CircuitSetup/Time-Circuits-Display/Images/enclosure_sanding2.jpg

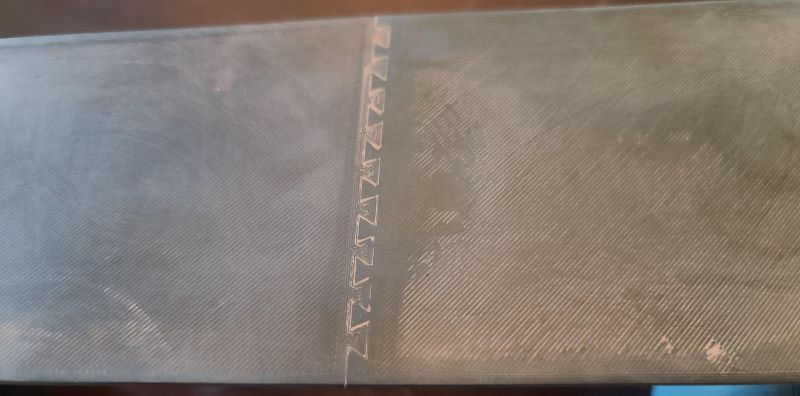
Images/enclosure_sanding2.jpg
