CircuitSetup/Time-Circuits-Display/Images/enclosure_sanding.jpg

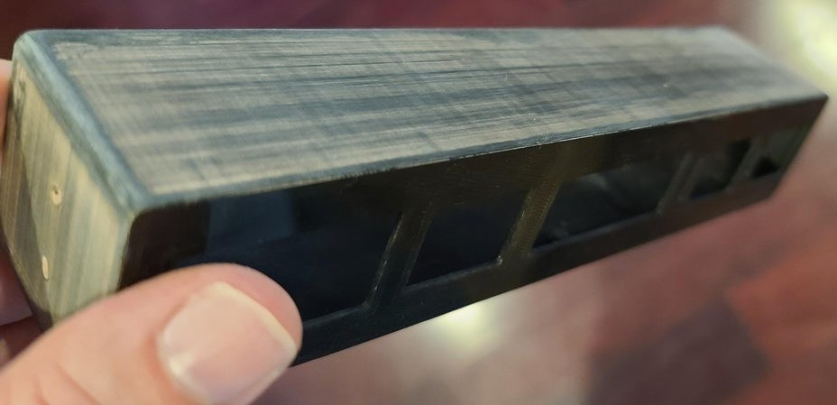
Images/enclosure_sanding.jpg
