CircuitSetup/Time-Circuits-Display/Images/keypad_enter_button.jpg

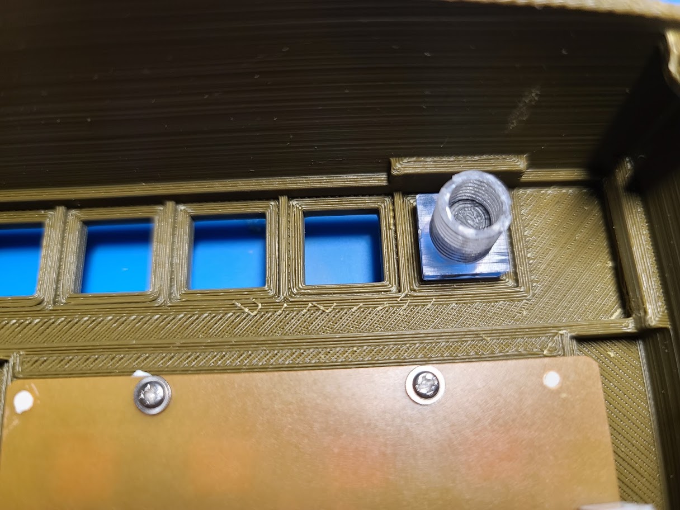
Images/keypad_enter_button.jpg
