CircuitSetup/Time-Circuits-Display/Images/keypad_lenses.jpg

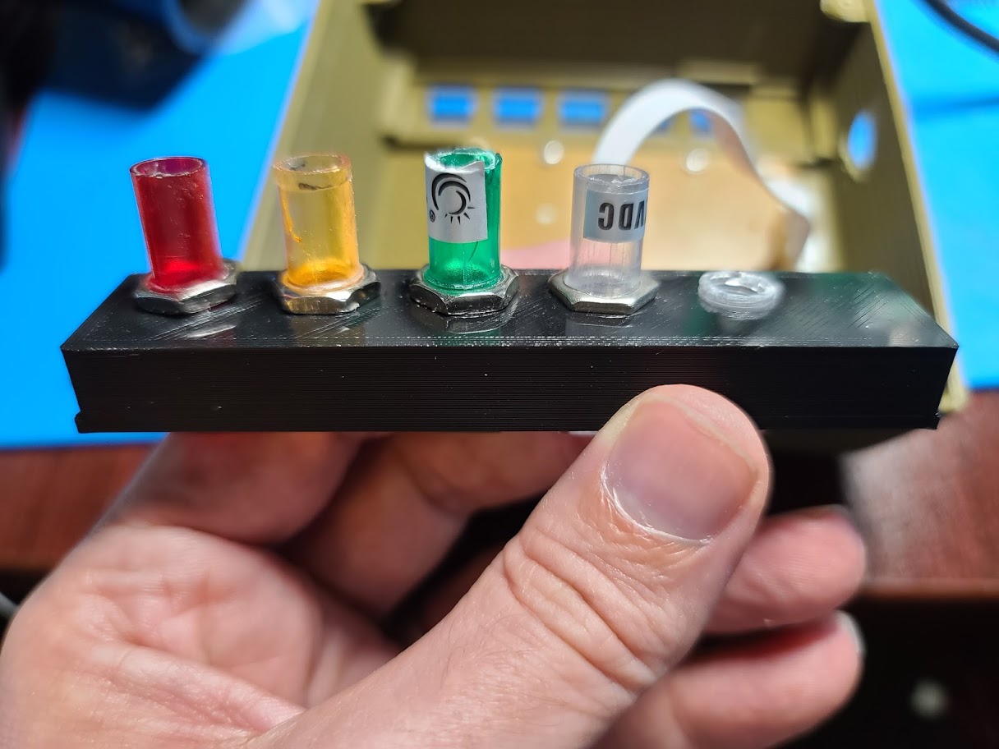
Images/keypad_lenses.jpg
