CircuitSetup/Time-Circuits-Display/Images/resize/enclosure_sanding.jpg

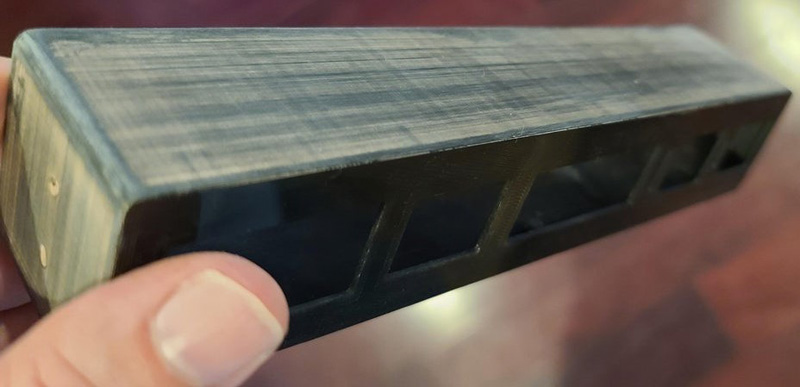
Images/resize/enclosure_sanding.jpg
