CircuitSetup/Time-Circuits-Display/Images/resize/tcd_back2.jpg

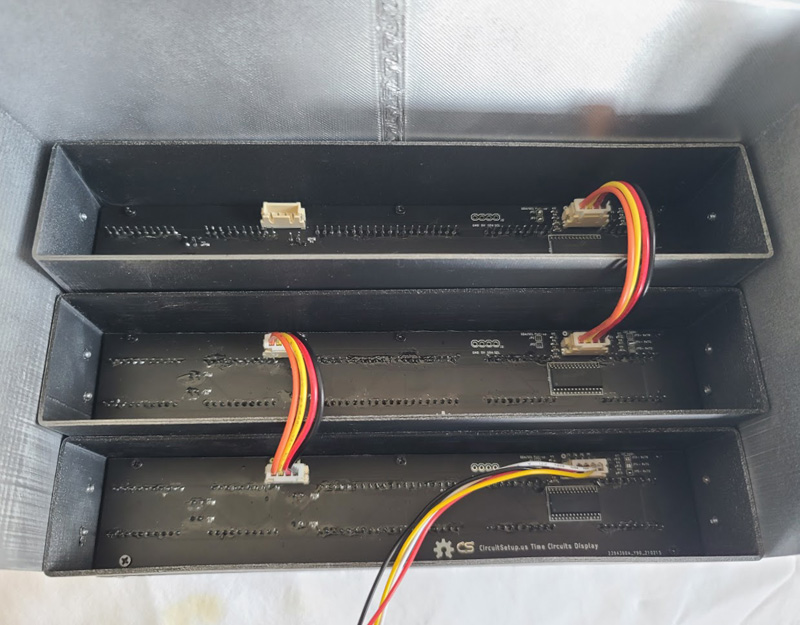
Images/resize/tcd_back2.jpg
