CircuitSetup/Time-Circuits-Display/Images/resize/tcd_bare.jpg

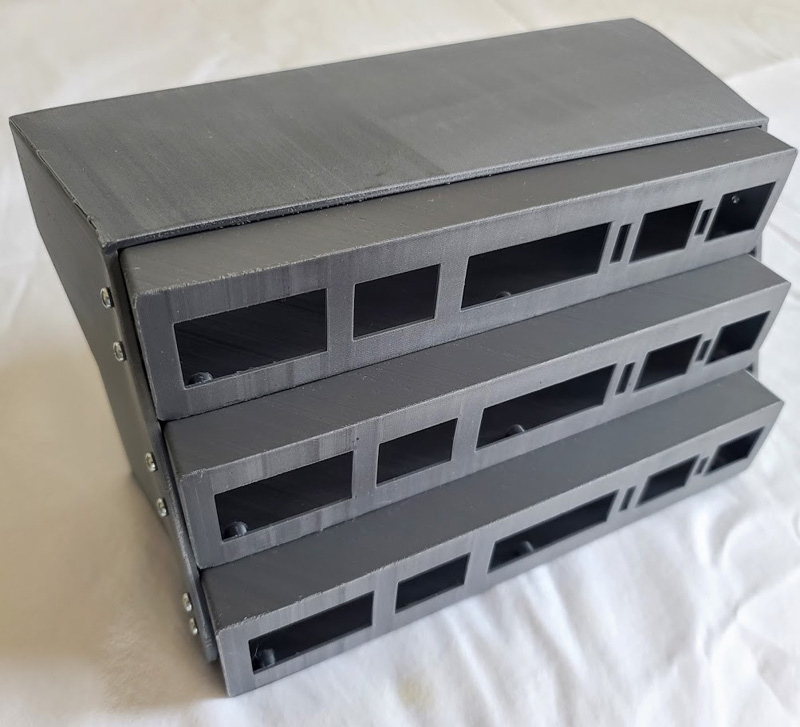
Images/resize/tcd_bare.jpg
