CircuitSetup/Time-Circuits-Display/Images/resize/tcd_bare_back.jpg

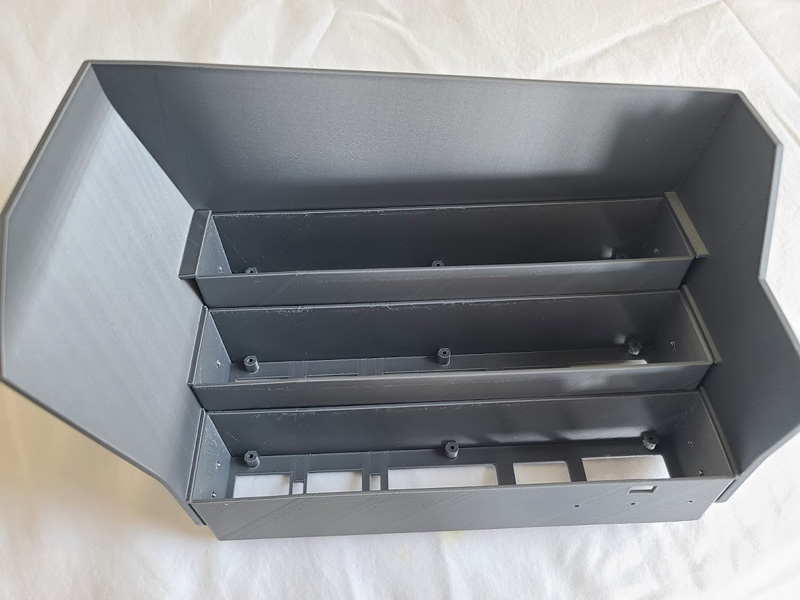
Images/resize/tcd_bare_back.jpg
