CircuitSetup/Time-Circuits-Display/Images/resize/tcd_controller1.jpg

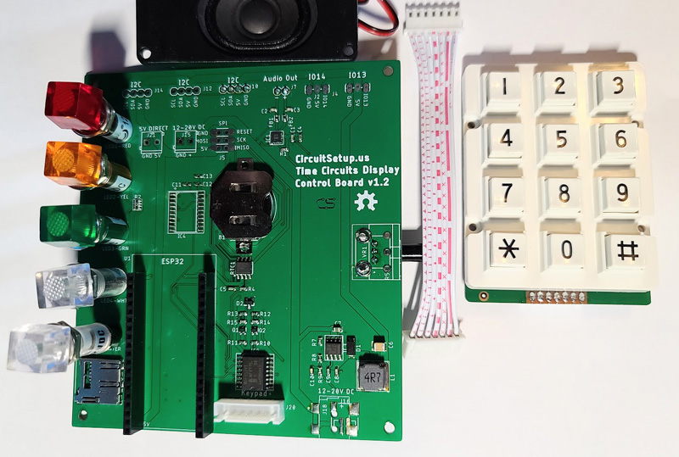
Images/resize/tcd_controller1.jpg
