CircuitSetup/Time-Circuits-Display/Images/resize/tcd_controller2.jpg

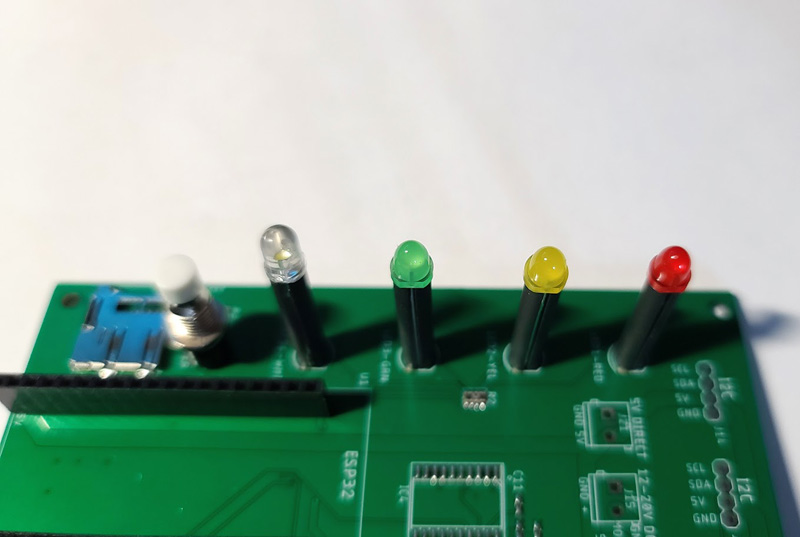
Images/resize/tcd_controller2.jpg
