CircuitSetup/Time-Circuits-Display/Images/resize/tcd_controller_back.jpg

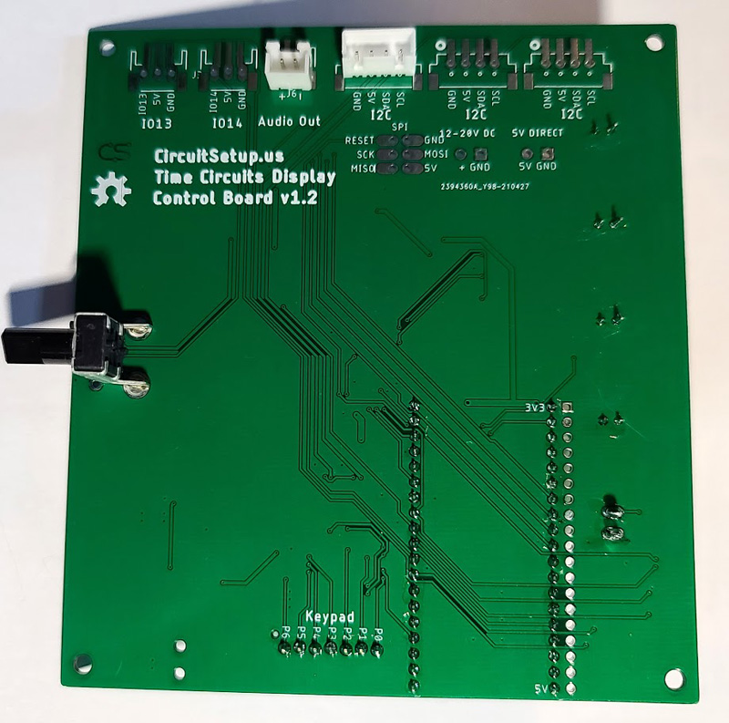
Images/resize/tcd_controller_back.jpg
