CircuitSetup/Time-Circuits-Display/Images/resize/tcd_faceplates.jpg

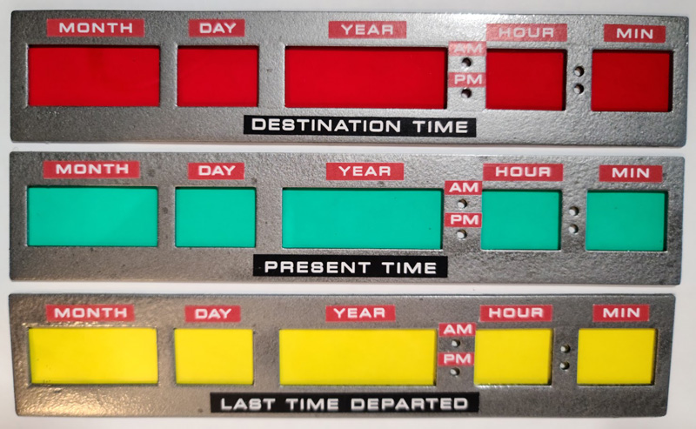
Images/resize/tcd_faceplates.jpg
