CircuitSetup/Time-Circuits-Display/Images/resize/tcd_front2.jpg

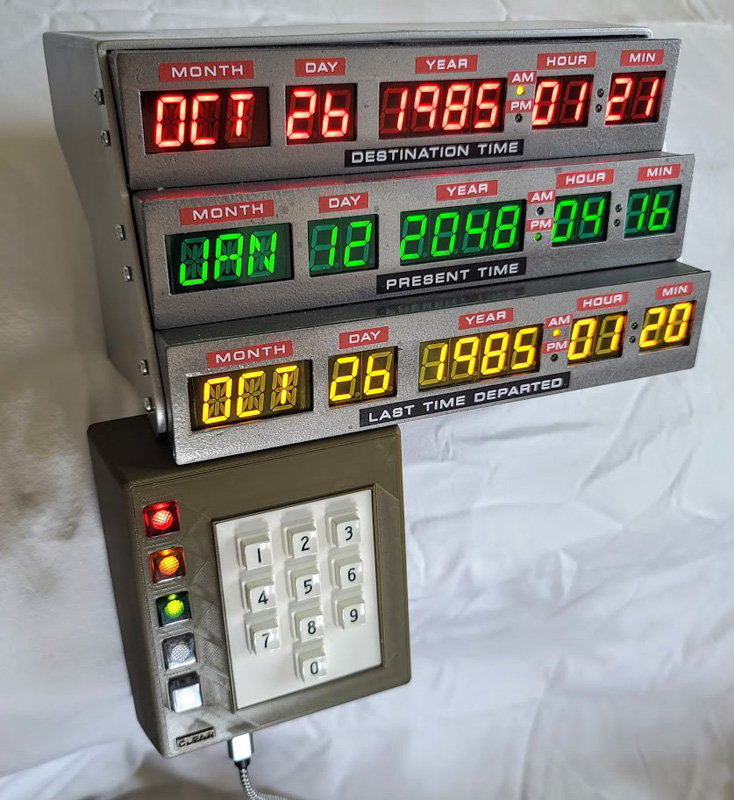
Images/resize/tcd_front2.jpg
