CircuitSetup/Time-Circuits-Display/Images/resize/tcd_front3.jpg

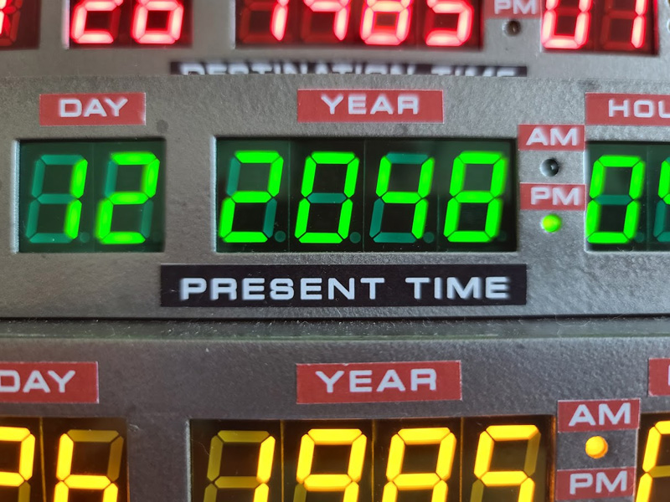
Images/resize/tcd_front3.jpg
