CircuitSetup/Time-Circuits-Display/Images/resize/tcd_front4.jpg

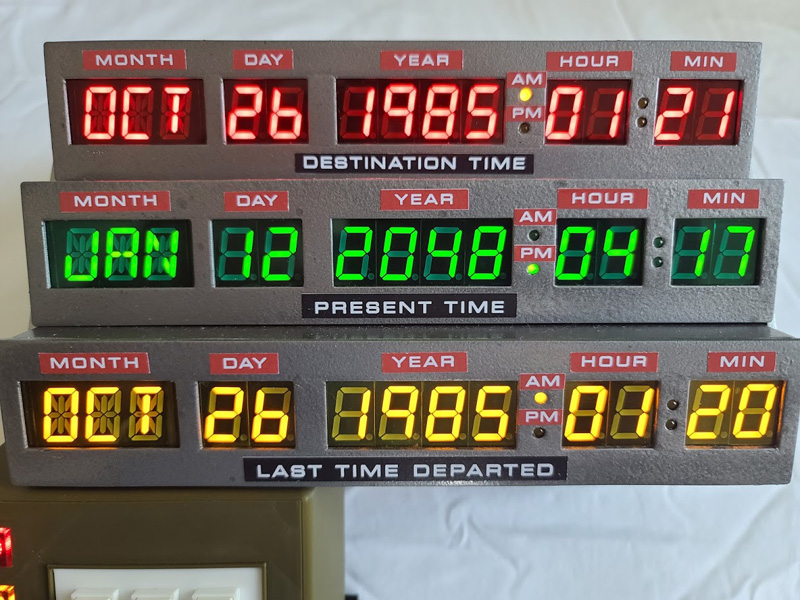
Images/resize/tcd_front4.jpg
