CircuitSetup/Time-Circuits-Display/Images/resize/tcd_front.jpg

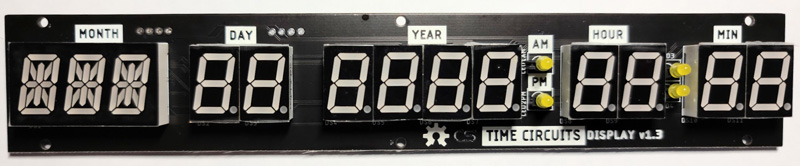
Images/resize/tcd_front.jpg
