CircuitSetup/Time-Circuits-Display/Images/resize/tcd_keypad.jpg

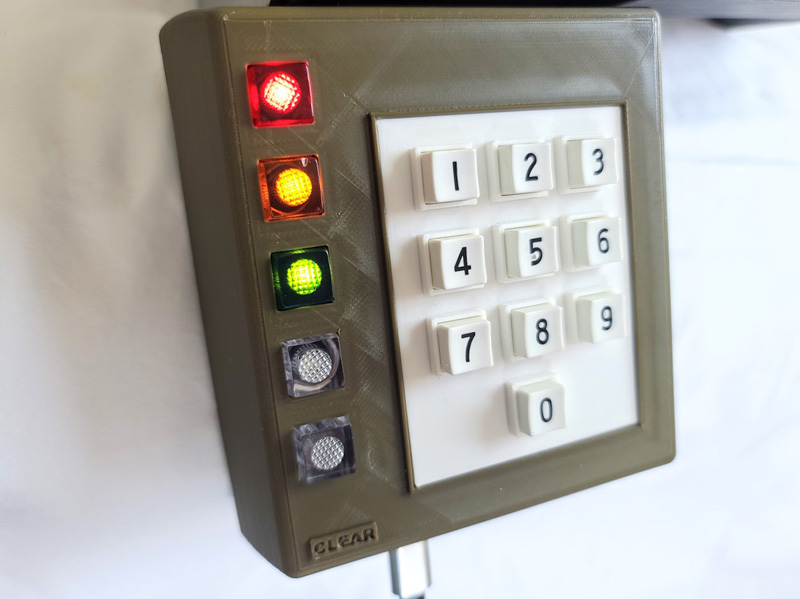
Images/resize/tcd_keypad.jpg
