CircuitSetup/Time-Circuits-Display/Images/resize/tcd_keypad_mount.jpg

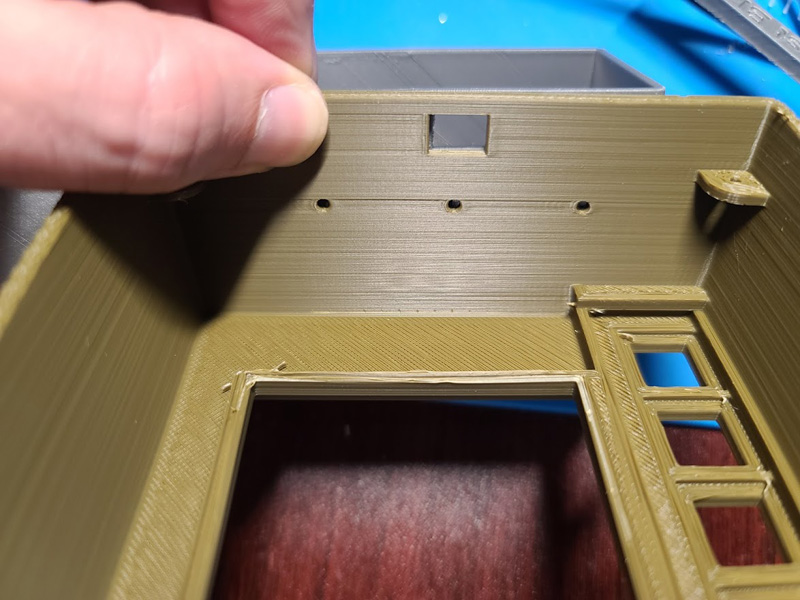
Images/resize/tcd_keypad_mount.jpg
