CircuitSetup/Time-Circuits-Display/Images/resize/tcd_keypad_numbers.jpg

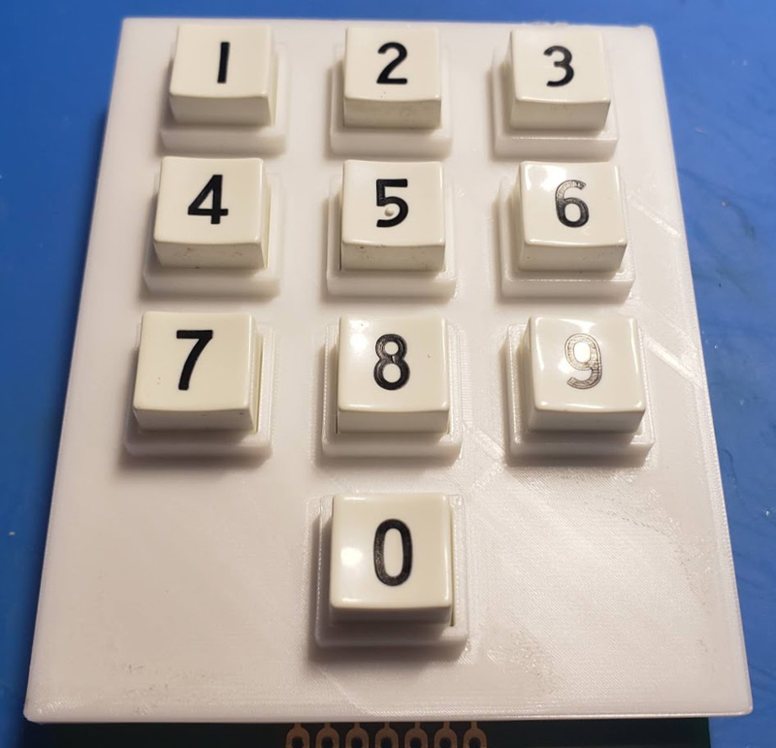
Images/resize/tcd_keypad_numbers.jpg
