CircuitSetup/Time-Circuits-Display/Images/resize/tcd_keypad_numbers_back.jpg

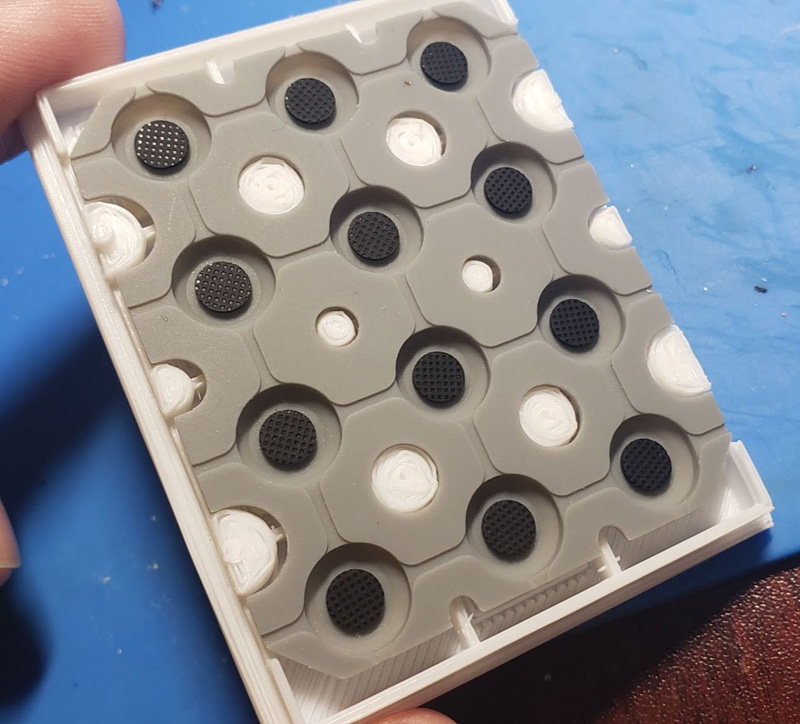
Images/resize/tcd_keypad_numbers_back.jpg
