CircuitSetup/Time-Circuits-Display/Images/resize/tcd_left.jpg

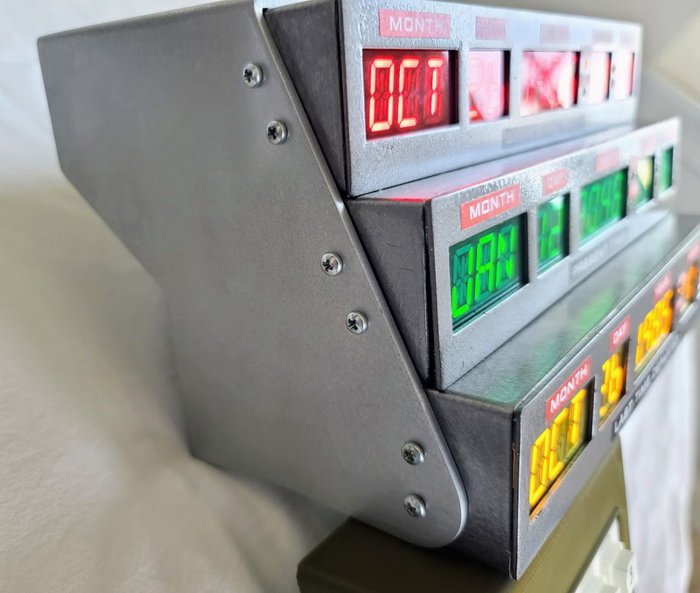
Images/resize/tcd_left.jpg
