CircuitSetup/Time-Circuits-Display/Images/resize/tcd_right.jpg

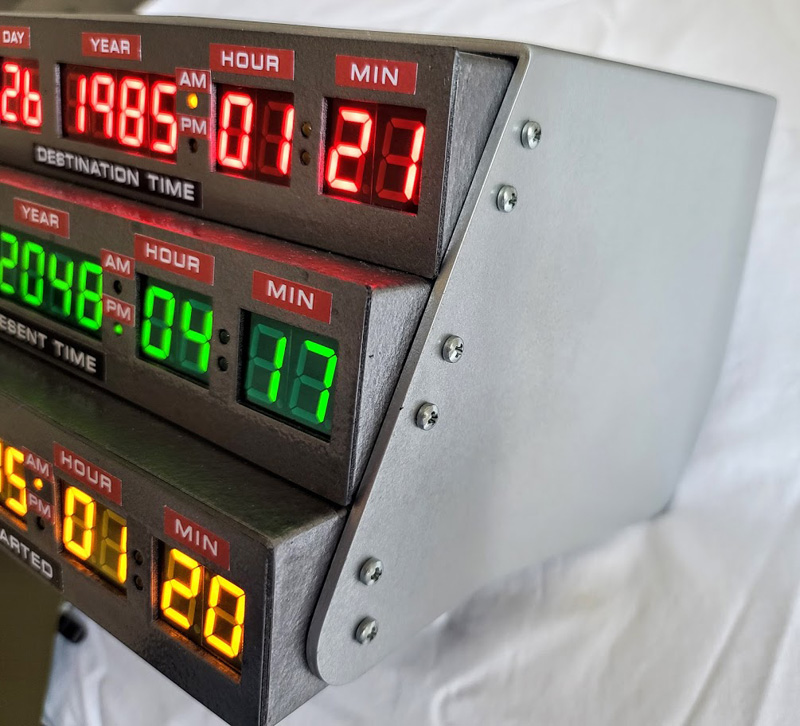
Images/resize/tcd_right.jpg
