CircuitSetup/Time-Circuits-Display/Images/resize/tcd_speaker.jpg

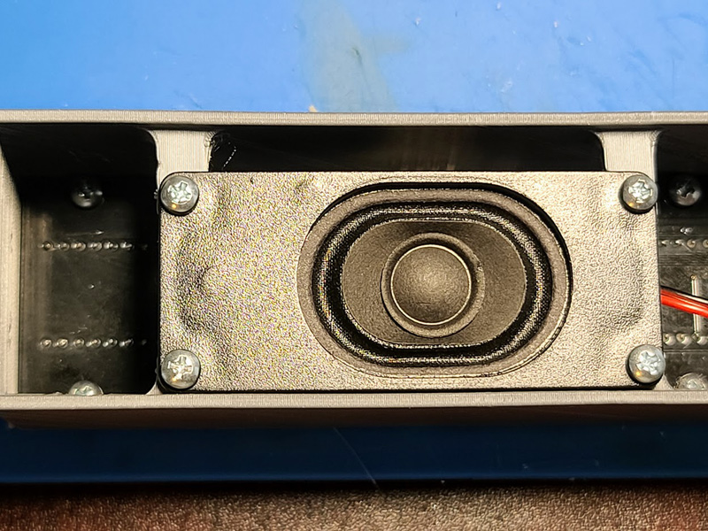
Images/resize/tcd_speaker.jpg
