CircuitSetup/Time-Circuits-Display/Images/resize/tcd_top.jpg

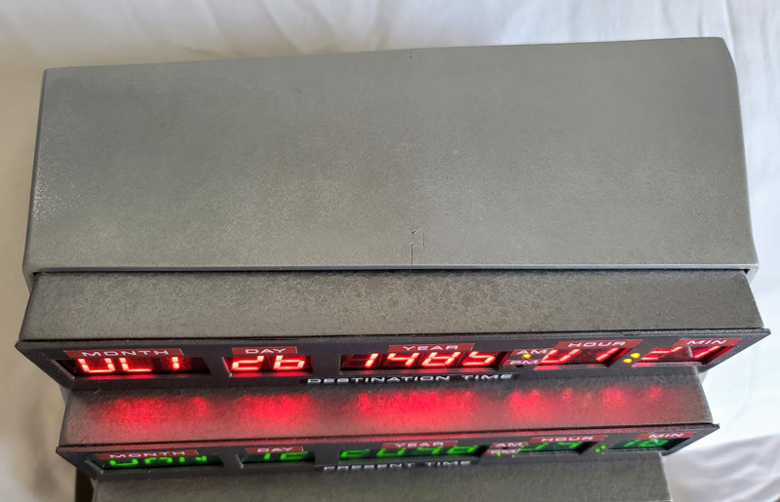
Images/resize/tcd_top.jpg
