CircuitSetup/Time-Circuits-Display/Images/resize/time_circuits_v1.3.jpg

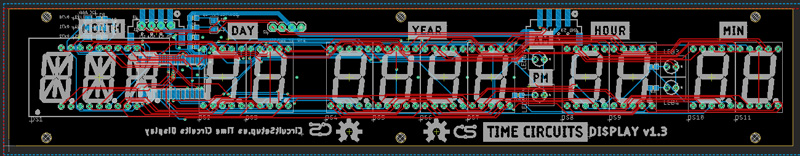
Images/resize/time_circuits_v1.3.jpg
