CircuitSetup/Time-Circuits-Display/Images/tcd_arduino.PNG

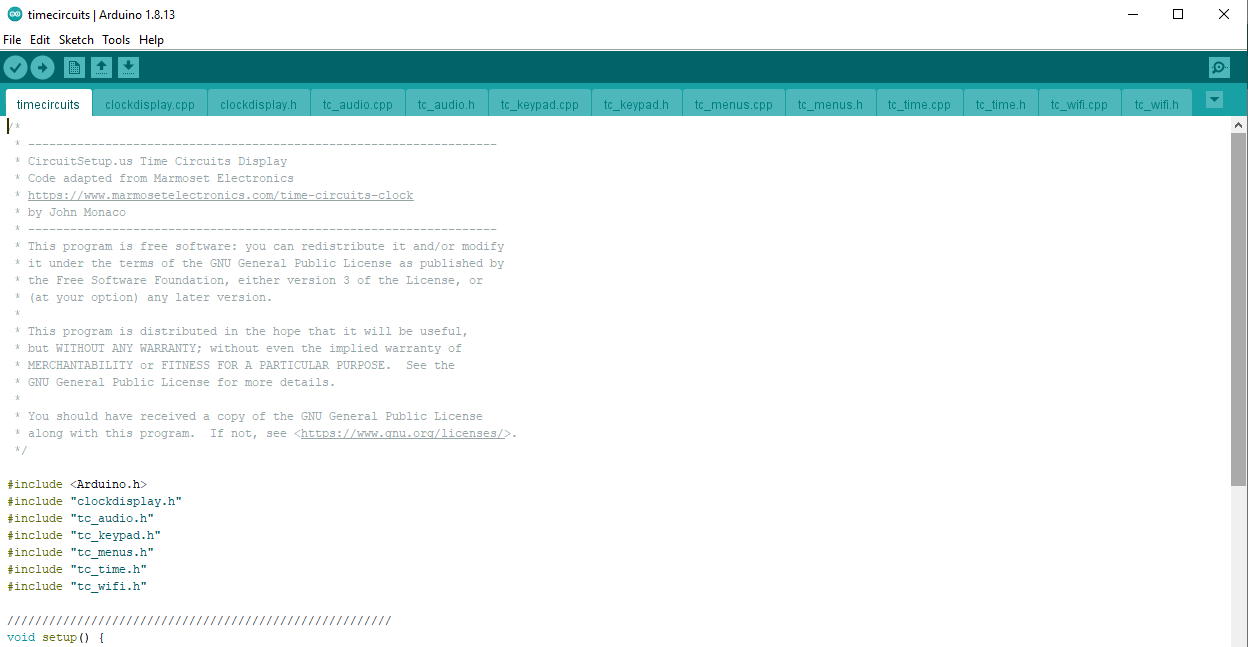
Images/tcd_arduino.PNG
