CircuitSetup/Time-Circuits-Display/Images/tcd_display_lmb_metal2.jpg

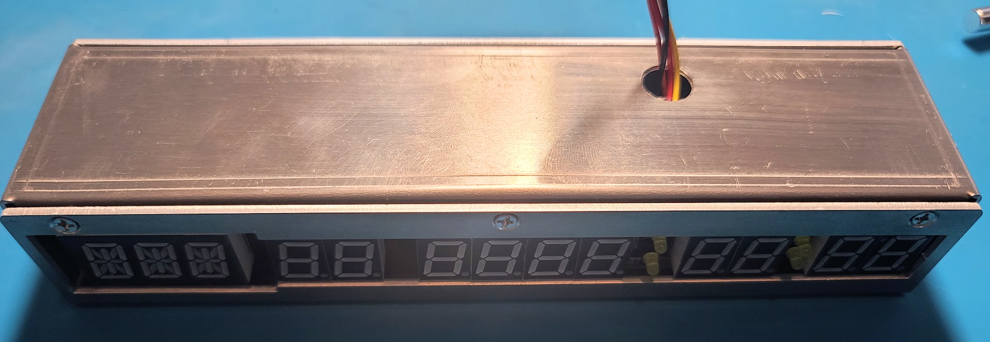
Images/tcd_display_lmb_metal2.jpg
