CircuitSetup/Time-Circuits-Display/Images/tcd_display_lmb_metal.jpg

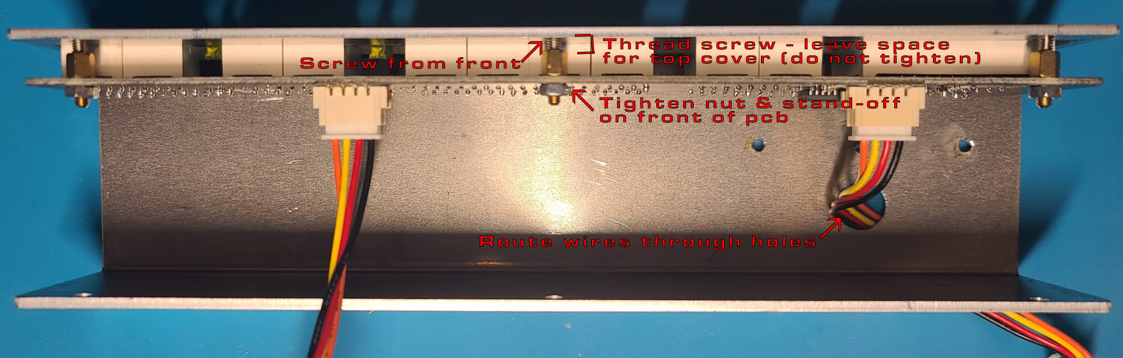
Images/tcd_display_lmb_metal.jpg
