CircuitSetup/Time-Circuits-Display/Images/tcd_firmware_update.PNG

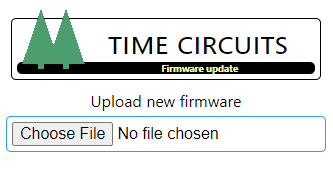
Images/tcd_firmware_update.PNG
