CircuitSetup/Time-Circuits-Display/img/apmode-car.png

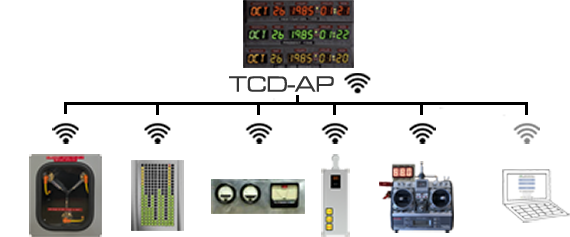
img/apmode-car.png
