CircuitSetup/Time-Circuits-Display/img/family-head.png

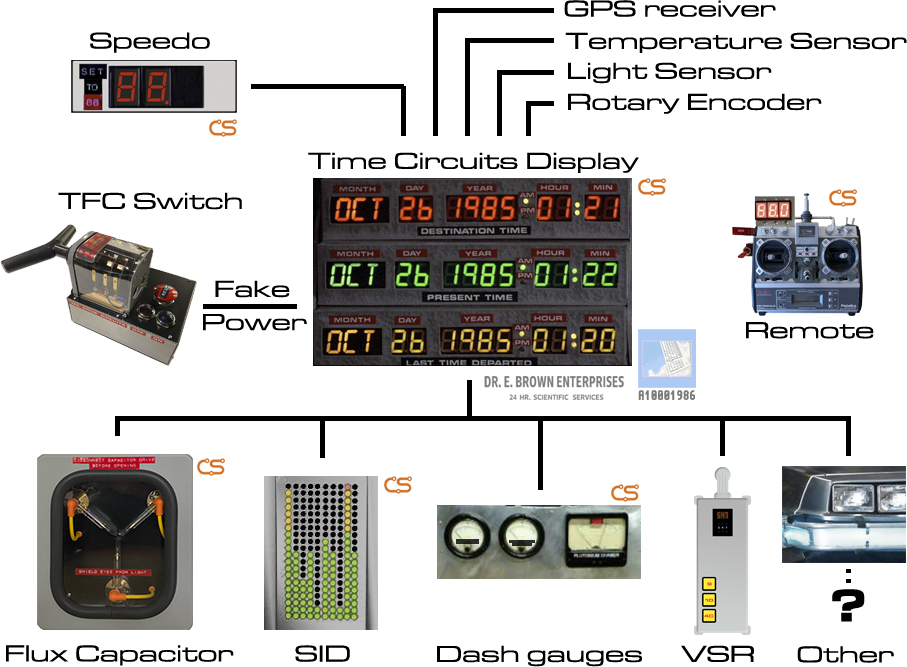
img/family-head.png
