CircuitSetup/Time-Circuits-Display/img/family-wifi-bttfn.png

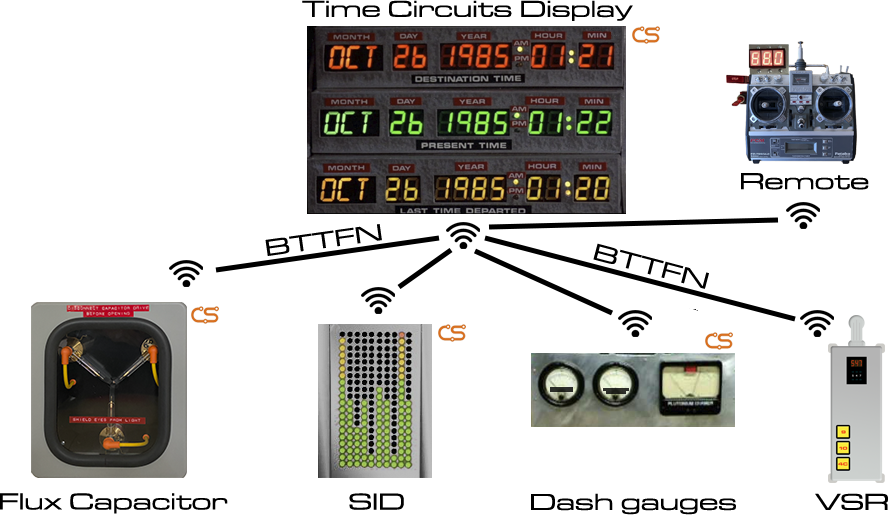
img/family-wifi-bttfn.png
