CircuitSetup/Time-Circuits-Display/img/family-wifi-mqtt.png

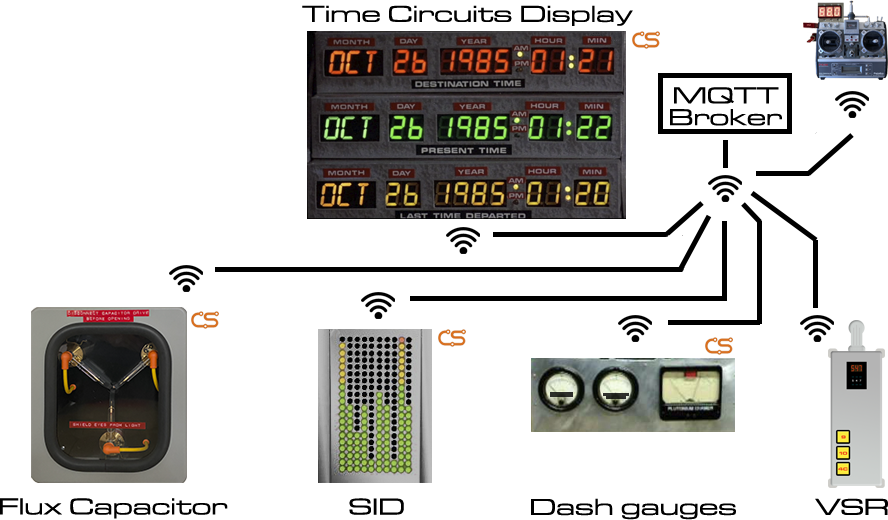
img/family-wifi-mqtt.png
