CircuitSetup/Time-Circuits-Display/img/family-wired.png

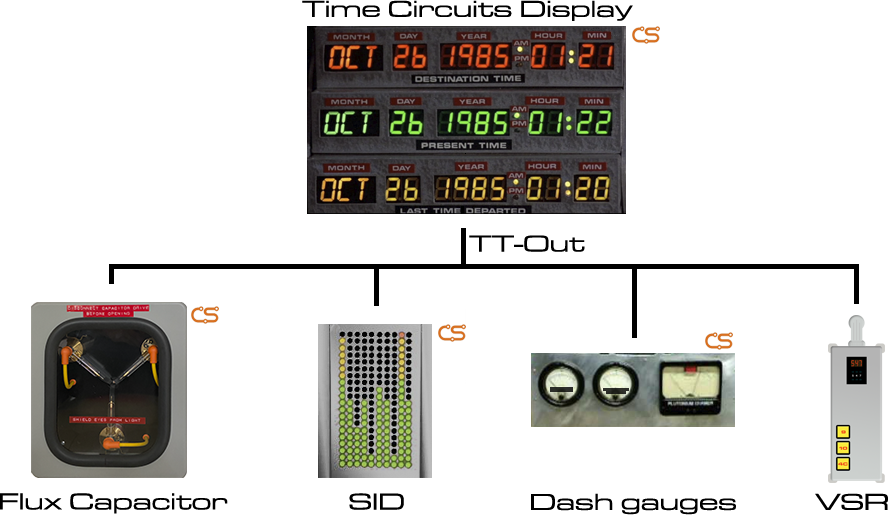
img/family-wired.png
