CircuitSetup/Time-Circuits-Display/img/family-wiredn.png

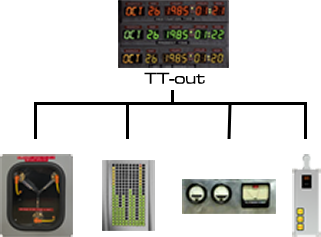
img/family-wiredn.png
