CircuitSetup/Time-Circuits-Display/img/geomode.jpg

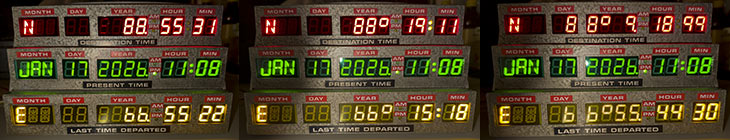
img/geomode.jpg
