CircuitSetup/Time-Circuits-Display/img/mytcd2.jpg

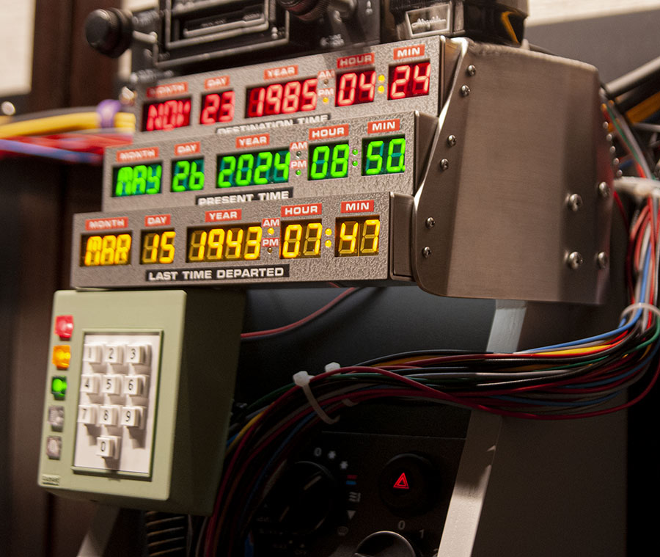
img/mytcd2.jpg
