CircuitSetup/Time-Circuits-Display/img/mytcd2_n.jpg

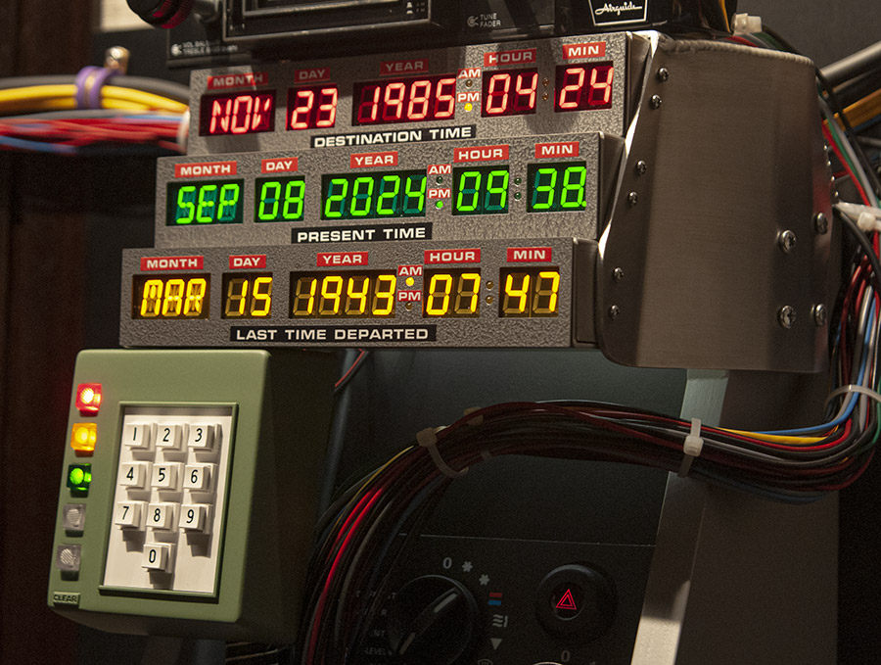
img/mytcd2_n.jpg
