CircuitSetup/Time-Circuits-Display/img/mytcd3.jpg

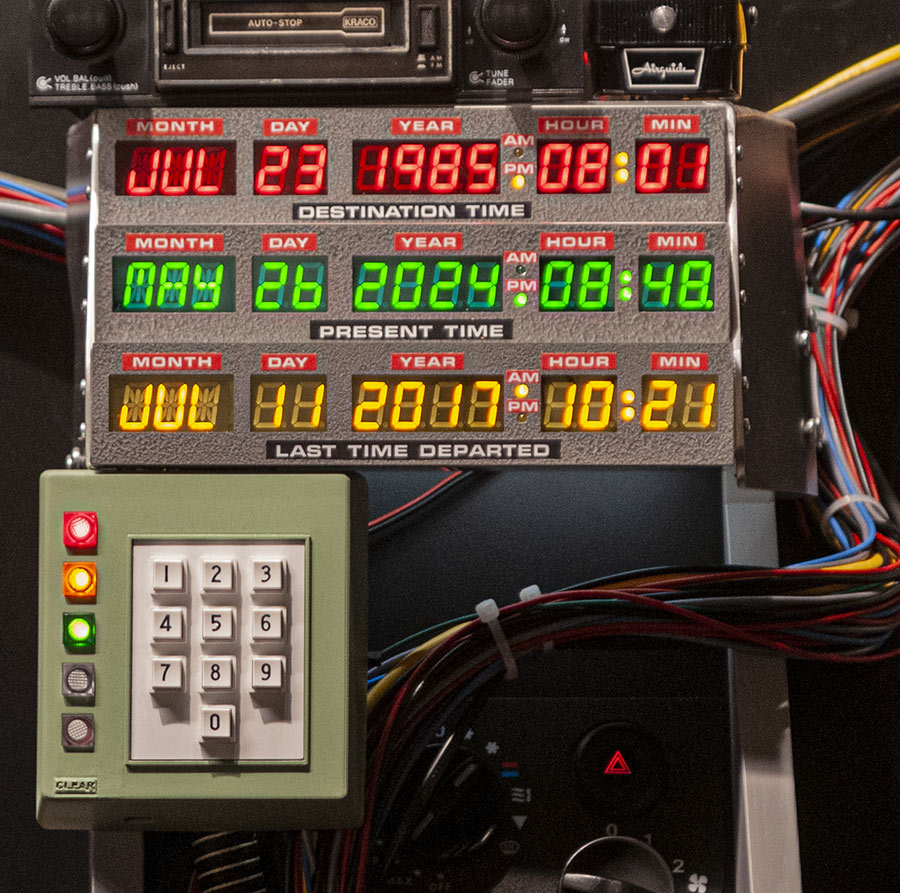
img/mytcd3.jpg
