CircuitSetup/Time-Circuits-Display/img/mytcd3_n.jpg

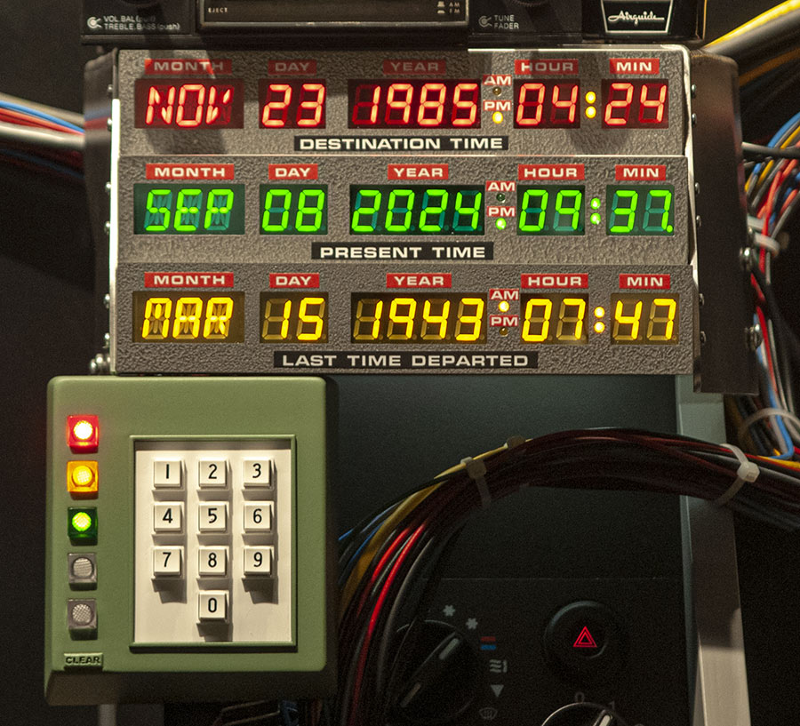
img/mytcd3_n.jpg
