CircuitSetup/Time-Circuits-Display/img/mytcd_n.jpg

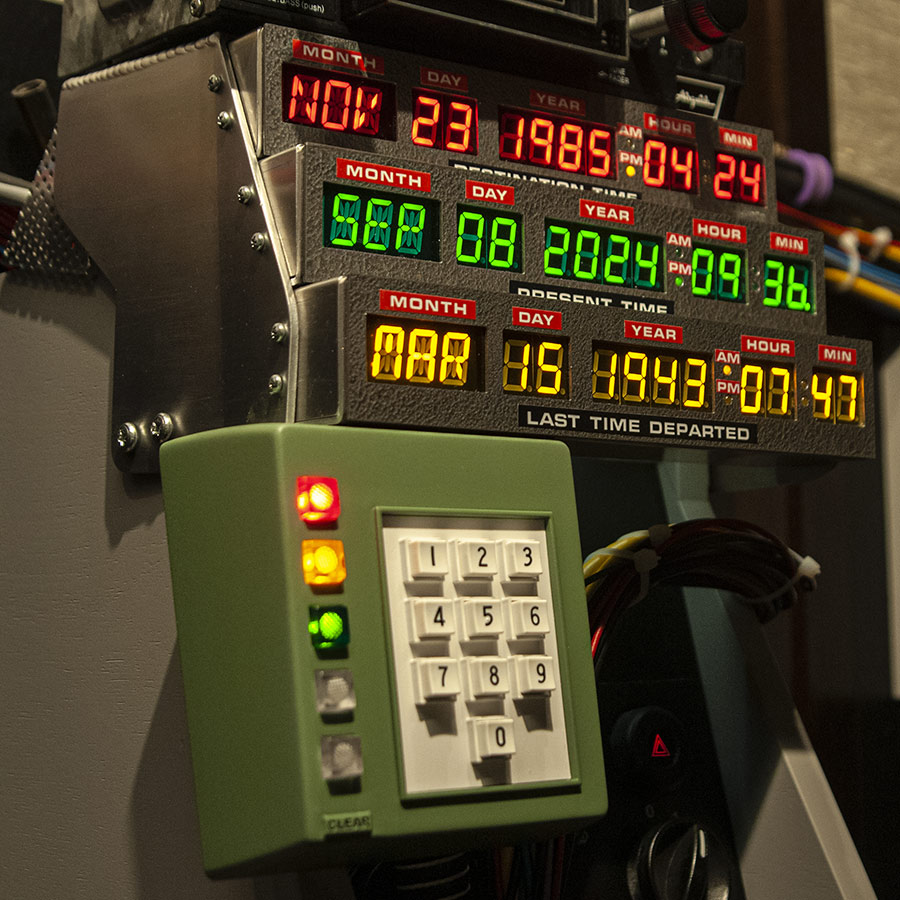
img/mytcd_n.jpg
