CircuitSetup/Time-Circuits-Display/img/orlando.jpg

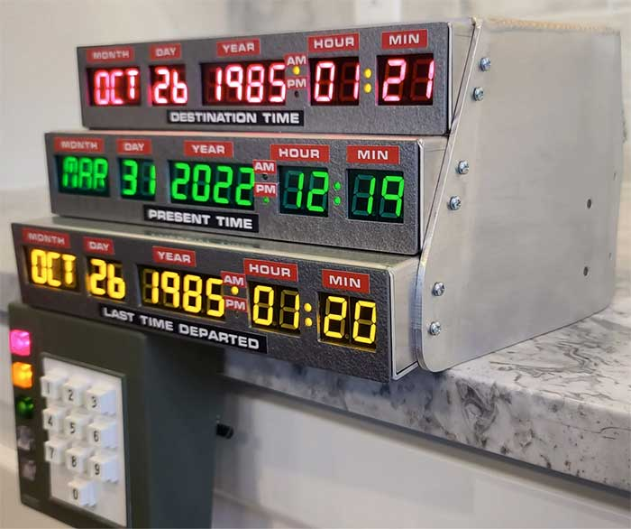
img/orlando.jpg
