CircuitSetup/Time-Circuits-Display/img/speedo_i2c.jpg

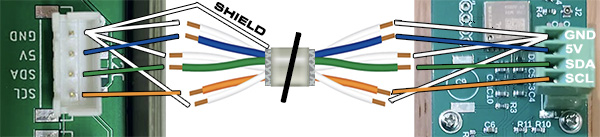
img/speedo_i2c.jpg
