CircuitSetup/Time-Circuits-Display/img/stamode-bttfn.png

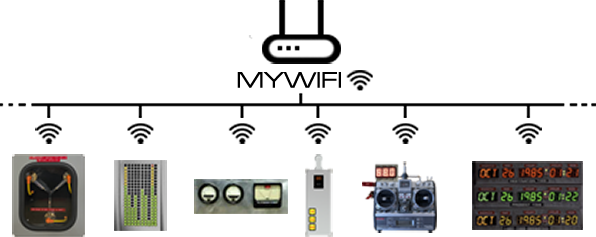
img/stamode-bttfn.png
