CircuitSetup/Time-Circuits-Display/img/stamode-mqtt.png

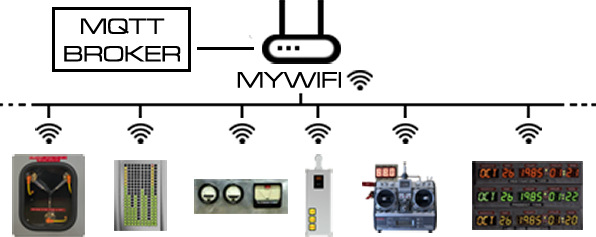
img/stamode-mqtt.png
