CircuitSetup/Time-Circuits-Display/img/tfcswitch.jpg

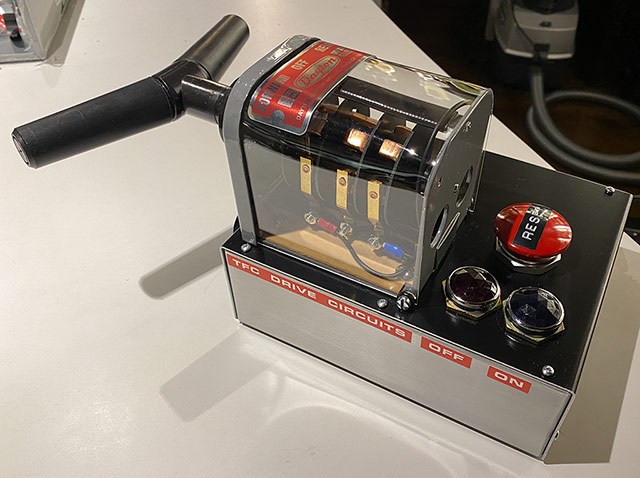
img/tfcswitch.jpg
