CircuitSetup/Time-Circuits-Display/img/ttin12.jpg

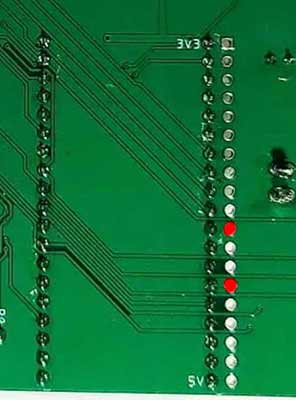
img/ttin12.jpg
