CircuitSetup/Time-Circuits-Display/Hardware/3d Files/time_circuits_faceplate.step

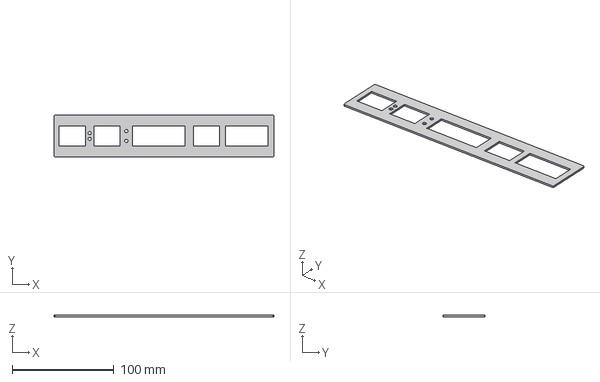
[picture p85: CAD file, 2022-03-16]
Hardware/3d Files/time_circuits_faceplate.step
215.9 x 41.3 x 1.50 mm
