CircuitSetup/Time-Circuits-Display/Hardware/3d Files/cura_keypad_body-v2.3mf

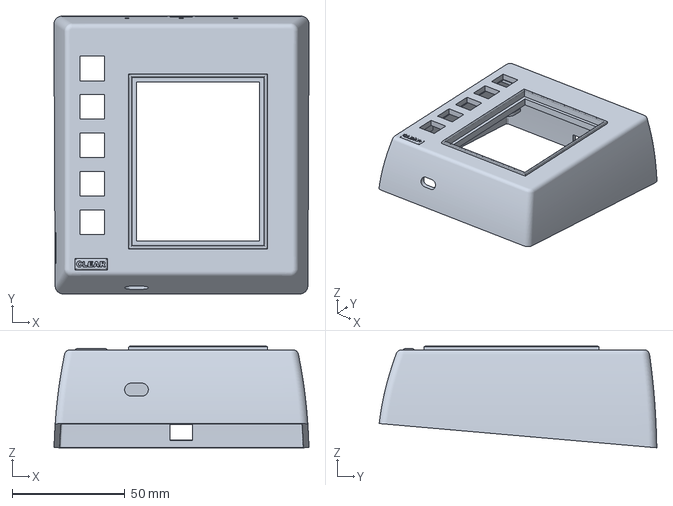
[picture p86: CAD file, 2021-10-15]
Hardware/3d Files/cura_keypad_body-v2.3mf
112.9 x 123.0 x 45.0 mm
