CircuitSetup/Time-Circuits-Display/Hardware/3d Files/cura_keypad_bezel-v2.3mf

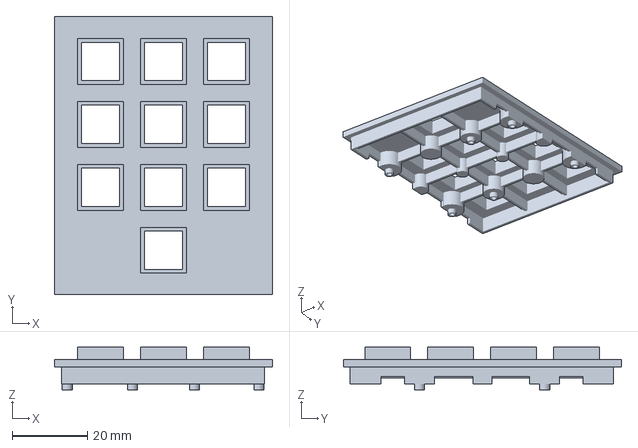
[picture p87: CAD file, 2021-10-15]
Hardware/3d Files/cura_keypad_bezel-v2.3mf
58.0 x 74.0 x 11.4 mm
