CircuitSetup/Time-Circuits-Display/Hardware/3d Files/button_lens_bracket-v2.stl

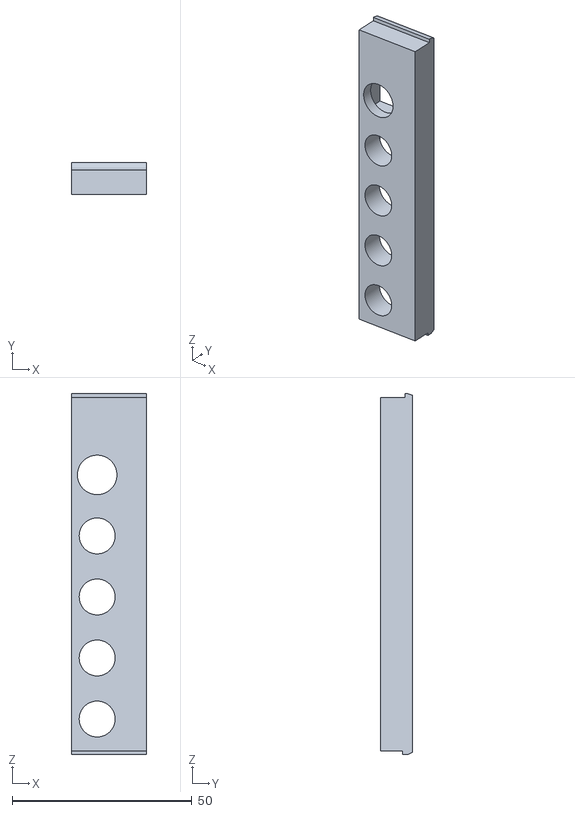
[picture p88: CAD file, 2021-10-13]
Hardware/3d Files/button_lens_bracket-v2.stl
21.0 x 8.95 x 100.6
