CircuitSetup/Time-Circuits-Display/Hardware/3d Files/enclosure_right.stl

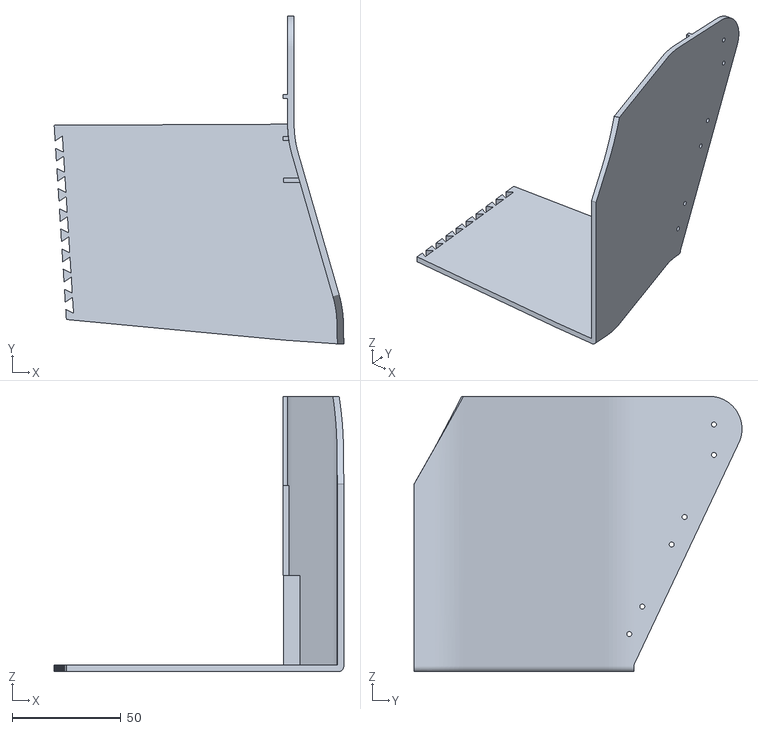
[picture p89: CAD file, 2021-05-26]
Hardware/3d Files/enclosure_right.stl
133.5 x 151.1 x 126.8
