CircuitSetup/Time-Circuits-Display/Hardware/3d Files/enclosure_left.stl

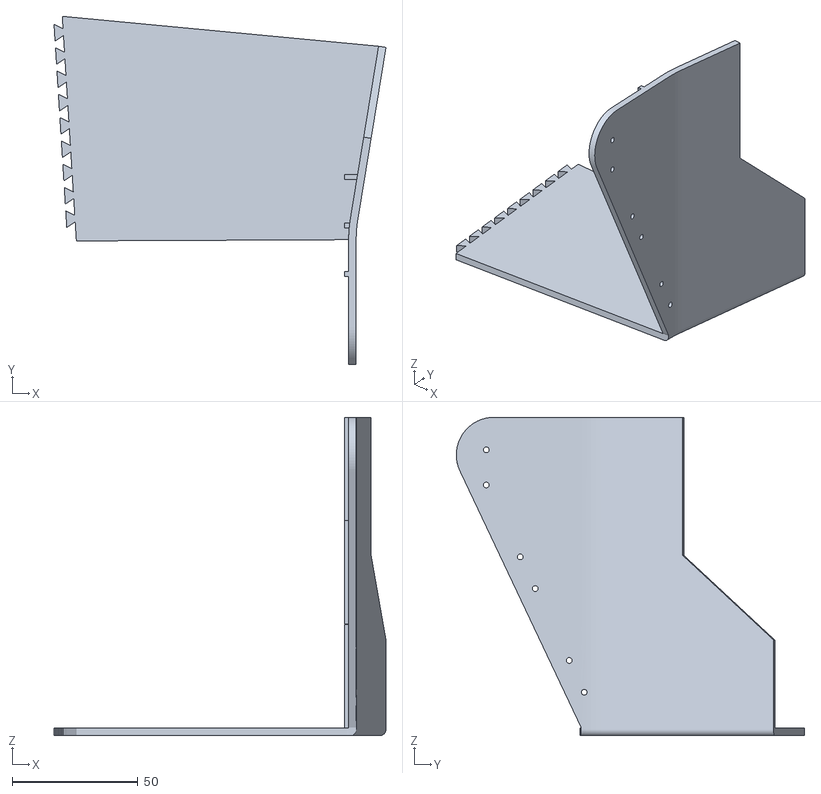
[picture p90: CAD file, 2021-05-26]
Hardware/3d Files/enclosure_left.stl
132.2 x 138.8 x 126.8
