CircuitSetup/Time-Circuits-Display/Hardware/3d Files/enter_button_spacer.stl

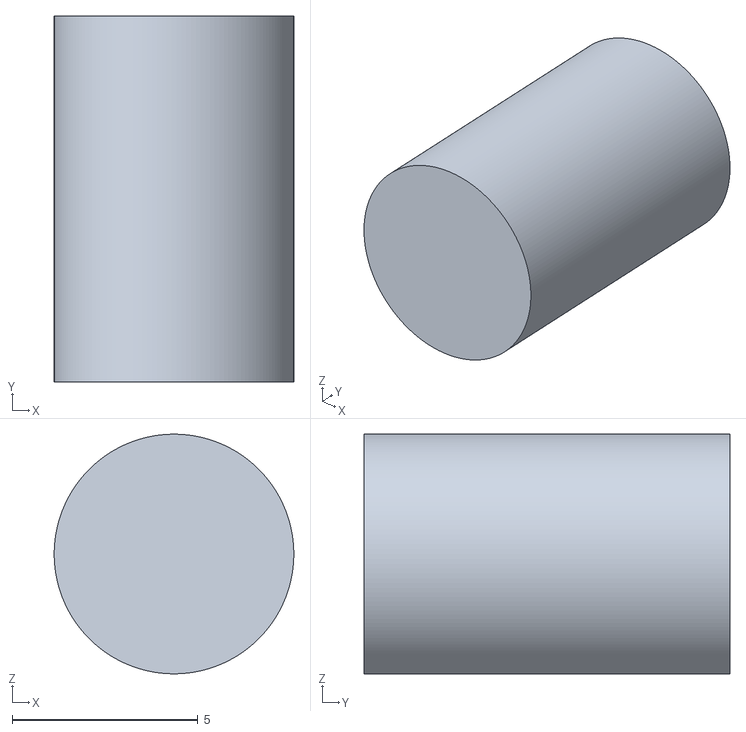
[picture p91: CAD file, 2021-04-10]
Hardware/3d Files/enter_button_spacer.stl
6.45 x 9.85 x 6.45
