CircuitSetup/Time-Circuits-Display/Images/keypad_print.jpg

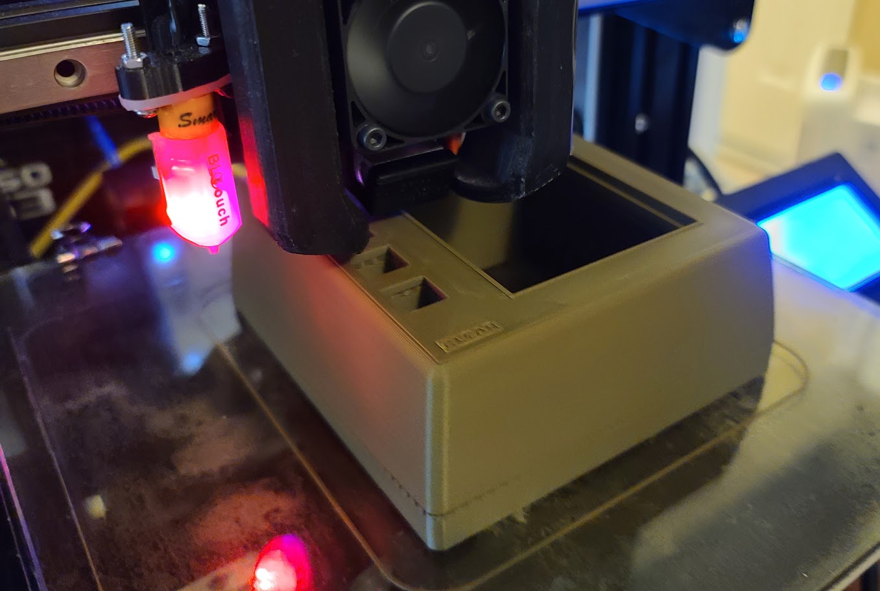
Images/keypad_print.jpg
