CircuitSetup/Time-Circuits-Display/Images/resize/tcd_keypad_disassemble.jpg

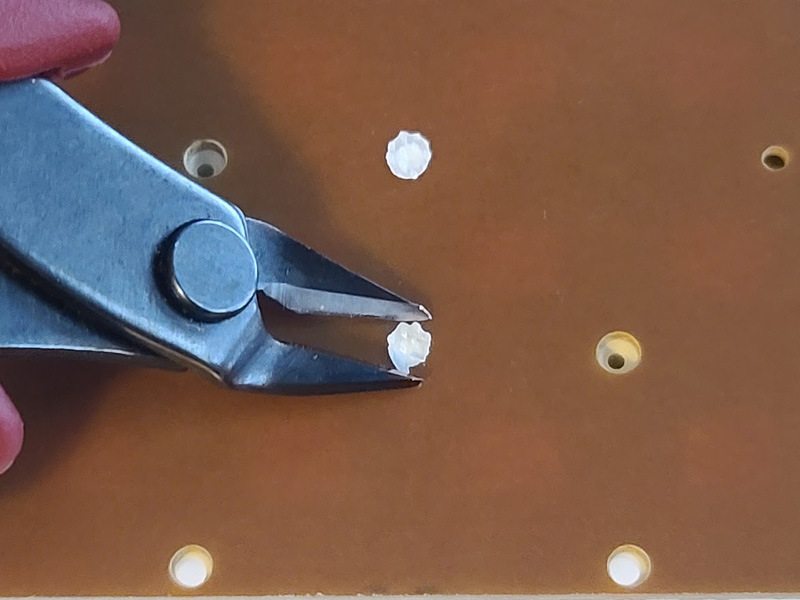
Images/resize/tcd_keypad_disassemble.jpg
