CircuitSetup/Time-Circuits-Display/img/cp_setup.png

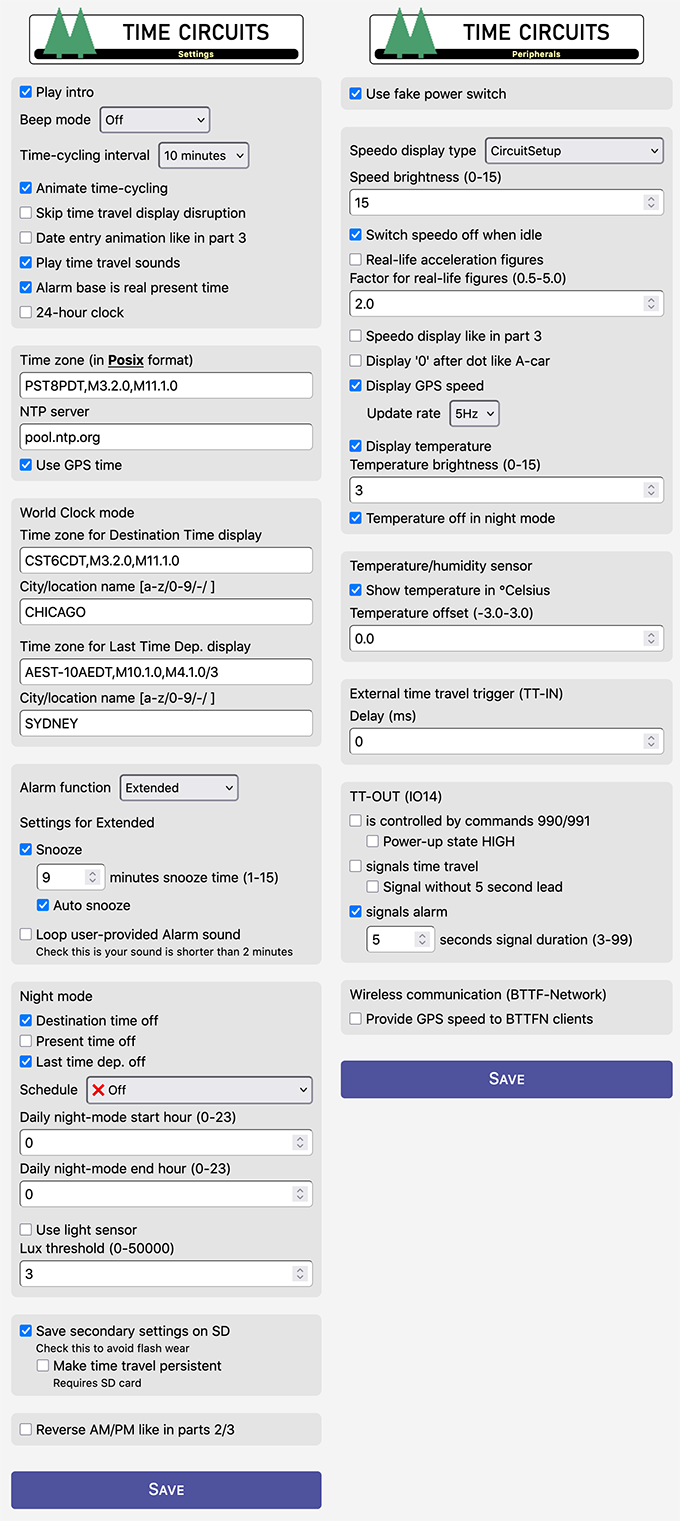
img/cp_setup.png
