CircuitSetup/Time-Circuits-Display/Software/src/tc_main.cpp

/*
 * -------------------------------------------------------------------
 * CircuitSetup.us Time Circuits Display
 * (C) 2021-2022 John deGlavina https://circuitsetup.us
 * (C) 2022-2026 Thomas Winischhofer (A10001986)
 * https://github.com/realA10001986/Time-Circuits-Display
 * https://tcd.out-a-ti.me
 *
 * Main Controller
 *
 * -------------------------------------------------------------------
 * License: Modified MIT NON-AI
 * 
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
 * Links inside the Software pointing to the original source must not 
 * be changed or removed.
 *
 * In addition, the following restrictions apply:
 * 
 * 1. The Software and any modifications made to it may not be used 
 * for the purpose of training or improving machine learning algorithms, 
 * including but not limited to artificial intelligence, natural 
 * language processing, or data mining. This condition applies to any 
 * derivatives, modifications, or updates based on the Software code. 
 * Any usage of the Software in an AI-training dataset is considered a 
 * breach of this License.
 *
 * 2. The Software may not be included in any dataset used for 
 * training or improving machine learning algorithms, including but 
 * not limited to artificial intelligence, natural language processing, 
 * or data mining.
 *
 * 3. Any person or organization found to be in violation of these 
 * restrictions will be subject to legal action and may be held liable 
 * for any damages resulting from such use.
 *
 * THE SOFTWARE IS PROVIDED "AS IS", WITHOUT WARRANTY OF ANY KIND, 
 * EXPRESS OR IMPLIED, INCLUDING BUT NOT LIMITED TO THE WARRANTIES OF 
 * MERCHANTABILITY, FITNESS FOR A PARTICULAR PURPOSE AND NONINFRINGEMENT. 
 * IN NO EVENT SHALL THE AUTHORS OR COPYRIGHT HOLDERS BE LIABLE FOR ANY 
 * CLAIM, DAMAGES OR OTHER LIABILITY, WHETHER IN AN ACTION OF CONTRACT, 
 * TORT OR OTHERWISE, ARISING FROM, OUT OF OR IN CONNECTION WITH THE 
 * SOFTWARE OR THE USE OR OTHER DEALINGS IN THE SOFTWARE.
 */

#include "tc_global.h"

#include <Arduino.h>
#include <time.h>
#include <WiFi.h>
#include <Wire.h>
#include <Udp.h>
#include <WiFiUdp.h>

#include "tc_keypad.h"
#include "tc_audio.h"
#include "tc_wifi.h"
#include "tc_settings.h"
#if defined(HAVE_RE) || defined(HAVE_REMOTE)
#include "input.h"
#endif

#include "tc_main.h"

// i2c slave addresses

#define DEST_TIME_ADDR 0x71 // TC displays
#define PRES_TIME_ADDR 0x72
#define DEPT_TIME_ADDR 0x74

#define KEYPAD_ADDR    0x20 // PCF8574 port expander (keypad) (redefined in keypad.cpp, here only for completeness)

#define DS3231_ADDR    0x68 // DS3231 RTC
#define PCF2129_ADDR   0x51 // PCF2129 RTC

#define SPEEDO_ADDR    0x70 // speedo display

#define GPS_MTK_ADDR   0x10 // GPS receiver (MTK3333)

                            // temperature sensors
#define MCP9808_ADDR   0x18 // [default]
#define BMx280_ADDR    0x77 // [default]
#define SHT40_ADDR     0x44 // Only SHT4x-Axxx, not SHT4x-Bxxx
#define SI7021_ADDR    0x40 //
#define TMP117_ADDR    0x49 // [non-default]
#define AHT20_ADDR     0x38 //
#define HTU31_ADDR     0x41 // [non-default]
#define MS8607_ADDR    0x76 // +0x40
#define HDC302X_ADDR   0x45 // [non-default]

                            // light sensors 
#define LTR3xx_ADDR    0x29 // [default]                            
#define TSL2561_ADDR   0x29 // [default]
#define TSL2591_ADDR   0x29 // [default]
#define BH1750_ADDR    0x23 // [default]
#define VEML6030_ADDR  0x48 // [non-default] (default 0x10 conflicts with MTK333x-GPS/CS Speedo)
#define VEML7700_ADDR  0x10 // [default] (conflicts with MTK333x-GPS/CS Speedo)

                            // rotary encoders for speed
#define ADDA4991_ADDR  0x36 // [default]
#define DUPPAV2_ADDR   0x01 // [user configured: A0 closed]
#define DFRGR360_ADDR  0x54 // [default; SW1=0, SW2=0]

                            // rotary encoders for volume
#define ADDA4991V_ADDR 0x37 // [non-default: A0 closed]
#define DUPPAV2V_ADDR  0x03 // [user configured: A0+A1 closed]
#define DFRGR360V_ADDR 0x55 // [SW1=0, SW2=1]

// The time between reentry sound being started and the display coming on
// Must be sync'd to the sound file used! (startup.mp3/timetravel.mp3)
#ifdef CS_EDITION
#define STARTUP_DELAY 1050
#else
#define STARTUP_DELAY 900
#endif

// Re-entry
#define REENTRY_DURATION 1500 

// Volume-factor for "travelstart" sounds
#define TT_SOUND_FACT 0.60f

// Time between the phases of (long) time travel
// Sum of all must be 8000
#define TT_P1_TOTAL     8000
#define TT_P1_DELAY_P1  1400                                                                        // Normal
#define TT_P1_DELAY_P2  (4200-TT_P1_DELAY_P1)                                                       // Light flicker
#define TT_P1_DELAY_P3  (5800-(TT_P1_DELAY_P2+TT_P1_DELAY_P1))                                      // Off
#define TT_P1_DELAY_P4  (6800-(TT_P1_DELAY_P3+TT_P1_DELAY_P2+TT_P1_DELAY_P1))                       // Random display I
#define TT_P1_DELAY_P5  (TT_P1_TOTAL-(TT_P1_DELAY_P4+TT_P1_DELAY_P3+TT_P1_DELAY_P2+TT_P1_DELAY_P1)) // Random display II
// ACTUAL POINT OF TIME TRAVEL:
#define TT_P1_POINT88   1400    // ms into "starttravel" sample, when 88mph is reached.
#define TT_P1_EXT       TT_P1_TOTAL - TT_P1_DELAY_P1   // part of P1 between P0 and P2

// Speedo display status
#define SPST_NIL  0
#define SPST_GPS  1
#define SPST_RE   2
#define SPST_TEMP 3
#define SPST_ZERO 4
#define SPST_REM  5

// Preprocessor config for External Time Travel Output (ETTO):
// Lead time from trigger (LOW->HIGH) to actual tt (ie when 88mph is reached)
// The external prop has ETTO_LEAD_TIME ms to play its pre-tt sequence. After
// ETTO_LEAD_TIME ms, 88mph is reached, and the actual tt takes place.
#define ETTO_LEAD_TIME      5000
#define ETTO_LAT              50  // DO NOT CHANGE

// Native NTP
#define NTP_PACKET_SIZE 48
#define NTP_DEFAULT_LOCAL_PORT 1337

#define SECS1900_1970 2208988800ULL

// Temperature update intervals
#define TEMP_UPD_INT_L (2*60*1000)
#define TEMP_UPD_INT_S (30*1000)

bool                 showUpdAvail = true;

// deferredCP = true: Start CP later; 
//            =false: Start CP at connect
uint32_t             schf = SCHF_DEFERREDCP;

// millis64
static unsigned long lastMillis64 = 0;
static uint32_t      millisEpoch = 0;

static int           couldHaveAuthTime = 0;
static bool          haveAuthTime = false;
uint16_t             lastYear = 0;
static uint8_t       lastHour = 23;
static uint8_t       resyncInt = 5;
unsigned long        syncTrigger = 0;
bool                 doAPretry = true;

static unsigned long deferredCPNow = 0;

// For tracking second changes
static bool          x = false;  
static bool          y = false;

// For beep-auto-modes
uint8_t              beepMode = DEF_BEEP;
unsigned long        beepTimer = 0;
unsigned long        beepTimeout = 30*1000;

// Speech
static int pbcnt = 0, ppbt = -2, phm = -1;

// Persistent time travels
bool    timetravelPersistent = false;

// Alarm
bool    alarmOnOff                  = DEF_ALARM_ONOFF;
uint8_t alarmHour                   = DEF_ALARM_HOUR;
uint8_t alarmMinute                 = DEF_ALARM_MINUTE;
uint8_t alarmWeekday                = DEF_ALARM_WD;
#define ALARM_PLAY_DUR 2*60*1000
uint32_t             alf            = 0;
unsigned long        alarmPlaying   = 0;
static unsigned long alarmPlayDur   = 0;
static unsigned long snoozeTime     = 9;
static unsigned long snoozeNow      = 0;
static unsigned long origAlarmStart = 0;

// Alarm weekday masks
static const uint8_t alarmWDmasks[10] = { 
    0b01111111, 0b00111110, 0b01000001, 0b00000010, 0b00000100,
    0b00001000, 0b00010000, 0b00100000, 0b01000000, 0b00000001
};

// Timer, Alarm, Reminder, SotH
static uint32_t sigFlags = 0;
#define SF_TQ  (1 << 0)
#define SF_AQ  (1 << 1)
#define SF_ARQ (1 << 2)
#define SF_AD  (1 << 3)
#define SF_SQ  (1 << 4)
#define SF_RQ  (1 << 5)
#define SF_RD  (1 << 6)
#define SF_HD  (1 << 7)
#define SF_ALQ (1 << 15)  // Special, only with SF_ARQ

// Alarm via TT-OUT
bool                 ETTOcommands = false;
static bool          ETTOalarm = false;
static unsigned long ETTOAlmDur = DEF_ETTO_ALM_D * 1000;
static unsigned long ETTOAlmNow = 0;

// Speedo & GPS stuff
uint32_t             sgf = 0;
static uint8_t       speedoStatus = SPST_NIL;
static unsigned long timetravelP0Now = 0;
static unsigned long timetravelP0Delay = 0;
static unsigned long ttP0Now = 0;
static int           timeTravelP0Speed = 0;
static long          pointOfP1 = 0;
static long          pointOfP1NoLead = 0;
static float         ttP0TimeFactor = 1.0f;

uint32_t             ttinpin = 0;    // 0=TT_IN,  1=Servo Speedo, 2=Servo Tacho
uint32_t             ttoutpin = 0;   // 0=TT_OUT, 1=Servo Speedo, 2=Servo Tacho

static const char    *preTTSound   = "/ttaccel.mp3";
static const char    *abortTTSound = "/ttcancel.mp3";
static const char    *alarmSound   = "/alarm.mp3";
static uint32_t      haveSnds = 0;
#define HS_PRE_TT    0x0001
#define HS_ABORT_TT  0x0002
#define HS_USER_ALM  0x0004

#ifdef HAVE_GPS
static unsigned long dispGPSnow = 0;
#endif
static unsigned long dispIdlenow = 0;
#ifdef HAVE_TEMP
static bool          tempOldNM = false;
#endif
#if (defined(HAVE_GPS) && defined(NOT_MY_RESPONSIBILITY)) || defined(HAVE_RE)
static bool          GPSabove88 = false;
#endif
#ifdef HAVE_REMOTE
static bool          bttfnRemStop     = false;  // Status of "Stop" switch/light
static int           bttfnRemoteSpeed = 0;      // What is displayed on remote
static int           bttfnRemCurSpd   = 0;      // What is displayed on speedo
static bool          bttfnRemOffSpd   = false;  // Remote wants speed also while fake-off (used for TT)
static int           bttfnOldRemCurSpd = 255;
static int           bttfnRemCurSpdOld = 255;
static unsigned long lastRemSpdUpd = 0, remSpdCatchUpDelay = 80;
static int           remoteWasMaster = 0;
static const char    *remoteOnSound = "/remoteon.mp3";
static const char    *remoteOffSound = "/remoteoff.mp3";
static uint32_t      oldptnmrem = 0;
#endif
#ifdef HAVE_RE
static int           fakeSpeed = 0;
static int           oldFSpd = 0;
static int           oldFakeSpeed = -1;
static bool          tempLock = false;
static unsigned long tempLockNow = 0;
static bool          spdreOldNM = false;
#endif
bool                 tempOffNM = true;
#ifdef HAVE_TEMP
static unsigned long tempReadNow = 0;
static unsigned long tempDispNow = 0;
static unsigned long tempUpdInt = TEMP_UPD_INT_L;
static bool          tempLastNan = true;
#endif

static unsigned long volChangedNow = 0;
static unsigned long disChangedNow = 0;

// The startup sequence
static unsigned long startupNow   = 0;

// Timetravel sequence: Timers, triggers, state
bool                 playTTsounds = true;
static bool          skipTTAnim = false;
static uint16_t      timeTravelP0stalled = 0;
static unsigned long timetravelP1Now = 0;
static unsigned long timetravelP1Delay = 0;
static int           timeTravelP1 = 0;
static bool          triggerP1 = false;
static bool          triggerP1NoLead = false;
static unsigned long triggerP1Now = 0;
static long          triggerP1LeadTime = 0;
static bool          ETTWithFixedLead = false;
static bool          useETTOWired = false;
static bool          useETTOWiredNoLead = false;
static const long    ettoLeadTime = ETTO_LEAD_TIME - ETTO_LAT;
static bool          triggerETTO = false;
static long          triggerETTOLeadTime = 0;
static unsigned long triggerETTONow = 0;
static long          ettoLeadPoint = 0;
static long          origEttoLeadPoint = 0;
static uint16_t      bttfnTTLeadTime = 0;
static long          ettoBase;
static bool          pubMQTTVL = false;
#ifdef HAVE_REMOTE
static bool          remoteInducedTT = false;
#endif
#ifdef ACAR_DISPLAY
#define P1JAN011885 "010118851200"
#define P1JAN011801 "010118011000"
#define P1ERR900    "  00900 9000"
#define P1ERR99     "  0099  0000"
#else
#define P1JAN011885 "JAN0118851200"
#define P1JAN011801 "JAN0118011000"
#define P1ERR900    "   00900 9000"
#define P1ERR99     "   0099  0000"
#endif
static const char * const p1errStrs[4] = {
    P1JAN011885, P1JAN011801, P1ERR900, P1ERR99
};

// Re-entry sequence
static unsigned long timetravelNow = 0;

// CPU power management
static unsigned long pwrFullNow = 0;

// State flags & co
static unsigned long lastAuthTime = 0;
uint64_t    lastAuthTime64     = 0;
static bool authTimeExpired    = false;
static bool postSecChange      = false;
static bool postHSecChange     = false;
static unsigned long pscsnow   = 0;
static bool postHSecChangeBusy = false;
static bool autoIntDone        = false;
int         autoIntAnimRunning = 0;
static bool autoReadjust       = false;
static int  infoLastMin        = -1;

static uint8_t* (*r)(uint8_t *, uint32_t, int);
int         specDisp = 0;

// Cumulative status flags
uint32_t    csf = CSF_BOOTSTRAP|CSF_NOMUSIC;

DateTime    gdtu, gdtl;
static struct {
    uint64_t td;
    dateStruct sDate;
    dateStruct tDate;
    bool tdup;
} ptCache;

static dateStruct destTimeBackup;
static dateStruct lastTimeBackup;

// For displaying times off the real time
uint64_t    timeDifference = 0;
bool        timeDiffUp = false;  // true = add difference, false = subtract difference

// TZ/DST status & data
static int  tzForYear[3]    = { 0, 0, 0 };               // Parsing done for this very year
static char *tzDSTpart[3]   = { NULL, NULL, NULL };
static int  tzDiffGMT[3]    = { 0, 0, 0 };               // Difference to UTC in nonDST time
static int  tzDiffGMTDST[3] = { 0, 0, 0 };               // Difference to UTC in DST time
static int  tzDiff[3]       = { 0, 0, 0 };               // difference between DST and non-DST in minutes
static int  DSTonMins[3]    = { -1, -1, -1 };            // DST-on date/time in minutes since 1/1 00:00 (in non-DST time)
static int  DSToffMins[3]   = { 600000, 600000, 600000}; // DST-off date/time in minutes since 1/1 00:00 (in DST time)
static bool couldDST[3]     = { false, false, false };   // Could use own DST management (and DST is defined in TZ)
static int8_t tzIsValid[3]  = { -1, -1, -1 };
static int8_t tzHasDST[3]   = { -1, -1, -1 };
#ifdef TC_DBG_BOOT
static const char *badTZ = "Failed to parse TZ\n";
#endif

// "Room condition" mode
static bool rcMode     = false;

// WC mode
uint32_t    wcf         = 0;
static int  wcLastMin   = -1;
int         destShowAlt = 0, depShowAlt = 0;
int         destShowAltPreset = 0, depShowAltPreset = 0; 
static bool wcMode      = false;

// Mini mode
static bool miniMode    = false;

// MQTT
uint32_t    mqttDisp = 0;
#ifdef HAVE_MQTT
static unsigned long mqttStartNow[3] = { 0 };
uint32_t    mqttOldDisp   = 0;
uint16_t    mqttIdx[3]    = { 0 };
int16_t     mqttMaxIdx[3] = { 0 };
char        *mqttMsg[3]   = { NULL };
bool        mqttST[3]     = { false };
#endif

// NTP/GPS
static bool          useNTP = false;
static WiFiUDP       ntpUDP;
static UDP*          myUDP = NULL;
static IPAddress     ntpIP;
static byte          NTPUDPBuf[NTP_PACKET_SIZE];
static unsigned long NTPUpdateNow = 0;
static unsigned long NTPTSAge = 0;
static unsigned long NTPTSRQAge = 0;
static uint32_t      NTPsecsSinceTCepoch = 0;
static uint32_t      NTPmsSinceSecond = 0;
static const uint8_t NTPUDPHD[4] = { 'T', 'C', 'D', '1' };
static uint32_t      NTPUDPID    = 0;
static bool          NTPPacketDue = false;
static bool          NTPWiFiUp = false;
static uint8_t       NTPfailCount = 0;
static bool          NTPLookupFail = false;

// The RTC object
#if defined(HAVE_DS3231) && defined(HAVE_PCF2129)
#define RTC_NUMTYPES 2
#else
#define RTC_NUMTYPES 1
#endif
static const uint8_t rtcAddr[RTC_NUMTYPES*2] = {
    #ifdef HAVE_PCF2129
    PCF2129_ADDR, RTCT_PCF2129, 
    #endif
    #ifdef HAVE_DS3231
    DS3231_ADDR,  RTCT_DS3231
    #endif
};
tcRTC rtc(RTC_NUMTYPES, rtcAddr);
#ifdef HAVE_PCF2129
static unsigned long OTPRDoneNow = 0;
static unsigned long OTPRStarted = 0;
static bool          RTCNeedsOTPR = false;
static bool          OTPRinProgress = false;
#endif

// The GPS object
#ifdef HAVE_GPS
#define GPS_NUMTYPES 1
static const uint8_t gpsAddr[GPS_NUMTYPES*2] = {
    GPS_MTK_ADDR, GPST_MTK333X
};
tcGPS myGPS(gpsAddr);
static uint64_t      lastLoopGPS   = 0;
static unsigned long GPSupdateFreq = 1000;
static bool          navMode     = false;
static int           gpsDispMode = 0;
#endif

// The TC display objects
tcdDisplay destinationTime(DISP_DEST, DEST_TIME_ADDR);
tcdDisplay presentTime(DISP_PRES, PRES_TIME_ADDR);
tcdDisplay departedTime(DISP_LAST, DEPT_TIME_ADDR);

// The speedo and temp.sensor objects
speedDisplay speedo(SPEEDO_ADDR);
#ifdef HAVE_RE
static const uint8_t rotEncAddr[3*2] = { 
    ADDA4991_ADDR, TC_RE_TYPE_ADA4991,
    DUPPAV2_ADDR,  TC_RE_TYPE_DUPPAV2,
    DFRGR360_ADDR, TC_RE_TYPE_DFRGR360
};
static const uint8_t rotEncVAddr[3*2] = { 
    ADDA4991V_ADDR, TC_RE_TYPE_ADA4991,
    DUPPAV2V_ADDR,  TC_RE_TYPE_DUPPAV2,
    DFRGR360V_ADDR, TC_RE_TYPE_DFRGR360
};
static TCRotEnc rotEnc(3, rotEncAddr);
static TCRotEnc rotEncV(3, rotEncVAddr);
static TCRotEnc *rotEncVol;
#endif
#ifdef HAVE_TEMP
static const uint8_t tempSensAddr[9*2] = { 
    MCP9808_ADDR, MCP9808,
    BMx280_ADDR,  BMx280,
    SHT40_ADDR,   SHT40,
    MS8607_ADDR,  MS8607,   // before Si7021
    SI7021_ADDR,  SI7021,
    TMP117_ADDR,  TMP117,
    AHT20_ADDR,   AHT20,
    HTU31_ADDR,   HTU31,
    HDC302X_ADDR, HDC302X
};
tempSensor tempSens(9, tempSensAddr);
#endif
#ifdef HAVE_LIGHT
static const uint8_t lightSensAddr[6*2] = { 
    LTR3xx_ADDR,  LST_LTR3xx,   // must be before TSL26x1
    TSL2591_ADDR, LST_TSL2591,  // must be after LTR3xx
    TSL2561_ADDR, LST_TSL2561,  // must be after LTR3xx
    BH1750_ADDR,  LST_BH1750,
    VEML6030_ADDR,LST_VEML7700,
    VEML7700_ADDR,LST_VEML7700  // must be last
};
lightSensor lightSens(6, lightSensAddr); 
#endif

bool stalePresent = false;
dateStruct stalePresentTime[2] = {
    {1985, 10, 26,  1, 22},         // original (set by 99xxx; always saved)
    {1985, 10, 26,  1, 22}          // changed during use (saved but set to original if !ttpersistent)
};
uint8_t stalePresentWeekDay[2] = { 0 };

// Time cycling
const uint8_t  autoTimeIntervals[6] = {0, 5, 10, 15, 30, 60};  // first one must be 0 (=off)
unsigned int   autoInterval = DEF_AUTOROTTIMES;
static bool    autoRotAnim = true;
static uint8_t autoIntSec  = 59;
static int     autoTime    = 0;
static unsigned long autoPaused = 0;
static unsigned long pauseDelay = 0;

#ifndef TWPRIVATE //  ----------------- OFFICIAL

const dateStruct destinationTimes[NUM_AUTOTIMES] = {
    {1985, 10, 26,  1, 21},   // Einstein 1:20 -> 1:21
    {1955, 11,  5,  6,  0},   // Marty -> 1955 ("6" visible; time never programmed, so I assume the TCD defaulted to 0600am)
    {1985, 10, 26,  1, 24},   // Marty -> 1985
    {2015, 10, 21, 16, 29},   // Marty, Doc, Jennifer -> 2015
    {1955, 11, 12,  8,  0},   // Old Biff -> 1955 (time unknown)
    {2015, 10, 21, 19, 25},   // Old Biff -> 2015 (time assumed from run of scene, backwards from 1928 as shown)
    {1985, 10, 26, 21,  0},   // Marty, Doc, Jennifer -> 1985
    {1955, 11, 12,  6,  0},   // Marty, Doc -> 1955
    {1885,  1,  1,  0,  0},   // Doc in thunderstorm -> 1885 (date/time assumed from letter)
    {1885,  9,  2,  8,  0},   // Marty -> 1885 (Date/time spoken by Doc)
    {1985, 10, 27, 11,  0}    // Marty -> 1985 (Time shown during loco-push)
};
const dateStruct departedTimes[NUM_AUTOTIMES] = {
    {1985, 10, 26,  1, 20},   // Einstein 1:20 -> 1:21
    {1985, 10, 26,  1, 29},   // Marty -> 1955 (time assumed; 7 minutes after 1:22, assuming movie runs in real-time)
    {1955, 11, 12, 22,  4},   // Marty -> 1985
    {1985, 10, 26, 10, 33},   // Marty, Doc, Jennifer -> 2015 (time calculated from wake-up at 10:28 until tt)
    {2015, 10, 21, 19, 15},   // Old Biff -> 1955  (time assumed from run of scene)
    {1955, 11, 12, 18, 38},   // Old Biff -> 2015
    {2015, 10, 21, 19, 28},   // Marty, Doc, Jennifer -> 1985
    {1985, 10, 27,  2, 42},   // Marty, Doc -> 1955
    {1955, 11, 12, 21, 33},   // Doc in thunderstorm -> 1885 (time assumed from following events)
    {1955, 11, 16, 11, 11},   // Marty -> 1885 (Date shown in PT in movie [11/5] at departure is wrong, must be after 11/12. Date 11/16 briefly shown in LTD when Delorean is pushed by locomotive. Time guessed)
    {1885,  9,  7,  8, 15}    // Marty -> 1985 (time calculated starting from 0755am shown on newly arrived clock tower clock, and from what could be a blurry "0810" during the loco-push)
};

#else //  --------------------------- TWPRIVATE

#include "z_twdates.h"

#endif  // ------------------------------------

// Night mode
bool           forceReEvalANM = false;
static bool    autoNightMode = false;
static bool    autoNMDone = false;
static uint8_t autoNightModeMode = 0;   // 0 = daily hours, 1-4 presets
static uint8_t autoNMOnHour  = 0;
static uint8_t autoNMOffHour = 0;
static int8_t  timedNightMode = -1;
static int8_t  sensorNightMode = -1;
int8_t         manualNightMode = -1;
unsigned long  manualNMNow = 0;
int32_t        luxLimit = 3;
static const uint32_t autoNMhomePreset[7] = {     // Mo-Th 5pm-11pm, Fr 1pm-1am, Sa 9am-1am, Su 9am-11pm
        0b011111111000000000000001,   //Sun
        0b111111111111111110000001,   //Mon
        0b111111111111111110000001,   //Tue
        0b111111111111111110000001,   //Wed
        0b111111111111111110000001,   //Thu
        0b111111111111100000000000,   //Fri
        0b011111111000000000000000    //Sat
};
static const uint32_t autoNMofficePreset[7] = {   // Mo-Fr 9am-5pm
        0b111111111111111111111111,   //Sun
        0b111111111000000001111111,   //Mon
        0b111111111000000001111111,   //Tue
        0b111111111000000001111111,   //Wed
        0b111111111000000001111111,   //Thu
        0b111111111000000001111111,   //Fri
        0b111111111111111111111111    //Sat
};
static const uint32_t autoNMoffice2Preset[7] = {  // Mo-Th 7am-5pm, Fr 7am-2pm
        0b111111111111111111111111,   //Sun
        0b111111100000000001111111,   //Mon
        0b111111100000000001111111,   //Tue
        0b111111100000000001111111,   //Wed
        0b111111100000000001111111,   //Thu
        0b111111100000001111111111,   //Fri
        0b111111111111111111111111    //Sat
};
static const uint32_t autoNMshopPreset[7] = {     // Mo-We 8am-8pm, Th-Fr 8am-9pm, Sa 8am-5pm
        0b111111111111111111111111,   //Sun
        0b111111110000000000001111,   //Mon
        0b111111110000000000001111,   //Tue
        0b111111110000000000001111,   //Wed
        0b111111110000000000000111,   //Thu
        0b111111110000000000000111,   //Fri
        0b111111110000000001111111    //Sat
};
static const uint32_t autoNMmcPreset[7] = {       // Su-Th 8pm-1am, Fr-Sa 8pm-4am;
        0b000011111111111111110000,   //Sun
        0b011111111111111111110000,   //Mon
        0b011111111111111111110000,   //Tue
        0b011111111111111111110000,   //Wed
        0b011111111111111111110000,   //Thu
        0b011111111111111111110000,   //Fri
        0b000011111111111111110000    //Sat
};
static uint32_t autoNMdailyPreset = 0;
const uint32_t *autoNMPresets[AUTONM_NUM_PRESETS] = {
    autoNMhomePreset, autoNMofficePreset, 
    autoNMoffice2Preset, autoNMshopPreset,
    autoNMmcPreset
};
#ifdef HAVE_LIGHT
static unsigned long lastLoopLight = 0;
#endif

// Reminder
uint8_t remMonth = 0;
uint8_t remDay   = 0;
uint8_t remHour  = 0;
uint8_t remMin   = 0;

// Count-down timer
unsigned long ctDown = 0;
unsigned long ctDownNow = 0;

// Fake "power" feature (TFC switch, MQTT, remote)
static TCButton fakePowerOnKey = TCButton(FAKE_POWER_BUTTON_PIN); // act low, pu

static bool useFakePowerSwitch = false;
bool        MQTTWaitForOn = false;
static bool isFPBKeyChange = false;
static bool isFPBKeyPressed = false;
#if defined(HAVE_REMOTE) || defined(HAVE_MQTT)
static bool shadowFPBKeyPressed = false;
#endif
#ifdef HAVE_MQTT
static bool shadowMQTTFPBKeyPressed = false;
#endif

// Door sound stuff
int           doorSnd = 0;
uint32_t      doorFlags = 0;
unsigned long doorSndDelay = 0;
unsigned long doorSndNow = 0;
int           door2Snd = 0;
uint32_t      door2Flags = 0;
unsigned long door2SndDelay = 0;
unsigned long door2SndNow = 0;

static unsigned long tsSndNow = 0;
static int16_t       tsSndSeg[3] = { 0 };

// Date & time stuff
static const uint8_t monthDays[] =
{
    31, 28, 31, 30, 31, 30, 31, 31, 30, 31, 30, 31
};
static const unsigned int mon_yday[2][13] =
{
    { 0, 31, 59, 90, 120, 151, 181, 212, 243, 273, 304, 334, 365 },
    { 0, 31, 60, 91, 121, 152, 182, 213, 244, 274, 305, 335, 366 }
};
static const unsigned int mon_ydayt24t60[2][13] =
{
    { 0, 31*24*60,  59*24*60,  90*24*60, 120*24*60, 151*24*60, 181*24*60, 
        212*24*60, 243*24*60, 273*24*60, 304*24*60, 334*24*60, 365*24*60 },
    { 0, 31*24*60,  60*24*60,  91*24*60, 121*24*60, 152*24*60, 182*24*60, 
        213*24*60, 244*24*60, 274*24*60, 305*24*60, 335*24*60, 366*24*60 }
};
static const uint64_t mins1kYears[] =
{
#ifndef JULIAN_CAL  
             0,  262975680,  525949920,  788924160, 1051898400,
    1314874080, 1577848320, 1840822560, 2103796800, 2366772480,
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
    4996520640/60, 5049115200/60, 5101711200/60, 5154305760/60, 5206900320/60,
    5259494880/60, 5312090880/60, 5364685440/60, 5417280000/60, 5469874560/60, 
    5522470560/60, 5575065120/60, 5627659680/60, 5680254240/60, 5732850240/60
#endif    
};

#ifdef JULIAN_CAL
static const uint64_t tdro = 5258967840;
#ifndef JSWITCH_1582
static const int jCentStart   = 1700;      // Start of century when switch took place
static const int jCentEnd     = 1799;      // Last year of century when switch took place
static const int jSwitchYear  = 1752;      // Year in which switch to Gregorian Cal took place
static const int jSwitchMon   = 9;         // Month in which switch to Gregorian Cal took place
static const int jSwitchDay   = 2;         // Last day of Julian Cal
static const int jSwitchSkipD = 11;        // Number of days skipped
static const int jSwitchSkipH = 11 * 24;   // Num hours skipped
#else
static const int jCentStart   = 1500;      // Start of century when switch took place
static const int jCentEnd     = 1599;      // Last year of century when switch took place
static const int jSwitchYear  = 1582;      // Year in which switch to Gregorian Cal took place
static const int jSwitchMon   = 10;        // Month in which switch to Gregorian Cal took place
static const int jSwitchDay   = 4;         // Last day of Julian Cal
static const int jSwitchSkipD = 10;        // Number of days skipped
static const int jSwitchSkipH = 10 * 24;   // Num hours skipped
#endif
static int mon_yday_jSwitch[13];     // Accumulated days per month in year of Switch
static int mon_ydayt24t60J[13];      // Accumulated mins per month in year of Switch
static int jSwitchYrHrs;
static uint32_t jSwitchHash = 0;
#else
static const uint64_t tdro = 5258964960;
#endif
#define a(f, j) (f << (*monthDays - j))
uint8_t* e(uint8_t *d, uint32_t m, int y) { return (*r)(d, m, y); }

// Acceleraton times
static const int16_t tt_p0_delays_rl[88] =
{
      0, 100, 100,  90,  80,  80,  80,  80,  80,  80,  // 0 - 9  10mph 0.8s    0.8=800ms
     80,  80,  80,  80,  80,  80,  80,  80,  80,  80,  // 10-19  20mph 1.6s    0.8
     90, 100, 110, 110, 110, 110, 110, 110, 120, 120,  // 20-29  30mph 2.7s    1.1
    120, 130, 130, 130, 130, 130, 130, 130, 130, 140,  // 30-39  40mph 4.0s    1.3
    150, 160, 190, 190, 190, 190, 190, 190, 210, 230,  // 40-49  50mph 5.9s    1.9
    230, 230, 240, 240, 240, 240, 240, 240, 250, 250,  // 50-59  60mph 8.3s    2.4
    250, 250, 260, 260, 270, 270, 270, 280, 290, 300,  // 60-69  70mph 11.0s   2.7
    320, 330, 350, 370, 370, 380, 380, 390, 400, 410,  // 70-79  80mph 14.7s   3.7
    410, 410, 410, 410, 410, 410, 410, 410             // 80-87  90mph 18.8s   4.1
};
static const int16_t tt_p0_delays_movie[88] =
{
      0,  90,  90,  90,  90,  90,  90,  95,  95, 100,  // m0 - 9  10mph  0- 9: 0.83s  (m=measured, i=interpolated)
    105, 110, 115, 120, 125, 130, 135, 140, 145, 150,  // i10-19  20mph 10-19: 1.27s
    155, 160, 165, 170, 175, 180, 185, 190, 195, 200,  // i20-29  30mph 20-29: 1.77s
    200, 200, 202, 203, 204, 205, 206, 207, 208, 209,  // m30-39  40mph 30-39: 2s
    210, 211, 212, 213, 214, 215, 216, 217, 218, 219,  // i40-49  50mph 40-49: 2.1s
    220, 221, 222, 223, 224, 225, 226, 227, 228, 229,  // m50-59  60mph 50-59: 2.24s
    230, 233, 236, 240, 243, 246, 250, 253, 256, 260,  // i60-69  70mph 60-69: 2.47s
    263, 266, 270, 273, 276, 280, 283, 286, 290, 293,  // m70-79  80mph 70-79: 2.78s
    296, 300, 300, 303, 303, 306, 310, 310             // i80-88  90mph 80-88: 2.4s   total 17.6 secs
};
static const int16_t *tt_p0_delays = tt_p0_delays_movie;
static long tt_p0_totDelays[88];

// BTTF-Network
int bttfnHaveClients = 0; // This is a bool by nature (0, !0)
#define BTTFN_NOT_PREPARE  1
#define BTTFN_NOT_TT       2
#define BTTFN_NOT_REENTRY  3
#define BTTFN_NOT_ABORT_TT 4
#define BTTFN_NOT_ALARM    5
#define BTTFN_NOT_REFILL   6
#define BTTFN_NOT_FLUX_CMD 7
#define BTTFN_NOT_SID_CMD  8
#define BTTFN_NOT_PCG_CMD  9
#define BTTFN_NOT_WAKEUP   10
#define BTTFN_NOT_AUX_CMD  11
#define BTTFN_NOT_VSR_CMD  12
#define BTTFN_NOT_REM_CMD  13
#define BTTFN_NOT_REM_SPD  14  // Obsolete
#define BTTFN_NOT_SPD      15
#define BTTFN_NOT_INFO     16
#define BTTFN_NOT_DATA     128 // bit only, not value
#define BTTFN_REMCMD_PING        1   // Implicit "Register"/keep-alive
#define BTTFN_REMCMD_BYE         2   // Forced unregister
#define BTTFN_REMCMD_COMBINED    3   // All switches & speed combined
#define BTTFN_REMCMD_KP_PING     4
#define BTTFN_REMCMD_KP_KEY      5
#define BTTFN_REMCMD_KP_BYE      6
#define BTTFN_OPEN_CMDS        100
#define BTTFN_REMCMD_DOOR      100
#define BTTFN_REMCMD_KEEPALIVE 101
#define BTTFN_REMCMD_PS        102
#define BTTFN_REMCMD_DGREFILL  103
#define BTTFN_SSRC_NONE         0
#define BTTFN_SSRC_GPS          1
#define BTTFN_SSRC_ROTENC       2
#define BTTFN_SSRC_REM          3
#define BTTFN_SSRC_P0           4
#define BTTFN_SSRC_P1           5
#define BTTFN_SSRC_P2           6
#define BTTFN_TCDI1_NOREM     0x0001
#define BTTFN_TCDI1_NOREMKP   0x0002
#define BTTFN_TCDI1_EXT       0x0004
#define BTTFN_TCDI1_OFF       0x0008
#define BTTFN_TCDI1_NM        0x0010
#define BTTFN_TCDI2_BUSY      0x0001
#define BTTFN_TCDI2_TIMEINFO  0x8000
#define BTTFN_VERSION              1
#define BTTF_PACKET_SIZE          48
#define BTTF_DEFAULT_LOCAL_PORT 1338
#define BTTFN_MAX_CLIENTS          6
struct _bttfnClient {
    unsigned long ALIVE;
    #ifdef HAVE_REMOTE
    uint32_t      RemID;
    #endif
    union {
        uint8_t   IP[4];
        uint32_t  IP32;
    };
    uint8_t       Flags;
    uint8_t       Type;
    char          ID[14];
};
static const uint8_t BTTFUDPHD[BTTF_PACKET_SIZE] = { 'B', 'T', 'T', 'F', BTTFN_VERSION | 0x40, 0};
static WiFiUDP       bttfUDP;
static UDP*          tcdUDP;
static WiFiUDP       bttfmcUDP;
static UDP*          tcdmcUDP;
static IPAddress     bttfnMcIP(224, 0, 0, 224);
static byte          BTTFUDPBuf[BTTF_PACKET_SIZE];
static byte          BTTFDataBuf[BTTF_PACKET_SIZE];
static _bttfnClient  bttfnClient[BTTFN_MAX_CLIENTS];
static uint8_t       bttfnDateBuf[8];
static uint32_t      bttfnSeqCnt = 1;
static uint32_t      bttfnDataSeqCnt = 1;
static unsigned long bttfnlastExpire = 0;
static uint32_t      hostNameHash = 0;
static uint32_t      bttfnSessionID = 0;
static byte          BTTFMCBuf[BTTF_PACKET_SIZE];
static uint8_t       bttfnNotAllSupportMC = 0;
static uint8_t       bttfnAtLeastOneMC = 0;
static uint8_t       bttfnAtLeastOneND = 0;
static int           oldBTTFNSpd = -2;
static uint16_t      oldBTTFNSSrc = 0xffff;
static unsigned long bttfnLastSpeedNot = 0;
static unsigned long bttfnLastDataNot = 0;
static unsigned long bttfnLastInfo = 0;
static uint8_t       bttfnData17 = 0, bttfnData18, bttfnData19, bttfnCap32;
static unsigned long bttfnScheduleInfo;
#ifdef HAVE_REMOTE
static uint32_t      registeredRemID  = 0;
static uint32_t      registeredRemKPID = 0;
static uint32_t      bttfnLastSeq_co  = 0;
static uint32_t      bttfnLastSeq_ky  = 0;
static uint32_t      bttfnLastSeq_do  = 0;
static unsigned long bttfnScheduleRemOnSnd = 0;
static unsigned long bttfnScheduleRemOffSnd = 0;
static unsigned long bttfnScheduleWakeup = 0;
static bool          bttfnScheduleRefill = false;
static uint32_t      bttfnBsgf = 0;
#endif // HAVE_REMOTE

#ifdef ESP32
/*  "warning: taking address of packed member of 'struct <anonymous>' may 
 *  result in an unaligned pointer value"
 *  "GCC will issue this warning when accessing an unaligned member of 
 *  a packed struct due to the incurred penalty of unaligned memory 
 *  access. However, all ESP chips (on both Xtensa and RISC-V 
 *  architectures) allow for unaligned memory access and incur no extra 
 *  penalty."
 *  https://docs.espressif.com/projects/esp-idf/en/v5.1/esp32s3/migration-guides/release-5.x/5.0/gcc.html
 */
#define GET32(a,b)    *((uint32_t *)((a) + (b)))
#define SET32(a,b,c)  *((uint32_t *)((a) + (b))) = c
#define GET16(a,b)    *((uint16_t *)((a) + (b)))
#define SET16(a,b,c)  *((uint16_t *)((a) + (b))) = c
#else
#define GET32(a,b)          \
    (((a)[b])            |  \
    (((a)[(b)+1]) << 8)  |  \
    (((a)[(b)+2]) << 16) |  \
    (((a)[(b)+3]) << 24))   
#define SET32(a,b,c)                        \
    (a)[b]       = ((uint32_t)(c)) & 0xff;  \
    ((a)[(b)+1]) = ((uint32_t)(c)) >> 8;    \
    ((a)[(b)+2]) = ((uint32_t)(c)) >> 16;   \
    ((a)[(b)+3]) = ((uint32_t)(c)) >> 24; 
#define GET16(a,b)          \
    (((a)[b])            |  \
    (((a)[(b)+1]) << 8))   
#define SET16(a,b,c)                        \
    (a)[b]       = ((uint16_t)(c)) & 0xff;  \
    ((a)[(b)+1]) = ((uint16_t)(c)) >> 8;
#endif

#ifdef HAVE_MQTT
static void displayMQTTmessage(uint32_t dmask, int idx, tcdDisplay *targetdisplay);
#endif

static void myCustomDelay_Sens(unsigned long mydel);
static void myCustomDelay_GPS(unsigned long mydel);
static void mySetupDelay(unsigned int mydel, bool heavy = true);
static void waitAudioDoneSetup();
static void mySetupNWCheck();

static void startDisplays();
static void triggerSaveDisplayMode();

static unsigned long play_alarm_sound();

static bool getNTPOrGPSTime(bool weHaveAuthTime, DateTime& dt, bool updateRTC = true, bool wifiAllowed = true);
static bool getNTPTime(bool weHaveAuthTime, DateTime& dt, bool updateRTC = true, bool wifiAllowed = true);
#ifdef HAVE_GPS
static bool getGPStime(DateTime& dt, uint16_t currYear, bool updateRTC = true);
static bool setGPStime();
bool        gpsHaveFix();
static bool gpsHaveTime();
#endif
#if defined(HAVE_GPS) || defined(HAVE_RE)
static bool displayGPSorRESpeed(bool force = false);
#endif
#ifdef HAVE_REMOTE
static bool updAndDispRemoteSpeed();
#endif
#ifdef HAVE_TEMP
static void updateTemperature(bool force = false);
static bool dispTemperature(bool force = false);
#endif
static void dispIdleZero(bool force = false);
#ifdef HAVE_RE                
static void re_init(bool zero = true);
static void re_lockTemp();
#endif

static void triggerLongTT(bool noLead = false);
#if (defined(HAVE_GPS) && defined(NOT_MY_RESPONSIBILITY)) || defined(HAVE_RE)
static void checkForSpeedTT(bool doP2, bool isRemote);
#endif

static void copyPresentToDeparted(bool isReturn);

static void ettoPulseStart();
static void ettoPulseStartNoLead();
static void sendTTNetWorkMsg(uint16_t bttfnPayload, uint16_t bttfnPayload2);
static void sendNetWorkMsg(const char *pl, uint8_t bttfnMsg, uint16_t bttfnPayload = 0, uint16_t bttfnPayload2 = 0);
static void sendAlarmNetWorkMsg();

// Time calculations
static uint64_t  dateToMins(int year, int month, int day, int hour, int minute);
static void      minsToDate(uint64_t total, int& year, int& month, int& day, int& hour, int& minute);
#ifdef JULIAN_CAL
static void      calcJulianData();
#endif
static void      convTime(int diff, int& y, int& m, int& d, int& h, int& mm);

/// Native NTP
static bool NTPHaveCurrentTime();
static bool NTPGetUTC(int& year, int& month, int& day, int& hour, int& minute, int& second);

// Basic Telematics Transmission Framework
static void bttfn_notify(uint8_t targetType, uint8_t event, uint16_t *payload = NULL, uint8_t *payload2 = NULL);
static void bttfn_notify_speed();
static void bttfn_send_autoUpdates();
static void bttfn_setup();
static void bttfn_setup_sensors();

static void allShowText(const char *d, const char *p, const char *l, int o)
{
    if(d) { destinationTime.showTextDirect(d); if(o & 1) destinationTime.on(); }
    if(p) { presentTime.showTextDirect(p);     if(o & 2) presentTime.on(); }
    if(l) { departedTime.showTextDirect(l);    if(o & 4) departedTime.on(); }
}

static void allRestoreBri()
{
    destinationTime.setBrightness(255);
    presentTime.setBrightness(255);
    departedTime.setBrightness(255);
}

static void allBriDirect(int d, int p, int l)
{
    destinationTime.setBrightnessDirect(d);
    presentTime.setBrightnessDirect(p);
    departedTime.setBrightnessDirect(l);
}

/*
 * main_boot()
 *
 */
void main_boot()
{       
    // Reset TT-out as early as possible
    pinMode(EXTERNAL_TIMETRAVEL_OUT_PIN, OUTPUT);
    digitalWrite(EXTERNAL_TIMETRAVEL_OUT_PIN, LOW);
   
    // Start the displays early to clear them
    startDisplays();
    
    // Switch LEDs on
    // give user some feedback that the unit is powered
    pinMode(LEDS_PIN, OUTPUT);
    digitalWrite(LEDS_PIN, HIGH);
    // Do not call leds_on(), is not unconditional

    // Initialize default exhibition mode dates in secSettings
    initDefaultStaleTime((void *)&stalePresentTime[0]);
}

/*
 * main_setup()
 *
 */
void main_setup()
{
    uint64_t oldTime = 0, newTime;
    #ifdef HAVE_GPS
    int quickGPSupdates = -1;
    int speedoUpdateRate = 0;
    bool haveAuthTimeGPS = false;
    #endif
    bool rtcbad = false;
    bool tzbad = false;
    bool haveGPS = false;
    bool isVirgin = false;
    bool playIntro = false;
    #ifdef TC_DBG_BOOT
    const char *funcName = "time_setup: ";
    #endif

    Serial.println("Time Circuits Display version " TC_VERSION " " TC_VERSION_EXTRA);

    // Power management: Set CPU speed
    // to maximum and start timer
    pwrNeedFullNow(true);

    // Pin for monitoring seconds from RTC
    pinMode(SECONDS_IN_PIN, INPUT_PULLDOWN);

    // Init fake power switch
    useFakePowerSwitch = evalBool(settings.fakePwrOn);
    fakePowerOnKey.begin(LOW, INPUT_PULLUP, 50, 10, 50);
    if(useFakePowerSwitch) {
        fakePowerOnKey.attachLongPressStart(fpbKeyPressed);
        fakePowerOnKey.attachLongPressStop(fpbKeyLongPressStop);
    }

    playIntro = evalBool(settings.playIntro);

    // RTC setup
    if(!rtc.begin()) {

        static const char *rtcNotFound = "RTC NOT FOUND";
        uint8_t r = HIGH;
        
        destinationTime.showTextDirect(rtcNotFound);
        Serial.printf("%s\n", rtcNotFound);

        // Blink white LED forever
        while(1) {
            digitalWrite(WHITE_LED_PIN, r);
            for(int i = 0; i < 10; i++) {
                delay(100);
                wifi_loop();
            }
            r ^= HIGH;
        }
    }

    #ifdef HAVE_PCF2129
    RTCNeedsOTPR = rtc.NeedOTPRefresh();
    #endif

    if(rtc.lostPower()) {

        // Lost power and battery didn't keep time, so set current time to 
        // default time 1/1/2026, 0:0
        rtc.adjust(0, 0, 0, dayOfWeek(1, 1, 2026), 1, 1, 26);
       
        #ifdef TC_DBG_BOOT
        Serial.printf("%sRTC lost power, setting default time\n", funcName);
        #endif

        rtcbad = true;
    }

    #ifdef HAVE_PCF2129
    if(RTCNeedsOTPR) {
        rtc.OTPRefresh(true);
        delay(100);
        rtc.OTPRefresh(false);
        delay(100);
        OTPRDoneNow = millis();
    }
    #endif

    // Turn on the RTC's 1Hz clock output
    rtc.clockOutEnable();

    // Calculate data for Julian Calendar
    #ifdef JULIAN_CAL
    calcJulianData();
    #endif

    // Swap red and yellow displays if so configured
    #ifdef ACAR_DISPLAY
    if(evalBool(settings.swapDL)) {
        destinationTime.setAddress(DEPT_TIME_ADDR);
        departedTime.setAddress(DEST_TIME_ADDR);
    }
    #endif

    // Start (reset) the displays
    startDisplays();

    {
        // Initialize clock mode: 12 hour vs 24 hour
        bool tempmode = evalBool(settings.mode24);
        presentTime.set1224(tempmode);
        destinationTime.set1224(tempmode);
        departedTime.set1224(tempmode);
        if(tempmode) bttfnData17 = 0x80;

        tempmode = evalBool(settings.revAmPm);
        presentTime.setAMPMOrder(tempmode);
        destinationTime.setAMPMOrder(tempmode);
        departedTime.setAMPMOrder(tempmode);
    }

    #ifndef ACAR_DISPLAY
    p3anim = evalBool(settings.p3anim);
    #endif
    skipTTAnim = evalBool(settings.skipTTAnim);

    // Configure behavior in night mode
    destinationTime.setNMOff(evalBool(settings.dtNmOff));
    presentTime.setNMOff(evalBool(settings.ptNmOff));
    departedTime.setNMOff(evalBool(settings.ltNmOff));

    // Determine if user wanted Time Travels to be persistent
    // Requires SD card and "Save secondary settings to SD" to
    // be checked if PERSISTENT_SD_ONLY is #defined
    #ifdef PERSISTENT_SD_ONLY
    if(configOnSD) {
    #endif  
        timetravelPersistent = evalBool(settings.timesPers);
    #ifdef PERSISTENT_SD_ONLY
    } else {
        timetravelPersistent = false;
    }
    #endif
    
    // Set initial brightness for present time displqy
    presentTime.setBrightness(settings.presTimeBright, true);
    
    // Load present time clock state (lastYear, yearOffs)
    {
        int16_t tyo;
        lastYear = presentTime.loadClockStateData(tyo);
        presentTime.setYearOffset(tyo);
    }

    // Load timeDifference
    presentTime.load();

    if(rtcbad) {
        // Default date (see above) requires yoffs 0
        presentTime.setYearOffset(0);
    }

    // Read current time in order to validate/correct timeDifference
    if(timetravelPersistent && timeDifference && !rtcbad) {
        // Load UTC time from RTC
        myrtcnow(gdtu);
        oldTime = dateToMins(gdtu.year(), gdtu.month(), gdtu.day(), gdtu.hour(), gdtu.minute());
        if(timeDiffUp) {
            oldTime += timeDifference;
        } else {
            oldTime -= timeDifference;
        }
        if(oldTime >= 
        #ifndef JULIAN_CAL
                      mins1kYears[(10000 / 500)]
        #else
                      mins1kYears[(10000 / 100)]
        #endif
                                                ) {
            timeDifference = 0;
        }
    } else {
        timeDifference = 0;
    }

    if(check_file_SD(preTTSound))   haveSnds |= HS_PRE_TT;
    if(check_file_SD(abortTTSound)) haveSnds |= HS_ABORT_TT;
    if(check_file_SD(alarmSound))   haveSnds |= HS_USER_ALM;
    
    // Set up alarm base: RTC or current "present time"
    evalBoolSetClear(settings.alarmRTC, alf, ALF_RTC);
    if(evalBoolSetClear(settings.alarmType, alf, ALF_ADV)) {
        evalBoolSetClear(settings.doSnooze, alf, ALF_SNOOZE);
        evalBoolSetClear(settings.autoSnooze, alf, ALF_ASNOOZE);
        evalBoolSetClear(settings.almLoopUserSnd, alf, ALF_USRLOOP);
        alarmPlayDur = ALARM_PLAY_DUR;
    } else {
        alarmPlayDur = 5*1000;
    }
    if(haveSnds & HS_USER_ALM) alf |= ALF_HS;
    snoozeTime = atoi(settings.snoozeTime);
    if(snoozeTime < 1) snoozeTime = 1;
    else if(snoozeTime > 15) snoozeTime = 15;
    snoozeTime *= (60*1000);

    // See if speedo (display) is to be used
    {
        int temp = atoi(settings.speedoType);
        int scorr = 0, tcorr = 0;
        bool bttfnSpeedoFallback = false;
        
        if(temp >= SP_NUM_TYPES) {
            // if 99(="None") or bad: Fall back to BTTFN-speedo
            temp = SP_BTTFN;
            bttfnSpeedoFallback = true;
        }

        #ifdef SERVOSPEEDO
        loadServoCorr(scorr, tcorr);
        #endif

        if(!speedo.begin(temp, sspeedopin, stachopin, scorr, tcorr)) {
            #ifdef TC_DBG_BOOT
            Serial.printf("%sSpeedo type %d not found\n", funcName, temp);
            #endif
            // if not found: Fall back to BTTFN-speedo
            if(!speedo.begin(SP_BTTFN)) {
                #ifdef TC_DBG_BOOT
                Serial.printf("%sBTTFN-speedo init failed\n", funcName);
                #endif
            } else {
                sgf |= SGF_USpeedo;
                bttfnSpeedoFallback = true;
            }
        } else {
            sgf |= SGF_USpeedo;
        }

        if((sgf & SGF_USpeedo) && (speedo.haveSpeedoDisplay() || !bttfnSpeedoFallback)) {
            sgf |= SGF_USpeedoDisp;
            speedo.setupBrightness(atoi(settings.speedoBright), atoi(settings.tempBright));
        }

        // SGF_USpeedo is set if tt sequences should potentially be done with P0 and P2
        //              unset if tt sequences will never be done with P0 or P2
        // SGF_USpeedoDisp is set if a speed-displaying device is present
        //                  unset if none, or if BTTFN only as fallback
    }
    
    // Set up GPS receiver
    #ifdef HAVE_GPS
    evalBoolSetClear(settings.useGPSTime, sgf, SGF_UGPSTime);
    
    if(sgf & SGF_USpeedoDisp) {
        // 'dispGPSSpeed' means "display GPS speed on speedo"
        // False if no GPS receiver found, or no speedo found, or option "Display GPS speed" unchecked
        evalBoolSetClear(settings.dispGPSSpeed, sgf, SGF_DispGPSSpd);
    }

    // Set useGPS to true, user might want to use nav mode
    sgf |= SGF_UGPS;

    if(sgf & SGF_UGPS) {

        evalBoolSetClear(settings.provGPS2BTTFN, sgf, SGF_GPS2BTTFN);
        quickGPSupdates = (sgf & SGF_DispGPSSpd) ? 1 : ((sgf & SGF_GPS2BTTFN) ? 0 : -1);
        speedoUpdateRate = atoi(settings.spdUpdRate) & 3;
    
        // Check for GPS receiver
        // Do so regardless of usage in order to eliminate
        // VEML7700 light sensor with identical i2c address
        if(myGPS.begin(GPS_NUMTYPES, quickGPSupdates, speedoUpdateRate, myCustomDelay_GPS)) {
    
            haveGPS = true;
              
            // Clear so we don't add to stampAge unnecessarily in
            // boot strap
            GPSupdateFreq = 0;
            
            // We know now we have a possible source for auth time
            if(sgf & SGF_UGPSTime) {
                couldHaveAuthTime |= 1;
            }
            
            // Fetch data already in Receiver's buffer [120ms]
            for(int i = 0; i < 10; i++) myGPS.loop(true);
            lastLoopGPS = millis64();
            
            #ifdef TC_DBG_BOOT
            Serial.printf("%sGPS Receiver found\n", funcName);
            #endif
    
        } else {
          
            sgf &= ~(SGF_UGPS|SGF_UGPSTime|SGF_DispGPSSpd|SGF_GPS2BTTFN);
            
            #ifdef TC_DBG_BOOT
            Serial.printf("%sGPS Receiver not found\n", funcName);
            #endif
            
        }
    }
    #endif
    
    // Try to obtain initial authoritative time
    // (First NTP request was sent in wifi_ntp_setup())
    if(useNTP && (WiFi.status() == WL_CONNECTED)) {
        int timeout = 50;
        do {
            ntp_loop();
            delay(100);
            timeout--;
        } while (!NTPHaveCurrentTime() && timeout);
    }

    // Parse TZ to check validity and to get difference to UTC
    // (Year does not matter at this point)
    if(!parseTZ(0, 2022)) {
        tzbad = true;
        #ifdef TC_DBG_BOOT
        Serial.printf("%s%s", funcName, badTZ);
        #endif
    }
    
    // Set RTC with NTP time
    if(getNTPTime(true, gdtu, true, true)) {

        // So we have authoritative time now
        haveAuthTime = true;
        lastAuthTime = millis();
        lastAuthTime64 = millis64();
        
        #ifdef TC_DBG_BOOT
        Serial.printf("%sRTC set through NTP\n", funcName);        
        #endif
        
    } else {
      
        // GPS might have a fix, so try fetching time from GPS
        #ifdef HAVE_GPS
        if(sgf & SGF_UGPS) {

            // Pull old data from buffer
            for(int i = 0; i < 10; i++) myGPS.loop(true);

            for(int i = 0; i < 10; i++) {
                for(int j = 0; j < 4; j++) myGPS.loop(true);
                #ifdef TC_DBG_BOOT
                if(i == 0) Serial.printf("%sFirst attempt to read time from GPS\n", funcName);
                #endif
                if(sgf & SGF_UGPSTime) {
                    if(getGPStime(gdtu, (lastYear >= TCEPOCH_GEN) ? lastYear : TCEPOCH_GEN, true)) {
                        // So we have authoritative time now
                        haveAuthTime = true;
                        lastAuthTime = millis();
                        lastAuthTime64 = millis64();
                        haveAuthTimeGPS = true;
                        #ifdef TC_DBG_BOOT
                        Serial.printf("%sRTC set through GPS\n", funcName);
                        #endif
                        break;
                    }
                }
                delay(100);
            }
            // If we haven't managed to get time here, try
            // a sync in shorter intervals in time_loop.
            if((sgf & SGF_UGPSTime) && !haveAuthTimeGPS) resyncInt = 2;
            lastLoopGPS = millis64();
        }
        #endif
    }

    // Start the Config Portal (if deferred)
    if(schf & SCHF_DEFERREDCP) {
        if(WiFi.status() == WL_CONNECTED) {
            if(playIntro || (useFakePowerSwitch && 
                            (digitalRead(FAKE_POWER_BUTTON_PIN) == HIGH))) {
                wifiStartCP();
                schf &= ~SCHF_DEFERREDCP;
            }
        } else {
            schf &= ~SCHF_DEFERREDCP;
        }
    }

    // Preset this for BTTFN status requests during boot
    #ifdef HAVE_MQTT
    if(csf & CSF_MQTTPM) {
        if(!(shadowMQTTFPBKeyPressed = !MQTTWaitForOn)) csf |= CSF_OFF;
    } else
    #endif
           if(useFakePowerSwitch) {
        csf |= CSF_OFF;
    }

    // Start bttf network
    bttfn_setup();

    // Load UTC time from RTC (requires valid yearOffset)
    myrtcnow(gdtu);

    // rtcYear: Current UTC-year (as read from the RTC, minus Yoffs)
    uint16_t rtcYear = gdtu.year();

    // lastYear: The UTC-year when the RTC was adjusted for the last time (or 0).
    // If the RTC was just updated (haveAuthTime), everything is in place.
    // Otherwise use lastYear loaded from NVM, compare it to RTC year, and 
    // make required re-calculations (based on RTC year) if they don't match.
    if(haveAuthTime) {
        lastYear = rtcYear;
    }

    // If we are switched on after a year switch, re-do
    // RTC year-translation (UTC)
    if(lastYear != rtcYear) {

        // Get RTC-fit year & offs for real year
        int16_t yOffs = 0;
        uint16_t newYear = rtcYear;
        correctYr4RTC(newYear, yOffs);

        // If year-translation changed, update RTC and save
        if((newYear != gdtu.hwRTCYear) || (yOffs != presentTime.getYearOffset())) {

            // Update RTC (UTC)
            rtc.adjust(gdtu.second(), 
                       gdtu.minute(), 
                       gdtu.hour(), 
                       dayOfWeek(gdtu.day(), gdtu.month(), rtcYear),
                       gdtu.day(), 
                       gdtu.month(), 
                       newYear-2000
            );

            presentTime.setYearOffset(yOffs);

            gdtu.hwRTCYear = newYear;
            gdtu.setYear(rtcYear);

        }

        lastYear = rtcYear;
    }

    // Write lastYear and yearOffset (UTC) to NVM (if modified)
    presentTime.saveClockStateData(lastYear);

    // Correct timeDifference
    if(timetravelPersistent && timeDifference) {
        // oldTime = time travel target time based on RTC-read UTC time
        newTime = dateToMins(gdtu.year(), gdtu.month(), gdtu.day(), gdtu.hour(), gdtu.minute());
        if(oldTime > newTime) {
            timeDifference = oldTime - newTime;
            timeDiffUp = true;
        } else {
            timeDifference = newTime - oldTime;
            timeDiffUp = false;
        }
        presentTime.save();
    }

    // Convert UTC to local (also parses timezone)
    UTCtoLocal(gdtu, gdtl, 0);

    // Parse alternate time zones for WC for testing their validity
    if(settings.timeZoneDest[0] != 0) {
        if(parseTZ(1, gdtl.year())) {
            wcf |= WCF_HaveTZ1;
        }
    }
    if(settings.timeZoneDep[0] != 0) {
        if(parseTZ(2, gdtl.year())) {
            wcf |= WCF_HaveTZ2;
        }
    }
    if(wcf & (WCF_HaveTZ1|WCF_HaveTZ2)) {
        wcf |= WCF_HaveWCM;
        if((wcf & WCF_HaveTZ1) && settings.timeZoneNDest[0] != 0) {
            if(destinationTime.setAltText(settings.timeZoneNDest)) {
                evalBoolSetClear(settings.WCNamePerm, wcf, WCF_showName1);
            }
            destShowAltPreset = (wcf & WCF_showName1) ? -1 : 3*2;
        }
        if((wcf & WCF_HaveTZ2) && settings.timeZoneNDep[0] != 0) {
            if(departedTime.setAltText(settings.timeZoneNDep)) {
                evalBoolSetClear(settings.WCNamePerm, wcf, WCF_showName2);
            }
            depShowAltPreset = (wcf & WCF_showName2) ? -1 : 3*2;
        }
    }

    // Init Exhibition mode and load time to presentTime display
    loadStaleTime((void *)&stalePresentTime[0], stalePresent);
    if(!timetravelPersistent) {
        memcpy((void *)&stalePresentTime[1], (void *)&stalePresentTime[0], sizeof(dateStruct));
    }
    if(stalePresent)
        updateStalePresent(1);
    else
        updatePresentTime();   // uses gdt{u,l}

    // Set GPS receiver's RTC
    #ifdef HAVE_GPS
    if(sgf & SGF_UGPS) {
        if(!haveAuthTimeGPS && (haveAuthTime || !rtcbad)) {
            setGPStime();
        }
        
        // Set ms between GPS polls
        // Need more updates if speed is to be displayed
        // RMC is 72-85 chars, so three fit in the 255 byte buffer.
        // VTG is 40+ chars, so six fit into the buffer.
        // We use VTG+RMC+ZDA when displaying speedo on speedo at 200/250ms rates.
        // Otherwise we go with RMC+ZDA.
        // (Must sync readFreq and updFreq for smooth speedo display)

        if(quickGPSupdates < 0) {
            // For time only, the fix update rate is set to 5000ms;
            // We poll every 500ms, so the entire buffer is read every 
            // 2 seconds (64 bytes per poll).
            GPSupdateFreq = 500;
        } else if(!quickGPSupdates) {
            // For GPS speed for BTTFN clients (but no speed display
            // on speedo), the fix update rate is set to 1000ms/500ms,
            // so the buffer fills in 3000/1500ms. We poll every 
            // 250/250ms, hence the entire buffer is read in
            // 1000/1000ms (64 bytes per poll).
            // The max delay to get current speed is therefore 500ms.
            GPSupdateFreq = 250; //(!speedoUpdateRate) ? 250 : 250;
        } else {
            // For when GPS speed is to be displayed on speedo:
            // We read 128 byte blocks from the receiver in this case.
            switch(speedoUpdateRate) {
            case 0:
                // At 1000ms update rate, the buffer fills in 3000ms (with ZDA: 2900)
                // At 500ms readfreq (128 bytes blocks), the entire buffer is read in 1000ms
                // At 250ms readfreq (128 bytes blocks), the entire buffer is read in 500ms
                // We want as little delay as possible with displaying speed, so we go 250.
                //GPSupdateFreq = 500;
                //break;
            case 1:
                // At 500ms update rate, the buffer fills in 1500ms (with ZDA: 1400)
                // At 500ms readfreq (128 bytes blocks), the entire buffer is read in 1000ms
                // At 250ms readfreq (128 bytes blocks), the entire buffer is read in 500ms
                // We want as little delay as possible with displaying speed, so we go 250.
                //GPSupdateFreq = 500;
                //break;
            case 2:
                // With VTG: At 250ms update rate, the buffer fills in 1500ms (with RMC+ZDA: 1400ms on avg)
                // At 250ms readfreq (128 bytes blocks), the entire buffer is read in 500ms
                GPSupdateFreq = 250;
                break;
            case 3:
                // With VTG: At 200ms update rate, the buffer fills in 1200ms (with RMC+ZDA: 1100ms on avg)
                // At 200ms readfreq (128 bytes blocks), the entire buffer is read in 400ms
                GPSupdateFreq = 200;
                break;
            }
        }
    }
    #endif

    // Set initial brightness for dest & last time dep displays
    destinationTime.setBrightness(settings.destTimeBright, true);
    departedTime.setBrightness(settings.lastTimeBright, true);

    // Load destination time (and set to default if invalid)
    if(!destinationTime.load()) {
        destinationTime.setFromStruct(&destinationTimes[0]);
        destinationTime.copyToUserTimes();
        destinationTime.save();
        isVirgin = true;
    }

    // Load departed time (and set to default if invalid)
    if(!departedTime.load()) {
        departedTime.setFromStruct(&departedTimes[0]);
        departedTime.copyToUserTimes();
        departedTime.save();
    }

    // If time cycling enabled, put up the first one
    if(autoInterval) {
        destinationTime.setFromStruct(&destinationTimes[0]);
        departedTime.setFromStruct(&departedTimes[0]);
    }

    backupLastTime();
    backupDestTime();

    // Load alarm from alarmconfig file
    // Don't care if data invalid, alarm is off in that case
    loadAlarm();

    // Load yearly/monthly reminder settings
    loadReminder();

    // Handle early BTTFN requests (first call)
    // At this point everything that could be used/changed
    // by BTTFN commands (especially the Remote) must be
    // set up. Remote is kept from becoming speedmaster
    // through bootStrap flag. It can already become
    // powermaster, however. Speedo is not set-up yet.
    mySetupNWCheck();

    // Auto-NightMode
    autoNightModeMode = atoi(settings.autoNMPreset);
    if(autoNightModeMode > AUTONM_NUM_PRESETS) autoNightModeMode = 10;
    autoNightMode = (autoNightModeMode != 10);
    autoNMOnHour = atoi(settings.autoNMOn);
    if(autoNMOnHour > 23) autoNMOnHour = 0;
    autoNMOffHour = atoi(settings.autoNMOff);
    if(autoNMOffHour > 23) autoNMOffHour = 0;
    if(autoNightMode && (autoNightModeMode == 0)) {
        if((autoNightMode = (autoNMOnHour != autoNMOffHour))) {
            if(autoNMOnHour < autoNMOffHour) {
                for(int i = autoNMOnHour; i < autoNMOffHour; i++)
                    autoNMdailyPreset |= (1 << (23-i));
            } else {
                autoNMdailyPreset = 0b111111111111111111111111;
                for(int i = autoNMOffHour; i < autoNMOnHour; i++)
                    autoNMdailyPreset &= ~(1 << (23-i));
            }
        }
    }
    if(autoNightMode) forceReEvalANM = true;

    // Set up option to play/mute time travel sounds
    playTTsounds = evalBool(settings.playTTsnds);

    // Set power-up setting for beep
    muteBeep = true;
    if(beepMode >= 3) {
        beepMode = 3;
        beepTimeout = BEEPM3_SECS*1000;
    } else if(beepMode == 2)
        beepTimeout = BEEPM2_SECS*1000;

    // Set up speedo display
    if((!(sgf & SGF_USpeedo)) || !evalBool(settings.speedoAF)) {
        //tt_p0_delays = tt_p0_delays_movie;  // already initialized
        ttP0TimeFactor = 1.0f;
    } else {
        tt_p0_delays = tt_p0_delays_rl;
        ttP0TimeFactor = (float)strtof(settings.speedoFact, NULL);
    }
    
    if(sgf & SGF_USpeedo) {
      
        if(sgf & SGF_USpeedoDisp) {

            bool rAligned = false;
            
            // Negate this flag, option reads "Switch off", not "Keep on"
            if(!(evalBool(settings.speedoAO))) sgf |= SGF_SpAlwsOn;
    
            // P1/P2 vs P3 speedo style
            if(evalBool(settings.speedoP3)) {
                rAligned = evalBool(settings.speedoP3R);
                speedo.dispL0Spd = true;
                speedo.thirdDig = false;
                speedo.setDot(false);
            } else {
                speedo.dispL0Spd = false;
                speedo.thirdDig &= evalBool(settings.speedo3rdD);
                speedo.setDot(true);
            }
            speedo.finishSetup(rAligned);
        }

        // No TT sounds to play -> no user-provided sound.
        if(!playTTsounds) haveSnds &= ~HS_PRE_TT;

        // Speed factor for acceleration curve
        if(ttP0TimeFactor < 0.5f) ttP0TimeFactor = 0.5f;
        if(ttP0TimeFactor > 5.0f) ttP0TimeFactor = 5.0f;

        // Calculate start point of P1 sequence
        for(int i = 1; i < 88; i++) {
            pointOfP1 += (unsigned long)(((float)(tt_p0_delays[i])) / ttP0TimeFactor);
        }
        ettoBase = pointOfP1;
        ettoLeadPoint = origEttoLeadPoint = ettoBase - ettoLeadTime;   // Can be negative!
        pointOfP1NoLead = pointOfP1;  // for lead-less P1
        pointOfP1 -= TT_P1_POINT88;   // for normal P1

        {
            // Calculate total elapsed time for each mph value
            // (in order to time P0/P1 relative to current actual speed)
            long totDelay = 0;
            for(int i = 0; i < 88; i++) {
                totDelay += (long)(((float)(tt_p0_delays[i])) / ttP0TimeFactor);
                tt_p0_totDelays[i] = totDelay;
            }
        }

        if(sgf & SGF_USpeedoDisp) {
            speedo.off();
    
            #ifdef HAVE_GPS
            if(sgf & SGF_DispGPSSpd) {
                // display (actual) speed, regardless of fake power
                displayGPSorRESpeed(true);
                speedo.on(); 
            } else {
            #endif
                if(sgf & SGF_SpAlwsOn) {
                    if(!(csf & CSF_OFF)) {
                        speedo.setSpeed(0);
                        speedo.show();
                        speedo.on();
                        speedoStatus = SPST_ZERO;
                    }
                }
            #ifdef HAVE_GPS
            }
            #endif
        }
        
    }

    // Set up rotary encoders
    // There are primary and secondary i2c addresses for RotEncs.
    // Use primary RotEnc for speed, if either no speedo is present, or,
    // if a speedo is present, GPS speed is not to be displayed on it; or
    // if no GPS receiver is present.
    #ifdef HAVE_RE
    if(!(sgf & SGF_DispGPSSpd)) {
        if(rotEnc.begin(true)) {
            sgf |= SGF_URotEnc;
            if(sgf & SGF_USpeedoDisp) sgf |= SGF_DispRotEnc;
            re_init();
            re_lockTemp();
            fakeSpeed = oldFSpd = rotEnc.updateFakeSpeed(true);
            if(!(csf & CSF_OFF)) {
                if(sgf & SGF_DispRotEnc) {
                    displayGPSorRESpeed(true);
                    speedo.on();
                }
            }
            // Temperature-display is now blocked by tempLock
        }
    }
    // Check for secondary RotEnc for volume on secondary i2c addresses
    if(rotEncV.begin(false)) {
        sgf |= SGF_URotEncVol;
        rotEncVol = &rotEncV;
        re_vol_reset();
    }
    #endif

    // Handle early BTTFN requests
    mySetupNWCheck();

    // Set up temperature sensor
    #ifdef HAVE_TEMP
    sgf |= SGF_UTemp;   // Use if detected
    if((sgf & SGF_USpeedoDisp) && (!(sgf & SGF_DispGPSSpd)) && speedo.supportsTemperature()) {
        evalBoolSetClear(settings.dispTemp, sgf, SGF_DispTemp);
    }
    evalBoolSetClear(settings.tempUnit, sgf, SGF_TempCelsius);
    if(tempSens.begin(myCustomDelay_Sens, !!(sgf & SGF_TempCelsius))) {
        tempSens.setOffset((float)strtof(settings.tempOffs, NULL));
        wcf |= WCF_HaveRCM;
        if(tempSens.haveHum()) sgf |= SGF_HaveHum;
        tempOffNM = evalBool(settings.tempOffNM);
        if(sgf & SGF_DispTemp) {
            if(!(csf & CSF_OFF)) {
                updateTemperature(true);
                dispTemperature(true);
            }
        }
    } else {
        sgf &= ~(SGF_UTemp|SGF_DispTemp);
    }
    #else
    sgf &= ~(SGF_UTemp|SGF_DispTemp);
    #endif

    #ifdef HAVE_LIGHT
    evalBoolSetClear(settings.useLight, sgf, SGF_ULightSens);
    luxLimit = atoi(settings.luxLimit);
    if(sgf & SGF_ULightSens) {
        if(!lightSens.begin(haveGPS, myCustomDelay_Sens)) {
            sgf &= ~SGF_ULightSens;
        }
    }
    #else
    sgf &= ~SGF_ULightSens;
    #endif

    // Now that we know what sensors we have, tell BTTFN
    bttfn_setup_sensors();

    // Animate time cycling?
    if(!(autoRotAnim = evalBool(settings.autoRotAnim)))
        autoIntSec = 0;

    // Evaluate TT-OUT settings and setup flags accordingly
    if(!ttoutpin) {
        if(evalBool(settings.useETTO)) {
            useETTOWiredNoLead = evalBool(settings.noETTOLead);
            ETTWithFixedLead = useETTOWired = !useETTOWiredNoLead;
        }
        if(evalBool(settings.ETTOalm)) {
            ETTOalarm = true;
            ETTOAlmDur = atoi(settings.ETTOAD) * 1000;
        }
        if(evalBool(settings.ETTOcmd)) {
            ETTOcommands = true;
            if(evalBool(settings.ETTOpus)) {
                setTTOUTpin(HIGH);
            }
        }
    } else {
        // All pre-initialized to false
        //ETTWithFixedLead = useETTOWiredNoLead = false;
        //ETTOalarm = false;
        //ETTOcommands = false;
    }

    // MQTT: If 'extended TIMETRAVEL command' is to be used,
    // we need to lead. Otherwise, we do.
    #ifdef HAVE_MQTT
    if(pubMQTT) {
        if(MQTTvarLead) pubMQTTVL = true;           // No lead needed
        else            ETTWithFixedLead = true;    // Lead needed
    }
    #endif
    // When ETTWithFixedLead is true, the 5 sec lead is needed (for wired and/or MQTT)
    // When ETTWithFixedLead is false, no lead is ever needed.
    
    // Show "REPLACE BATTERY" message if RTC battery is low or depleted
    // Note: This also shows up the first time you power-up the clock
    // AFTER a battery change.
    if((rtcbad && !isVirgin) || rtc.battLow()) {
        allShowText("REPLACE", "BATTERY", NULL, 1+2);
        mySetupDelay(5000);
        allOff();
    } else {
        mySetupNWCheck();
    }

    if(tzbad) {
        allShowText("BAD", "TIME ZONE", NULL, 1+2);
        mySetupDelay(5000);
        allOff();
    }

    // Invoke audio file installer if SD content qualifies
    if(check_allow_CPA()) {
        doCopyAudioFiles();
        // We never return here
    }

    if(!haveAudioFiles) {
        allShowText("PLEASE", "INSTALL", "SOUND PACK", 1+2+4);
        mySetupDelay(5000);
        allOff();
    } else if(showUpdAvail && updateAvailable()) {
        allShowText("UPDATE", "AVAILABLE", NULL, 1+2);
        mySetupDelay(1000);
        allOff();
    }

    if(playIntro) {
        static const char *t1 = "             TIME";
        static const char *t2 = "             CIRCUITS";
        static const char *t3 = "ON";

        // suppress WiFi scan (don't use Px, those will prevent GPS speedo updates)
        csf |= CSF_NS;      

        play_file("/intro.mp3", PA_LINEOUT|PA_CHECKNM|PA_INTRMUS|PA_ALLOWSD|PA_DYNVOL);

        mySetupDelay(1200);
        allBriDirect(15, 15, 0);
        departedTime.off();
        allShowText(t1, t2, t3, 1+2);
        for(int i = 0; i < 14; i++) {
           mySetupDelay(50, false);
           allShowText(&t1[i], &t2[i], NULL, 0);
        }
        mySetupDelay(500);
        departedTime.on();
        for(int i = 0; i <= 15; i++) {
            departedTime.setBrightnessDirect(i);
            mySetupDelay(100);
        }
        mySetupDelay(1500);
        for(int i = 15; i >= 0; i--) {
            allBriDirect(i, i, i);
            mySetupDelay(20, false);
        }
        allOff();
        allRestoreBri();

        waitAudioDoneSetup();
        stopAudio();

        csf &= ~CSF_NS;

    } else {
        mySetupNWCheck();
    }

    // Evaluate bootMode
    uint8_t d = loadBootMode();
    if(!(wcf & WCF_HaveRCM)) d &= ~0x01;
    if(!(wcf & WCF_HaveWCM)) d &= ~0x02;
    #ifdef HAVE_GPS
    if(!haveNavMode())       d &= ~0x04;
    #else
    d &= ~0x04;
    #endif
    if(d & 0x01) enableRcMode(true);
    if(d & 0x02) enableWcMode(true);
    #ifdef HAVE_GPS
    if(d & 0x04) enableNavMode(true);
    #endif
    if(d & 0x08) enableMiniMode(true);

    {
        bool bootNow = true;
        
        if(csf & (CSF_OFF|CSF_RPM)) {
            fakePowerOnKey.scan();
            mySetupDelay(70);     // Bridge debounce/longpress time
            fakePowerOnKey.scan();
            if(!isFPBKeyPressed) {
                leds_off();
                csf |= CSF_OFF;
                bootNow = false;
                digitalWrite(WHITE_LED_PIN, HIGH);
                mySetupDelay(250);
                digitalWrite(WHITE_LED_PIN, LOW);
                #ifdef TC_DBG_BOOT
                Serial.printf("%swaiting for fake power on\n", funcName);
                #endif
            }            
            isFPBKeyChange = false;
        }  

        if(bootNow) {

            csf &= ~CSF_OFF;
            csf |= CSF_ST;
            schf |= SCHF_STARTUP;
            leds_on();
            if(beepMode >= 2)      startBeepTimer();
            else if(beepMode == 1) muteBeep = false;
    
        }
    }

    deferredCPNow = millis();

    // Read firmware version of GPS receiver module
    #ifdef HAVE_GPS
    if(sgf & SGF_UGPS) {
        myGPS.requestVersion();
    }
    #endif

    csf &= ~CSF_BOOTSTRAP;
}

/*
 * main_loop()
 *
 */
void main_loop()
{
    unsigned long millisNow = millis();
    #ifdef TC_DBG_TIME
    int dbgLastMin;
    const char *funcName = "time_loop: ";
    #endif

    if(useFakePowerSwitch || (csf & (CSF_MQTTPM|CSF_RPM|CSF_RESTOREFP))) {

        csf &= ~CSF_RESTOREFP;
        
        fakePowerOnKey.scan();

        if(isFPBKeyChange) {
            deferredCPNow = millisNow;
            if(isFPBKeyPressed) {
                if(csf & CSF_OFF) {
                    schf |= SCHF_STARTUP;
                    csf |= CSF_ST;
                    csf &= ~CSF_OFF;
                    if(beepMode >= 2)      startBeepTimer();
                    else if(beepMode == 1) muteBeep = false;
                    allRestoreBri();  // restore brightnesses in case we got switched off during time travel
                    #ifdef HAVE_RE
                    if(sgf & SGF_URotEnc) {
                        re_init();
                        re_lockTemp();
                        GPSabove88 = false;
                    }
                    #endif

                    if((sgf & SGF_USpeedoDisp) && (!(sgf & SGF_DispGPSSpd)) && (!(csf & CSF_RSM))) {
                        if(sgf & (SGF_SpAlwsOn|SGF_DispRotEnc)) {
                            speedo.setSpeed(0);
                            speedo.show();
                            #ifdef HAVE_RE
                            speedoStatus = (sgf & SGF_DispRotEnc) ? SPST_RE : SPST_ZERO;
                            #else
                            speedoStatus = SPST_ZERO;
                            #endif
                        }
                    }
                    
                    #ifdef HAVE_TEMP
                    updateTemperature(true);
                    dispTemperature(true);
                    #endif
                    wcf |= WCF_Trigger;
                    destShowAlt = depShowAlt = 0; // Reset WC's TZ-Name-Animation
                    // Time-cycling is unpaused through startup_trigger
                }
            } else {
                if(!(csf & CSF_OFF)) {
                    schf &= ~(SCHF_STARTUP|SCHF_STARTUP2);
                    triggerP1 = false;
                    triggerETTO = false;
                    ettoPulseEnd();
                    send_abort_msg();
                    #ifdef HAVE_REMOTE
                    if((csf & CSF_P0) && (csf & CSF_RSM)) {
                        // Need to fake if P0 was running
                        // (See comment when cancelling P0)
                        bttfnRemoteSpeed = timeTravelP0Speed;
                    }
                    #endif
                    timeTravelP1 = 0;
                    timeTravelP0stalled = 0;
                    #ifdef HAVE_REMOTE
                    remoteInducedTT = false;
                    #endif
                    csf &= ~(CSF_ST|CSF_P0|CSF_P1|CSF_RE|CSF_P2);
                    csf |= CSF_OFF;
                    cancelEnterAnim(false);
                    cancelETTAnim();
                    resetKeypadState();
                    discardKeypadInput();
                    mp_stop(true);
                    if((!(csf & (CSF_AL|CSF_AE))) && !isSignalPlaying()) {
                        stopAudio();
                        flushDelayedSave();
                        play_file("/shutdown.mp3", PA_INTSPKR|PA_CHECKNM|PA_INTRMUS|PA_ALLOWSD);
                    }
                    mydelay(130);
                    allOff();
                    leds_off();
                    if((sgf & SGF_USpeedoDisp) && (!(sgf & SGF_DispGPSSpd)) && (!(csf & CSF_RSM))) speedo.off();
                }
            }
            isFPBKeyChange = false;
            csf |= CSF_INFOUPD;
        }
    }

    millisNow = millis();

    // Seldomly scheduled events: Startup, door sound, scheduled INFO
    if(schf) {

        // Startup, p1: Initiate startup delay, play startup sound,
        // pause time-cycling for a few seconds
        if(schf & SCHF_STARTUP) {
            schf &= ~SCHF_STARTUP;
            schf |= SCHF_STARTUP2;
            // autoPause now, don't let autoInt interrupt us
            startupNow = autoPaused = millisNonZero();
            pauseDelay = STARTUP_DELAY + 2000;
            if(!(csf & (CSF_AL|CSF_AE))) {
                play_file("/startup.mp3", PA_INTSPKR|PA_CHECKNM|PA_INTRMUS|PA_ALLOWSD, 0.8f);
            }
        }

        // Startup, p2: Turn display on after startup delay, switch on speedo
        if((schf & SCHF_STARTUP2) && (millisNow - startupNow >= STARTUP_DELAY)) {
            schf &= ~SCHF_STARTUP2;
            animate(true);
            csf &= ~CSF_ST;
            if((sgf & SGF_USpeedoDisp) && (!(sgf & SGF_DispGPSSpd)) && (!(csf & CSF_RSM))) {
                #ifdef HAVE_RE
                if(sgf & SGF_DispRotEnc) {
                    speedo.on();
                } else {
                #endif
                    #ifdef HAVE_TEMP
                    updateTemperature(true);
                    if(sgf & SGF_DispTemp) {
                        dispTemperature(true);
                    } else {
                    #endif
                        if(sgf & SGF_SpAlwsOn) {
                            dispIdleZero(true);
                        } else {
                            speedo.off(); // Yes, off.
                        }
                    #ifdef HAVE_TEMP
                    }
                    #endif
                #ifdef HAVE_RE
                }
                #endif    
            }
            // Let audio_loop take care of updating MP status
        }

        // Timer for deferred CP start
        if((schf & SCHF_DEFERREDCP) && (millisNow - deferredCPNow > 4000)) {
            schf &= ~SCHF_DEFERREDCP;
            wifiStartCP();
        }
        
        // Timers for door sound
        if(schf & SCHF_DOOR1) {
            unsigned long timePassed = millisNow - doorSndNow;
            // delay door sound by max 500ms, otherwise effect is lost and we skip it
            if(timePassed > doorSndDelay) {
                schf &= ~SCHF_DOOR1;
                if(timePassed <= doorSndDelay + 500) {
                    play_door_snd(1, doorSnd, doorFlags);
                }
            }
        } else if(schf & SCHF_DOOR2) {
            unsigned long timePassed = millisNow - door2SndNow;
            if(timePassed > door2SndDelay) {
                schf &= ~SCHF_DOOR2;
                if(timePassed <= door2SndDelay + 500) {
                    play_door_snd(2, door2Snd, door2Flags);
                }
            }
        }

        // Scheduled INFO for newly registered BTTFN clients
        if((schf & SCHF_SENDINFO) && (millisNow - bttfnScheduleInfo > 5000)) {
            schf &= ~SCHF_SENDINFO;
            csf |= CSF_INFOUPD;
        }

        if(schf & SCHF_TS) {
            schf &= ~SCHF_TS;
            if(millisNow - tsSndNow < 500) play_ts_snd(tsSndSeg);
        }
    }

    // Timer for starting P1 if to be delayed
    if(triggerP1 && (millis() - triggerP1Now >= triggerP1LeadTime)) {
        triggerLongTT(triggerP1NoLead);
        triggerP1 = false;
    }

    // Timer for start of ETTO signal
    if(triggerETTO && (millis() - triggerETTONow >= triggerETTOLeadTime)) {
        sendTTNetWorkMsg(bttfnTTLeadTime, TT_P1_EXT);
        ettoPulseStart();
        triggerETTO = false;
        #ifdef TC_DBG_TT
        Serial.println("ETTO triggered");
        #endif
    }

    millisNow = millis();

    // Time travel animation, phase 0: Speed counts up
    if(csf & CSF_P0) {
      
        if(millisNow - timetravelP0Now >= timetravelP0Delay) {

            long timetravelP0DelayT = 0;
    
            timeTravelP0stalled = 0;
    
            timeTravelP0Speed++;
    
            if(timeTravelP0Speed < 88) {
                unsigned long ttP0NowT = millisNow;
                long ttP0LDOver = 0, ttP0LastDelay = (long)(ttP0NowT - ttP0Now);
                ttP0Now = ttP0NowT;
                ttP0LDOver = ttP0LastDelay - timetravelP0Delay;
                timetravelP0DelayT = (long)(((float)(tt_p0_delays[timeTravelP0Speed])) / ttP0TimeFactor) - ttP0LDOver;
                while(timetravelP0DelayT <= 0 && timeTravelP0Speed < 88) {
                    timeTravelP0Speed++;
                    timetravelP0DelayT += (long)(((float)(tt_p0_delays[timeTravelP0Speed])) / ttP0TimeFactor);
                }
            }
    
            if(timeTravelP0Speed < 88) {
    
                timetravelP0Delay = timetravelP0DelayT;
                timetravelP0Now = millisNow;
    
            } else {
    
                csf &= ~CSF_P0;
    
            }
    
            speedo.setSpeed(timeTravelP0Speed);
            speedo.show();
    
            // Overwrite fakeSpeed/bttfnRemCurSpd for BTTFN clients who keep polling
            // until P1-ETTO_LEAD
            #ifdef HAVE_RE
            if(sgf & SGF_URotEnc) {
                // Need to keep -1, otherwise we can't detect if enc was off
                // ahead of the tt, see also P2
                fakeSpeed = rotEnc.IsOff() ? -1 : timeTravelP0Speed;
            }
            #endif
            #ifdef HAVE_REMOTE
            // Update for BTTFN clients
            bttfnRemCurSpd = timeTravelP0Speed;
            #endif
    
            // P0 is cancelled if brake is hit on the Remote
            // but not if P1 has already started
            #ifdef HAVE_REMOTE
            if((csf & CSF_RSM) && (csf & CSF_P0) && bttfnRemStop) {
                if(timeTravelP1 <= 0) {
                    if(!triggerETTO) {
                        // Send abort (only if TT was already signalled)
                        send_abort_msg();
                        ettoPulseEnd();
                    }
                    csf &= ~CSF_P0;
                    // Fake for following updAndDispRemoteSpeed()-call.
                    // (Remote does not send updates while in P0 [which
                    // would be pointless as it would only mirror our P0
                    // speed], so bttfnRemoteSpeed is outdated now)
                    // (This is also needed when fake-switched off)
                    bttfnRemoteSpeed = timeTravelP0Speed;
                    triggerP1 = false;
                    triggerETTO = false;
                    timeTravelP0stalled = 0;
                    if(playTTsounds) {
                        if(haveSnds & HS_ABORT_TT) {
                            play_file(abortTTSound, PA_LINEOUT|PA_CHECKNM|PA_INTRMUS|PA_ALLOWSD|PA_DYNVOL);
                        } else {
                            // if(playTTsounds) mp is stopped on TT, so no need to mp_stop()
                            stopAudio();
                        }
                    }
                    // SGF_URotEnc = 0 while Remote=SpeedMaster, no reset required
                }
            }
            #endif
        }

    // Time travel animation, phase 2: Speed counts down
    } else if(csf & CSF_P2) {

        if(millisNow - timetravelP0Now >= timetravelP0Delay) {

            bool countToGPSSpeed = false;
            int  targetSpeed = 0;
            #ifdef HAVE_REMOTE
            if(csf & CSF_RSM) {
                countToGPSSpeed = true;
                targetSpeed = bttfnRemStop ? 0 : bttfnRemoteSpeed;
            } else
            #endif
            {
                #ifdef HAVE_GPS
                if(sgf & SGF_DispGPSSpd) {
                    int tgpsSpd = myGPS.getSpeed();
                    if(tgpsSpd >= 0) {
                        countToGPSSpeed = true;
                        targetSpeed = tgpsSpd;
                    }
                }
                #endif
            }
            if((timeTravelP0Speed <= targetSpeed) || (targetSpeed >= 88)) {
                csf &= ~CSF_P2;
                #ifdef NOT_MY_RESPONSIBILITY
                if(countToGPSSpeed && targetSpeed >= 88) {
                    // Avoid an immediately repeated time travel
                    // if speed increased in the meantime
                    // (For button-triggered TT while speed < 88)
                    GPSabove88 = true;
                }
                #endif
                #ifdef HAVE_RE
                if(sgf & SGF_URotEnc) {
                    // We MUST reset the encoder; user might have moved
                    // it while we blocked updates during P0-P2.
                    // If fakeSpeed is -1 at this point, it was disabled
                    // when starting P0 (which is why we don't overwrite
                    // fakeSpeed when enc is off, see above at P0)
                    if(fakeSpeed < 0) {
                        // Reset enc to "disabled" position
                        re_init(false);
                    } else {
                        // Reset enc to "zero" position
                        re_init();
                        re_lockTemp();
                    }
                    GPSabove88 = false;
                }
                #endif
                if((!(sgf & (SGF_DispGPSSpd|SGF_DispRotEnc))) && (!(csf & CSF_RSM))) {
                    if(sgf & SGF_SpAlwsOn) {
                        dispIdleZero(true);
                    } else {
                        speedo.off();
                    }
                }
                #if defined(HAVE_GPS) || defined(HAVE_RE)
                displayGPSorRESpeed(true);
                #endif
                #ifdef HAVE_TEMP
                updateTemperature(true);
                dispTemperature(true);
                #endif
                #ifdef HAVE_REMOTE
                updAndDispRemoteSpeed();
                #endif    
            } else {
                timetravelP0Now = millis();
                timeTravelP0Speed--;
                speedo.setSpeed(timeTravelP0Speed);
                speedo.show();
                #ifdef HAVE_REMOTE
                // Overwrite for BTTFN clients, and in case Remote kicked in during TT
                // in which case the saved displayed speed would be outdated at the end of P2
                // and updAndDispRemoteSpeed() would start count down from the outdated
                // speed again.
                bttfnRemCurSpd = timeTravelP0Speed; 
                #endif
                #ifdef HAVE_RE
                if(sgf & SGF_URotEnc) {
                    // Need to keep -1, otherwise we can't detect if enc was off
                    // ahead of the tt, see end of P2
                    fakeSpeed = rotEnc.IsOff() ? -1 : timeTravelP0Speed;
                }
                #endif
                #if defined(HAVE_GPS) || defined(HAVE_REMOTE)
                if(countToGPSSpeed) {
                    if(targetSpeed == timeTravelP0Speed) {
                        timetravelP0Delay = 0;
                    } else {
                        uint8_t tt = ((timeTravelP0Speed-targetSpeed)*100) / (88 - targetSpeed);
                        timetravelP0Delay = ((100 - tt) * 150) / 100;
                        if(timetravelP0Delay < 40) timetravelP0Delay = 40;
                    }
                } else {
                #endif
                    timetravelP0Delay = ((timeTravelP0Speed == 0) && (!(sgf & SGF_DispRotEnc))) ? 4000 : 40;
                #if defined(HAVE_GPS) || defined(HAVE_REMOTE)
                }
                #endif
            }
        }
    }

    millisNow = millis();
    
    // Time travel animation, phase 1: Display disruption
    if((timeTravelP1 > 0) && (millisNow - timetravelP1Now >= timetravelP1Delay)) {
        timeTravelP1++;
        timetravelP1Now = millisNow;
        switch(timeTravelP1) {
        case 2:
            #ifdef TC_DBG_TT
            Serial.printf("TT initiated %d\n", millisNow);
            #endif
            ettoPulseStartNoLead();
            if(!skipTTAnim) allOff();
            timetravelP1Delay = TT_P1_DELAY_P2;
            break;
        case 3:
            timetravelP1Delay = TT_P1_DELAY_P3;
            break;
        case 4:
            timetravelP1Delay = TT_P1_DELAY_P4;
            break;
        case 5:
            timetravelP1Delay = TT_P1_DELAY_P5;
            break;
        default:
            timeTravelP1 = 0;
            csf &= ~CSF_P1;
            allRestoreBri();  // restore
            timeTravel(false, true);
        }
    }

    // Turn display back on after time traveling
    if((csf & CSF_RE) && (millis() - timetravelNow >= REENTRY_DURATION)) {
        csf &= ~CSF_RE;
        animate();
    }

    // Post half-sec change slot: Save data
    postHSecChangeBusy = false;
    if(postHSecChange) {
        // Save data in time-slices to avoid long stalls
        if(!(csf & (CSF_ST|CSF_P0|CSF_P1|CSF_RE|CSF_P2))) {
            unsigned long pscnow = millis();
            if(checkAudioDone() || mpActive) {    // Dont't interrupt sound (incl beep), but ignore musicplayer
                if(!presentTime.saveClockStateData(lastYear)) {
                    if(!presentTime.saveFlush()) {
                        if(!departedTime.saveFlush()) {
                            if(destinationTime.saveFlush()) {
                                postHSecChangeBusy = true;
                            }
                        } else {
                            postHSecChangeBusy = true;
                        }
                    } else {
                        postHSecChangeBusy = true;
                        #ifdef TC_DBG_TIME
                        Serial.printf("Write presentTime to FS %d\n", millis());
                        #endif
                    }
                } else {
                    postHSecChangeBusy = true;
                    #ifdef TC_DBG_TIME
                    Serial.printf("Write lastYear to FS %d\n", millis());
                    #endif
                }
                if(!postHSecChangeBusy) {
                    if(volChangedNow && (pscnow - volChangedNow > 10*1000)) {
                        volChangedNow = 0;
                        saveCurVolume();
                        postHSecChangeBusy = true;
                    } else if(disChangedNow && (pscnow - disChangedNow > 10*1000)) {
                        disChangedNow = 0;
                        saveBootMode();
                        postHSecChangeBusy = true;
                    }
                }
                if(postHSecChangeBusy) {
                    unsigned long psctime = millis() - pscnow;
                    unsigned long pscstime = millis() - pscsnow;
                    if(psctime < 50 && pscstime < 200) {
                        postHSecChangeBusy = false;
                    } else if(psctime > 100) {
                        audio_loop();
                    }
                }
                // Slot is now taken
                postHSecChange = false;
            } else if(pscnow - pscsnow > 400) {
                // Slot lost if more than 400ms of our 500ms have passed
                postHSecChange = false;
            }
        } else {
            // Slot blocked by sequence, wait for next
            postHSecChange = false;
        }
        
    } else if(postSecChange) {

        postSecChange = false;

        // Post sec-change slot:

        #ifdef HAVE_LIGHT
        bool switchNMoff = false;
        #endif
      
        // Timer, Alarm, Reminder, Sound-on-the-Hour

        // Hierarchy:
        // 1. Timer: Can interrupt sequence, alarm and reminder
        // 2. Alarm: Is played after sequence
        // 3. Reminder: Is played after sequence and after alarm
        // 4. SotH: Cannot interrupt anything, is skipped if not played on time

        // Determine due signals to queue

        {
            int compHour, compMin;
            
            // 1. Timer. This should be done more often (not just post-sec), but
            //           we are no chronograph, but rather an egg-timer.
            if(ctDown && (millis() - ctDownNow > ctDown)) {
                ctDown = 0;
                sigFlags |= SF_TQ;
            }

            if(alf & ALF_RTC) {
                // reading bttfnDateBuf is safe, we are running post sec-change
                compHour = bttfnDateBuf[4]; compMin = bttfnDateBuf[5];
            } else {
                compHour = presentTime.getHour(); compMin = presentTime.getMinute();
            }
    
            // 2a. Alarm
            if(alarmOnOff) {
                if((alarmHour == compHour) && (alarmMinute == compMin)) {
                    if(!(sigFlags & SF_AD)) {
                        int weekDayMask = 1 << ((alf & ALF_RTC) ? bttfnDateBuf[7] : dayOfWeek(presentTime.getDay(), presentTime.getMonth(), presentTime.getYear()));
                        if(alarmWeekday & 0x80) {
                            if(alarmWeekday & weekDayMask) {
                                sigFlags |= SF_AQ;
                            }
                        } else if(alarmWDmasks[alarmWeekday] & weekDayMask) {
                            sigFlags |= SF_AQ;
                        }
                        sigFlags |= SF_AD;
                    } 
                } else {
                    sigFlags &= ~SF_AD;
                }
            }
    
            // 2b. Snooze timer
            if(snoozeNow && (millisNow - snoozeNow >= snoozeTime)) {
                snoozeNow = 0;
                sigFlags |= SF_SQ;
            }
    
            // 3. Reminder
            if(remDay) {
                if((remHour == gdtl.hour()) && (remMin == gdtl.minute())) {
                    if(!(sigFlags & SF_RD)) {
                        if((!remMonth || remMonth == gdtl.month()) && (remDay == gdtl.day())) {
                            sigFlags |= SF_RQ;
                        }
                        sigFlags |= SF_RD;
                    }
                } else {
                    sigFlags &= ~SF_RD;
                }
            }
    
            // 4. Sound on the Hour
            // Follows setting for alarm as regards the option
            // of "Alarm base is real present time" vs whatever
            // is currently displayed in presentTime.
            if(compMin == 0) {
                if(!(sigFlags & SF_HD)) {
                    if( (!(csf & (CSF_AL|CSF_AE|CSF_NM|CSF_OFF|CSF_ST|CSF_P0|CSF_P1|CSF_RE))) &&
                        (!(sigFlags & (SF_TQ|SF_AQ|SF_ARQ|SF_SQ|SF_RQ))) ) {
                        play_hour_sound(compHour);
                    }
                    sigFlags |= SF_HD;
                }
            } else {
                sigFlags &= ~SF_HD;
            }
        }

        // Now act on queue determination:
        // 1. Timer: Interrupts sequences and other signals (alarm, reminder)
        // 2./3. Alarm & Reminder do not interrupt sequences
        if(sigFlags & SF_TQ) {
            uint32_t t = isSignalPlaying();
            play_file("/timer.mp3", PA_SIGNAL|PA_TMR|PA_INTSPKR|PA_INTRMUS|PA_ALLOWSD);
            sigFlags &= ~SF_TQ;
            // Re-queue alarm if it was playing (unless user already pushed down ENTER)
            if((t & PA_ALARM) && (!(csf & CSF_AE))) {
                sigFlags |= SF_ARQ;
                if(t & PA_LOOP) sigFlags |= SF_ALQ;
            }
            // Re-queue reminder if it was playing
            if(t & PA_REM) sigFlags |= SF_RQ;
        } else if(!(csf & (CSF_ST|CSF_P0|CSF_P1|CSF_RE))) {
            if(!isSignalPlaying()) {
                if(sigFlags & (SF_AQ|SF_ARQ)) {
                    // SF_ARQ: Re-queue alarm (original and snoozed) after interruption
                    // Extended: Skip re-queuing if looped Alarm expired in the meantime (detected by
                    // alarmPlaying=0 [remember: not cleared when alarm sound is interrupted!]) and
                    // ALQ=1 (= PA_LOOP).
                    // A non-looped sample is repeated if re-queued: alarmPlaying=0 and ALQ=0.
                    // (Legacy: Repeat alarm playback if re-queued; caught by !(alf & ALF_ADV))
                    if((sigFlags & SF_AQ) || alarmPlaying || (!(sigFlags & SF_ALQ)) || (!(alf & ALF_ADV))) {
                        unsigned long ap = play_alarm_sound();
                        if(sigFlags & SF_AQ) {
                            alarmPlaying = ap;
                            origAlarmStart = millisNonZero();
                            sendAlarmNetWorkMsg();
                            if(ETTOalarm) {
                                setTTOUTpin(HIGH);
                                ETTOAlmNow = millisNonZero();
                            }
                        }
                        if(alf & ALF_ADV) csf |= CSF_AL;
                        else              alarmPlaying = ap;   // For legacy, repeat playback in full
                        snoozeNow = 0;
                    }
                    sigFlags &= ~(SF_AQ|SF_ARQ|SF_ALQ|SF_SQ);
                } else if(sigFlags & SF_SQ) {
                    sigFlags &= ~SF_SQ;
                    alarmPlaying = play_alarm_sound();
                    csf |= CSF_AL;
                } else if(sigFlags & SF_RQ) {
                    sigFlags &= ~SF_RQ;
                    play_file("/reminder.mp3", PA_SIGNAL|PA_REM|PA_INTSPKR|PA_INTRMUS|PA_ALLOWSD|PA_DYNVOL);
                }
            }
        }

        // Handle Auto-NightMode

        // Manually switching NM pauses automatic for 30 mins
        if(manualNightMode >= 0 && (millis() - manualNMNow > 30*60*1000)) {
            manualNightMode = -1;
            // Re-evaluate auto-nm immediately
            forceReEvalANM = true;
        }
        
        if(autoNightMode && (manualNightMode < 0)) {
            if(gdtl.minute() == 0 || forceReEvalANM) {
                if(!autoNMDone || forceReEvalANM) {
                    uint32_t myField;
                    if(!autoNightModeMode) {
                        myField = autoNMdailyPreset;
                    } else {
                        const uint32_t *myFieldPtr = autoNMPresets[autoNightModeMode - 1];
                        myField = myFieldPtr[bttfnDateBuf[7]];
                    }                       
                    if(myField & (1 << (23 - gdtl.hour()))) {
                        nightModeOn();
                        timedNightMode = 1;
                    } else {
                        #ifdef HAVE_LIGHT
                        switchNMoff = true;
                        #else
                        nightModeOff();
                        #endif
                        timedNightMode = 0;
                    }
                    autoNMDone = true;
                }
            } else {
                autoNMDone = false;
            }
            forceReEvalANM = false;
        }
        #ifdef HAVE_LIGHT
        // Light sensor overrules scheduled NM only in non-NightMode periods
        if((sgf & SGF_ULightSens) && (manualNightMode < 0) && (timedNightMode < 1)) {
            int32_t myLux = lightSens.readLux();
            if(myLux >= 0) {
                if(myLux > luxLimit) {
                    sensorNightMode = 0;
                    switchNMoff = true;
                } else {
                    sensorNightMode = 1;
                    nightModeOn();
                }
            } else {
                // Bad lux (probably by sensor overload), switch NM off
                sensorNightMode = -1;
                switchNMoff = true;
            }
        }
        if(switchNMoff) {
            if(sensorNightMode < 1) nightModeOff();
        }
        #endif

    }

    #ifdef HAVE_REMOTE
    updAndDispRemoteSpeed();  // 1ms
    #endif

    y = digitalRead(SECONDS_IN_PIN);
    if((y == x) && !postHSecChangeBusy) {

        bool didUpdSpeedo = false;

        millisNow = millis();

        // Less timing critical stuff goes here:
        // (Will be skipped in current iteration if
        // seconds change is detected)

        // TTOUT alarm signalling timeout
        if(ETTOAlmNow && (millisNow - ETTOAlmNow >= ETTOAlmDur)) {
            ETTOAlmNow = 0;
            setTTOUTpin(LOW);
        }
    
        // Stop alarm after alarmPlayDur or if non-looped alarm sound ran out.
        // In Extended mode, this timeout is our last resort if the user doesn't
        // press or hold ENTER, and the sound is looped. If it is not
        // looped, alarmPlaying is always zero, but ALF_RANOUT will become 1.
        // If CSF_AE is set, the user already pushed down ENTER while CSF_AL
        // was set, so we let ENTER press/hold do its job instead.
        // (In legacy mode, this is only used for our default looped sound; 
        // a user sound is played one-shot, no timeout (alarmPlaying zero,
        // ALF_RANOUT never set).)
        if((alarmPlaying && (millisNow - alarmPlaying >= alarmPlayDur)) || (alf & ALF_RANOUT)) {
            if(!(csf & CSF_AE)) {
                // alarmPlaying and ALF_RANOUT are cleared in stopAlarm(),
                // CSF_AL flag is cleared when audio actually stops which
                // is either immediately or at the end of a loop-playback
                stopAlarm(!!(alf & ALF_HS));
                // Auto-snooze for one hour
                if((alf & (ALF_SNOOZE|ALF_ASNOOZE)) == (ALF_SNOOZE|ALF_ASNOOZE)) {
                    if(origAlarmStart && (millisNow - origAlarmStart < 60*60*1000)) {
                        snoozeNow = millisNonZero();
                    } else {
                        origAlarmStart = 0;
                    }
                }
            }
        }

        // Handle Remote
        #ifdef HAVE_REMOTE
        /*
        if(!!(csf & CSF_RSM) != bttfnOldRemoteSpeedMaster) {
            bttfnOldRemoteSpeedMaster = !!(csf & CSF_RSM);
            if(csf & CSF_RSM) {
                // Remote became speed master:
                // useRotEnc, dispRotEnc, dispGPSSpeed, dispTemp already "false" at this point
                // Speedo will be set up in updAndDispRemoteSpeed().
                // Anything else here?
            } else {
                // Remote is no longer speed master
                // useRotEnc, dispRotEnc, dispGPSSpeed, dispTemp already re-set at this point
                // rotEnc was reset; speed or temp was displayed
                // Anything else here?
            }
        }
        */
        if(csf & CSF_RSM) {
            //updAndDispRemoteSpeed();  // Move this up for smoother updates
            if(bttfnRemCurSpd != bttfnRemCurSpdOld) {
                if(!(csf & (CSF_OFF|CSF_P0|CSF_P1|CSF_RE))) {
                    startBeepTimer();
                }
                bttfnRemCurSpdOld = bttfnRemCurSpd;
            }
            if(bttfnRemCurSpd >= 88) {
                checkForSpeedTT(false, true);
            } else if(bttfnRemCurSpd < 10) {
                GPSabove88 = false;
            }
        }
        #endif

        // Handle RotEnc
        #ifdef HAVE_RE   // Not CSF_RE here; RotEnc is reset at start of RE (if no P2)
        if((sgf & SGF_URotEnc) && (!(csf & (CSF_OFF|CSF_ST|CSF_P0|CSF_P1|CSF_P2)))) {
            fakeSpeed = rotEnc.updateFakeSpeed();
            if(fakeSpeed != oldFSpd) {
                if((fakeSpeed >= 0) && (!(csf & CSF_RE))) {
                    startBeepTimer();
                }
                oldFSpd = fakeSpeed;
            }
            displayGPSorRESpeed();
            if(fakeSpeed >= 88) {
                checkForSpeedTT(!!(sgf & SGF_DispRotEnc), false);
            } else if(!fakeSpeed) {   // Is reset in P2, but if during TT Remote
                GPSabove88 = false;   // took over, P2 does not reset this.
            }
        }
        if(sgf & SGF_URotEncVol) {
            int oldVol = aud_state.curVolume;
            aud_state.curVolume = rotEncVol->updateVolume(aud_state.curVolume, false);
            if(oldVol != aud_state.curVolume) {
                storeCurVolume();
                volChangedNow = millisNonZero();
                // Let audio_loop take care of updating MP status
            }
        }
        #endif

        millisNow = millis();
        
        // Read GPS, and display GPS speed
        #ifdef HAVE_GPS
        if(sgf & SGF_UGPS) {
            if(millis64() >= lastLoopGPS) {
                lastLoopGPS += (uint64_t)GPSupdateFreq;
                // call loop with doDelay true; delay not needed but
                // this causes a call of audio_loop() which is good
                myGPS.loop(true);

                // Auto-TT on GPS-88mph only if RotEnc/Remote are not source of displayed speed
                if((!(sgf & SGF_DispRotEnc)) && (!(csf & CSF_RSM))) {
                    displayGPSorRESpeed(true);
                    #ifdef NOT_MY_RESPONSIBILITY
                    if(myGPS.getSpeed() >= 88) {
                        checkForSpeedTT(true, false);
                    } else if(myGPS.getSpeed() < 10) {
                        GPSabove88 = false;
                    }
                    #endif
                }
            #ifdef HAVE_REMOTE
            } else if(remoteWasMaster) {
                displayGPSorRESpeed(true);
            #endif
            }
            
        }
        #endif
        
        // Power management: CPU speed
        // Can only reduce when GPS is not used, WiFi is off and no sound playing
        if((!(csf & CSF_PWRLOW)) &&
           (wifiIsOff || wifiAPIsOff) && 
           #ifdef HAVE_GPS
           (!(sgf & SGF_UGPS)) &&
           #endif
           checkAudioDone() && 
           (millisNow - pwrFullNow >= 5*60*1000)) {
            
            setCpuFrequencyMhz(80);
            csf |= CSF_PWRLOW;
            #ifdef TC_DBG_GEN
            Serial.printf("Reduced CPU speed to %d\n", getCpuFrequencyMhz());
            #endif
        }

        // Beep auto modes
        if(beepTimer && (millisNow - beepTimer > beepTimeout)) {
            beepTimer = 0;
            muteBeep = true;
        }

        // Update sensors

        #ifdef HAVE_TEMP
        updateTemperature();
        didUpdSpeedo = dispTemperature();
        #endif

        // SGF_SpAlwsOn can only be set if SGF_USpeedoDisp is set
        if((sgf & SGF_SpAlwsOn) && !didUpdSpeedo && (!(sgf & (SGF_DispGPSSpd|SGF_DispRotEnc))) && (!(csf & CSF_RSM))) {
            dispIdleZero();
        }
        
        #ifdef HAVE_LIGHT
        if((sgf & SGF_ULightSens) && (millisNow - lastLoopLight >= 3000)) {
            lastLoopLight = millisNow;
            lightSens.loop();
        }
        #endif

        // End of OTPR for PCF2129
        #ifdef HAVE_PCF2129
        if(OTPRinProgress) {
            if(millisNow - OTPRStarted > 100) {
                rtc.OTPRefresh(false);
                OTPRinProgress = false;
                OTPRDoneNow = millisNow;
            }
        }
        #endif
    }

    bttfn_notify_speed();
    #ifdef SERVOSPEEDO
    speedo.speedoSLoop();
    #endif

    y = digitalRead(SECONDS_IN_PIN);
    if(y != x) {

        // Actual clock stuff
      
        if(y == 0) {

            uint8_t minNext;

            // Set colon
            destinationTime.setColon(true);
            presentTime.setColon(true);
            departedTime.setColon(true);

            // Play "annoying beep"(tm)
            play_beep();

            // Prepare for time re-adjustment through NTP/GPS

            if(!haveAuthTime) {
                authTimeExpired = true;
                if((couldHaveAuthTime & 2) && !NTPLookupFail) {
                    blockWiFiSTAPS = true;
                }
            } else if(millis() - lastAuthTime >= 7*24*60*60*1000) {
                authTimeExpired = true;
            }

            // Expire syncTrigger to allow PS any time later
            // if syncing keeps failing. (7 mins to be well
            // below minimum PS timeout)
            if(syncTrigger && (millis() - syncTrigger > 7*60*1000)) {
                syncTrigger = 0;
            }

            #ifdef HAVE_GPS
            bool GPShasTime = gpsHaveTime();
            #else
            bool GPShasTime = false;
            #endif

            // Read RTC for UTC time
            myrtcnow(gdtu);

            // Re-adjust time periodically through NTP/GPS
            //
            // This is normally done hourly during hour:01 and hour:02.
            // Exception to time rule: If there is no authTime yet, try syncing every
            // resyncInt+1/2 minutes (unless lookup of the NTP server failed) or
            // whenever GPS has time; or if syncTrigger is set (keypad "7").
            // (itsTime)
            //
            // Try NTP via WiFi (doWiFi) if user configured a network and a server AND
            //   -- if WiFi is connected (duh!), OR
            //   -- if
            //          --- WiFi was connected and now off OR currently in AP-mode AND
            //          --- User checked "Periodic reconnection attempts" in CP AND
            //          --- authTime has expired (after 7 days) or we never had authtime AND
            //          --- it is night (0-6am)
            //      This triggers a re-connect (frozen display) but only once every
            //      15/90 minutes (see wifiOn) during night time until a time sync
            //      succeeds or the number of attempts exceeds a certain amount.
            // - In any case, do not interrupt any running sequences.
            //
            // Note: If ntp is possible (have server & network), and DNS lookup didn't 
            //       fail, WiFi power-saving is blocked until once auth time is received.
            //       (blockWiFiSTAPS)

            bool itsTime = false;
            bool doWiFi = false;
            
            if(couldHaveAuthTime && (!(csf & (CSF_ST|CSF_P0|CSF_P1|CSF_RE|CSF_P2)))) {

                itsTime = ( (gdtu.minute() == 1) ||
                            (gdtu.minute() == 2) ||
                            (!haveAuthTime && 
                              ( GPShasTime ||
                                ( !NTPLookupFail &&
                                  ( ((gdtu.minute() % resyncInt) == 1) || 
                                    ((gdtu.minute() % resyncInt) == 2) )
                                )
                              )
                            )                    ||
                            (syncTrigger &&
                             gdtu.second() == 35
                            )
                          );
            
                if(itsTime && !GPShasTime) {
                    doWiFi = !!(couldHaveAuthTime & 2) &&              // if NTP is possible AND
                             ( 
                               (!wifiIsOff && !wifiInAPMode)     ||    //   if WiFi-STA is on,                           OR
                               /* // This is now covered by blockWiFiSTAPS
                               ( wifiIsOff      &&                     //   if WiFi-STA is off (after being connected), 
                                 !haveAuthTime  &&                     //      but no authtime, 
                                 keypadIsIdle() &&                     //      and keypad is idle (no press for >2mins)
                                 checkAudioFree())               ||    //      and no audio(ex.beep) is being played     OR
                               */
                               ( (wifiIsOff ||                         //   if WiFi-STA is off (after being connected),
                                  (wifiInAPMode && doAPretry)) &&      //                      or in fall-back AP-mode
                                 authTimeExpired               &&      //      and authtime expired (or we never had any)
                                 checkAudioFree()              &&      //      and no audio (ex.beep) being played
                                 keypadIsIdle()                &&      //      and keypad is idle (no press for >2mins)
                                 (lastHour <= 6)                       //      during night-time
                               )
                             );
                }
            }
            
            #ifdef TC_DBG_TIME
            if(gdtu.second() == 35) {
                Serial.printf("%s%d %d %d %d %d\n", funcName, couldHaveAuthTime, itsTime, doWiFi, haveAuthTime, syncTrigger ? 1 : 0);
            }
            #endif
            
            if(itsTime && (GPShasTime || doWiFi)) {

                if(!autoReadjust) {

                    uint64_t oldT = 0;

                    if(timeDifference) {
                        oldT = dateToMins(gdtu.year(), gdtu.month(), gdtu.day(), gdtu.hour(), gdtu.minute());
                    }

                    // Note that the following call will fail if getNTPtime reconnects
                    // WiFi; no current NTP time stamp will be available. Repeated calls
                    // will eventually succeed.

                    if(getNTPOrGPSTime(haveAuthTime, gdtu, false, doWiFi)) {

                        autoReadjust = true;
                        resyncInt = 5;
                        syncTrigger = 0;

                        haveAuthTime = true;
                        lastAuthTime = millis();
                        lastAuthTime64 = millis64();
                        authTimeExpired = false;
                        blockWiFiSTAPS = false;

                        // We have just adjusted, don't do it again below
                        lastYear = gdtu.year();

                        #ifdef TC_DBG_TIME
                        Serial.printf("%sRTC re-adjusted using NTP or GPS\n", funcName);
                        #endif

                        // Correct timeDifference by adjustment delta
                        if(timeDifference) {
                            uint64_t newT = dateToMins(gdtu.year(), gdtu.month(), gdtu.day(), gdtu.hour(), gdtu.minute());
                            if(newT != oldT) {
                                if(timeDiffUp) {
                                    oldT += timeDifference;
                                } else {
                                    oldT -= timeDifference;
                                }
                                if(oldT > newT) {
                                    timeDifference = oldT - newT;
                                    timeDiffUp = true;
                                } else {
                                    timeDifference = newT - oldT;
                                    timeDiffUp = false;
                                }
                                if(timetravelPersistent) {
                                    presentTime.savePending();
                                }
                            }
                        }

                    } else {

                        #ifdef TC_DBG_TIME
                        Serial.printf("%sRTC re-adjustment via NTP/GPS failed\n", funcName);
                        #endif

                    }

                } 

            } else {
                
                autoReadjust = false;

                // If GPS is used for time, resyncInt is possibly set to 2 during boot;
                // reset it to 5 after 5 minutes since boot.
                if(resyncInt != 5) {
                    if(millis() > 5*60*1000) {
                        resyncInt = 5;
                    }
                }

            }

            // Detect and handle year changes

            {
                uint16_t thisYear = gdtu.year();

                if( (thisYear != lastYear) || (thisYear > 9999) ) {

                    uint16_t rtcYear;
                    int16_t yOffs = 0;
    
                    if(thisYear > 9999) {
                        #ifdef TC_DBG_TIME
                        Serial.printf("%sRollover 9999->1 detected\n", funcName);
                        #endif
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
