CircuitSetup/Time-Circuits-Display/Software/src/input.cpp

/*
 * -------------------------------------------------------------------
 * CircuitSetup.us Time Circuits Display
 * (C) 2022-2026 Thomas Winischhofer (A10001986)
 * https://github.com/realA10001986/Time-Circuits-Display
 * https://tcd.out-a-ti.me
 *
 * Keypad_I2C Class, TCButton Class: I2C-Keypad and Button handling
 * 
 * TCRotEnc: Rotary Encoder handling:
 * Supports Adafruit 4991/5880, DuPPA I2CEncoder 2.1, DFRobot Gravity 360.
 * For speed, the encoders must be set to their default i2c address
 * (DuPPA I2CEncoder 2.1 must be set to i2c address 0x01 (A0 closed)).
 * For volume, the encoders must be configured as follows:
 * - Ada4991/5880: A0 closed (i2c address 0x37)
 * - DFRobot Gravity 360: SW1 off, SW2 on (i2c address 0x55)
 * - DuPPA I2CEncoder 2.1: A0 and A1 closed (i2c address 0x03)
 * 
 * Keypad part based on concepts by M. Stanley & A. Brevig
 * -------------------------------------------------------------------
 * License: Modified MIT NON-AI
 * 
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
 * Links inside the Software pointing to the original source must not 
 * be changed or removed.
 *
 * In addition, the following restrictions apply:
 * 
 * 1. The Software and any modifications made to it may not be used 
 * for the purpose of training or improving machine learning algorithms, 
 * including but not limited to artificial intelligence, natural 
 * language processing, or data mining. This condition applies to any 
 * derivatives, modifications, or updates based on the Software code. 
 * Any usage of the Software in an AI-training dataset is considered a 
 * breach of this License.
 *
 * 2. The Software may not be included in any dataset used for 
 * training or improving machine learning algorithms, including but 
 * not limited to artificial intelligence, natural language processing, 
 * or data mining.
 *
 * 3. Any person or organization found to be in violation of these 
 * restrictions will be subject to legal action and may be held liable 
 * for any damages resulting from such use.
 *
 * 4. The source code and the binary form, and any modifications made 
 * to them may not be used for the purpose of training or improving 
 * machine learning algorithms, including but not limited to artificial
 * intelligence, natural language processing, or data mining. This 
 * condition applies to any derivatives, modifications, or updates 
 * based on the Software code. Any usage of the source code or the 
 * binary form in an AI-training dataset is considered a breach of 
 * this License.

 * THE SOFTWARE IS PROVIDED "AS IS", WITHOUT WARRANTY OF ANY KIND, 
 * EXPRESS OR IMPLIED, INCLUDING BUT NOT LIMITED TO THE WARRANTIES OF 
 * MERCHANTABILITY, FITNESS FOR A PARTICULAR PURPOSE AND NONINFRINGEMENT. 
 * IN NO EVENT SHALL THE AUTHORS OR COPYRIGHT HOLDERS BE LIABLE FOR ANY 
 * CLAIM, DAMAGES OR OTHER LIABILITY, WHETHER IN AN ACTION OF CONTRACT, 
 * TORT OR OTHERWISE, ARISING FROM, OUT OF OR IN CONNECTION WITH THE 
 * SOFTWARE OR THE USE OR OTHER DEALINGS IN THE SOFTWARE.
 */

#include "tc_global.h"

#include <Arduino.h>

#include "input.h"
#include "tc_audio.h"

#define OPEN    false
#define CLOSED  true

#define MAX_ROWS  4
#define MAX_COLS  3

static void defaultDelay(int iter, unsigned long mydelay)
{
    delay(mydelay);
}

/*
 * Keypad_i2c class
 */

Keypad_I2C::Keypad_I2C(char *userKeymap, const uint8_t *row, const uint8_t *col,
                       unsigned int numRows, unsigned int numCols,
                       int address)
{
    _keymap = userKeymap;

    _rowPins = row;
    _columnPins = col;
    _rows = numRows;
    _columns = numCols;

    // Avoid crash if called with bad parms
    if(_rows > MAX_ROWS) _rows = MAX_ROWS;
    if(_columns > MAX_COLS) _columns = MAX_COLS;

    _i2caddr = address;

    _scanInterval = 10;
    _holdTime = 500;

    _keypadEventListener = NULL;

    _customDelayFunc = defaultDelay;

    _key.kState = TCKS_IDLE;
    _key.kChar = 0;
    _key.stateChanged = false;
}

// Initialize I2C
void Keypad_I2C::begin(unsigned int scanInterval, unsigned int holdTime, void (*myDelay)(int, unsigned long))
{
    _scanInterval = scanInterval;
    _holdTime = holdTime;
    
    // Set pins to power-up state
    port_write(0xff);

    // Read initial value for shadow output pin state
    Wire.requestFrom(_i2caddr, (int)1);
    _pinState = Wire.read();

    // Build rowMask for quick scanning
    _rowMask = 0;
    for(int i = 0; i < _rows; i++) {
        _rowMask |= (1 << _rowPins[i]);
    }

    _customDelayFunc = myDelay;
}

// Scan keypad and update key state
bool Keypad_I2C::scanKeypad()
{
    bool keyChanged = false;

    if((millis() - _scanTime) > _scanInterval) {
        keyChanged = scanKeys();
        _scanTime = millis();
    }

    return keyChanged;
}

/*
 * Private
 */

// Hardware scan & update key state
bool Keypad_I2C::scanKeys()
{
    uint32_t pinVals[3][MAX_COLS], rb;
    int      repeat, haveKey;
    int      maxRetry = 5;
    int      c, r, d;

    do {

        repeat = 0;
        haveKey = -1;

        for(d = 0; d < 3; d++) {

            for(c = 0; c < _columns; c++) {

                pin_write(_columnPins[c], LOW);

                Wire.requestFrom(_i2caddr, (int)1);
                if((pinVals[d][c] = Wire.read() & _rowMask) != _rowMask)
                    haveKey = c;

                pin_write(_columnPins[c], HIGH);

            }

            if(d < 2) (*_customDelayFunc)(d, 5);

        }

        for(c = 0; c < _columns; c++) {
            if((pinVals[0][c] != pinVals[1][c]) || (pinVals[0][c] != pinVals[2][c])) {
                repeat = 1;
            }
        }

    } while(repeat && maxRetry--);

    _key.stateChanged = false;

    // If we currently have an active key, advance its state
    if(_key.kState != TCKS_IDLE) {

        advanceState(!(pinVals[0][_key.kCol] & _key.kRow));

    } 

    // If _key is idle, evaluate scanning result
    if(haveKey >= 0 && _key.kState == TCKS_IDLE) {

        for(r = 0; r < _rows; r++) {
            rb = 1 << _rowPins[r];
            if(!(pinVals[0][haveKey] & rb) == CLOSED) {
                _key.kRow = rb;
                _key.kCol = haveKey;
                _key.kChar = _keymap[(r * _columns) + haveKey];
                advanceState(CLOSED);
                goto quitScan;  // bail, _key is busy
            }
        }
        
    }
    
quitScan:
    return _key.stateChanged;
}

// State machine. 
// Unlike TCButton, we do not need to debounce.
void Keypad_I2C::advanceState(bool newstate)
{
    switch(_key.kState) {
    case TCKS_IDLE:
        if(newstate == CLOSED) {
            transitionTo(TCKS_PRESSED);
            _key.startTime = millis();
        }
        break;

    case TCKS_PRESSED:
        if((millis() - _key.startTime) > _holdTime)
            transitionTo(TCKS_HOLD);
        else if(newstate == OPEN)
            transitionTo(TCKS_RELEASED);
        break;

    case TCKS_HOLD:
        if(newstate == OPEN)
            transitionTo(TCKS_RELEASED);
        break;

    case TCKS_RELEASED:
        _key.kState = TCKS_IDLE;
        break;
    }
}

void Keypad_I2C::transitionTo(KeyState nextState)
{
    _key.kState = nextState;
    _key.stateChanged = true;

    if(_keypadEventListener) {
        _keypadEventListener(_key.kChar, _key.kState);
    }
}

void Keypad_I2C::pin_write(uint8_t pinNum, bool level)
{
    uint8_t mask = 1 << pinNum;

    if(level == HIGH) {
      	_pinState |= mask;
    } else {
        _pinState &= ~mask;
    }

    port_write(_pinState);
}

void Keypad_I2C::port_write(uint8_t val)
{
    Wire.beginTransmission(_i2caddr);
    Wire.write(val);
    Wire.endTransmission();
    _pinState = val;
}


/*
 * TCButton class
 */

TCButton::TCButton(const uint8_t pin)
{
    _pin = pin;
}

// debounce: Number of millisec that have to pass by before a click is assumed stable
// press:    Number of millisec that have to pass by before a short press is detected
// lPress:   Number of millisec that have to pass by before a long press is detected
void TCButton::begin(int button_pressed, uint8_t pu_mode, const int debounceDur, const int pressDur, const int lPressDur)
{
    _buttonPressed = button_pressed;

    pinMode(_pin, pu_mode);

    _debounceDur = debounceDur;
    _pressDur = pressDur;
    _longPressDur = lPressDur;
}
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
